airdamien/FXPAN/docs/fxpan_body_fit.png

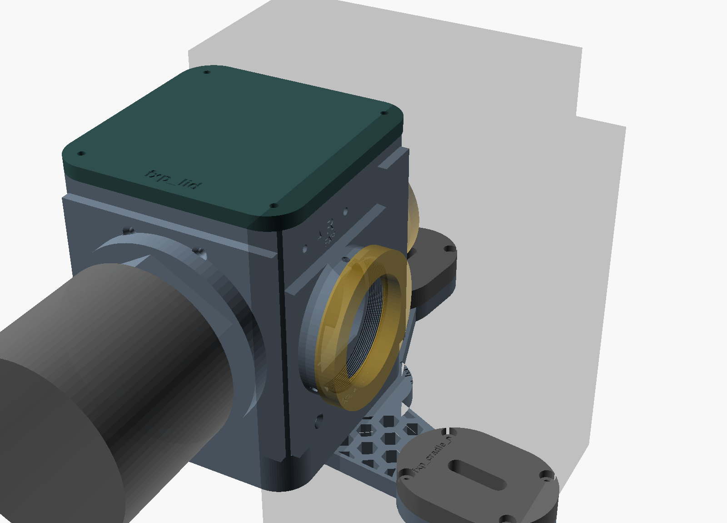
docs/fxpan_body_fit.png
