airdamien/FXPAN/docs/kraken/countryside.jpg

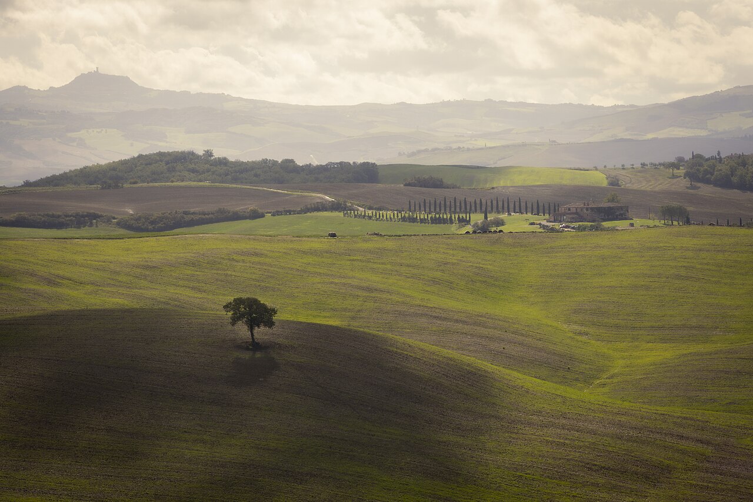
docs/kraken/countryside.jpg
