airdamien/FXPAN/docs/kraken/schlieren_paths.png

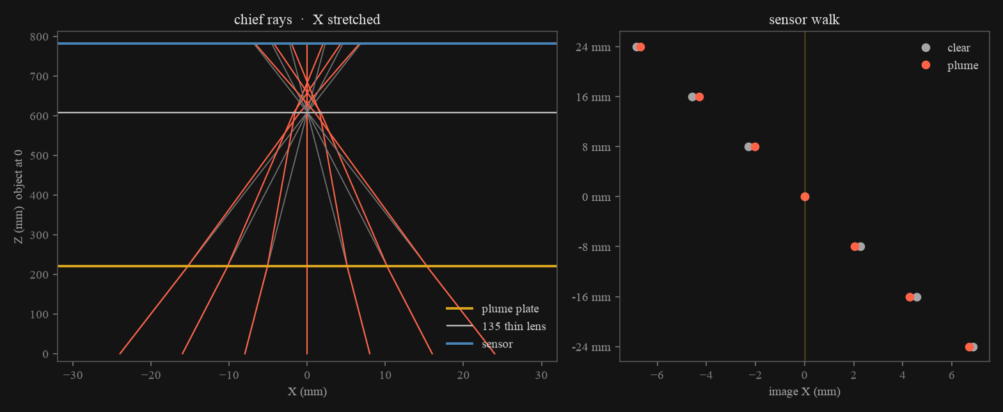
docs/kraken/schlieren_paths.png
