airdamien/FXPAN/docs/kraken/settles_bullet.jpg

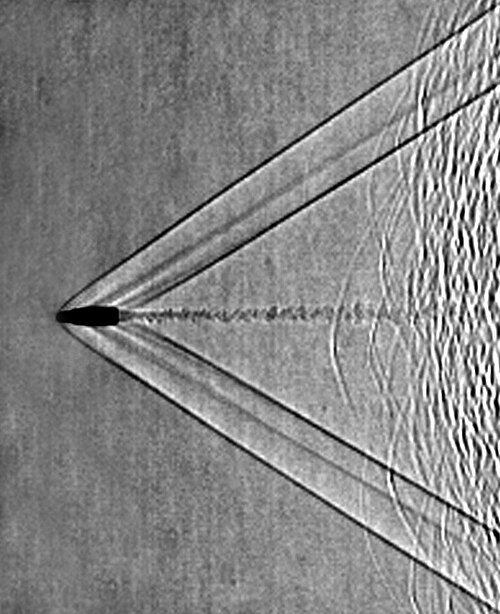
docs/kraken/settles_bullet.jpg
