airdamien/FXPAN/docs/monitor/midas-hdmi-ctp.png

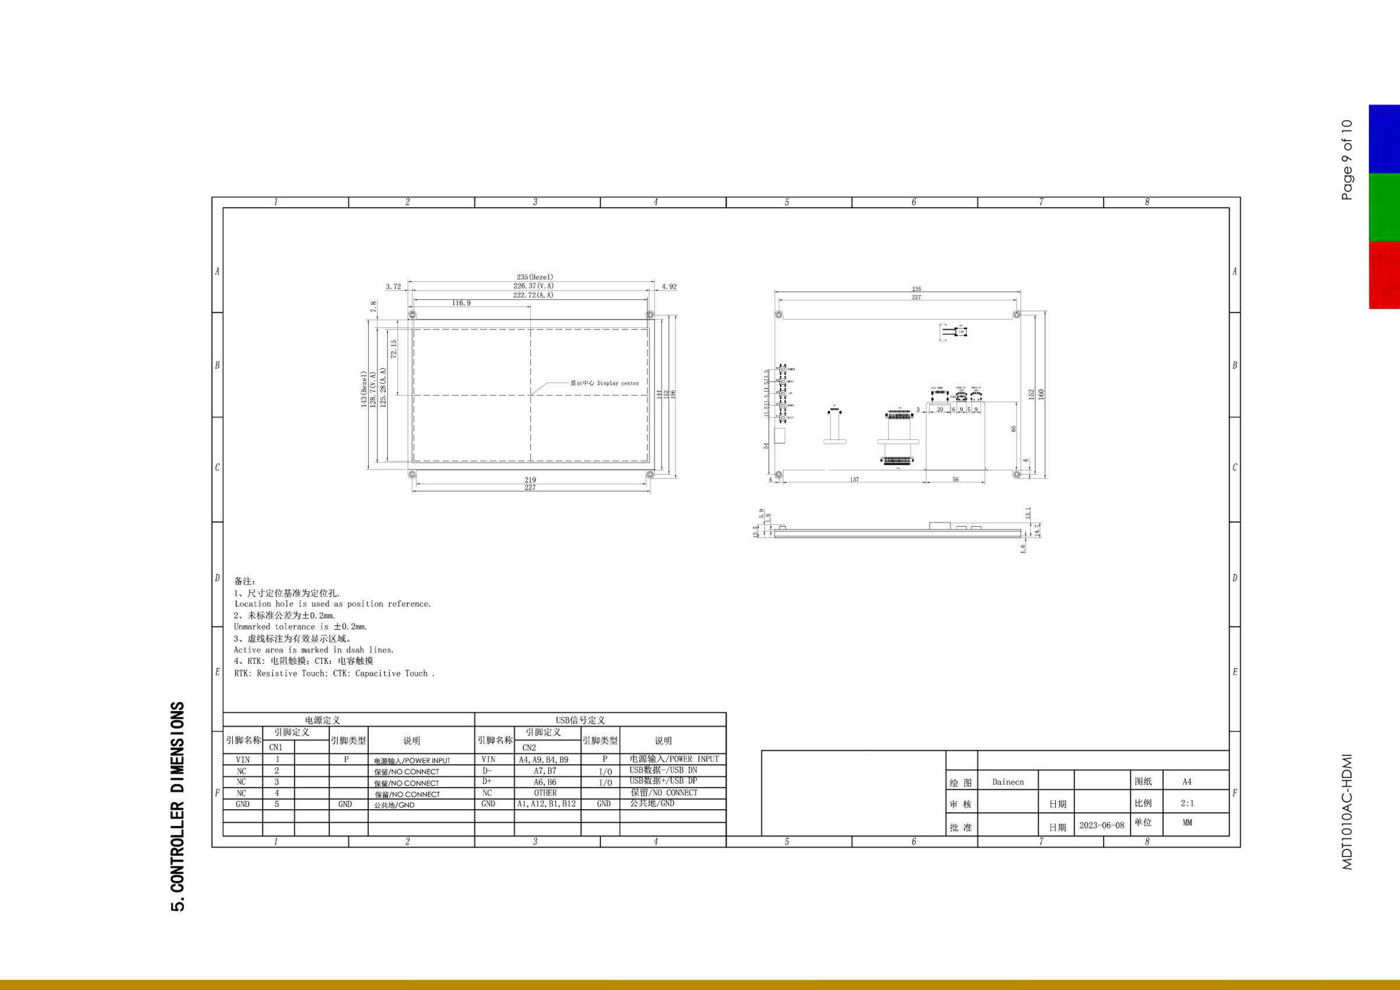
docs/monitor/midas-hdmi-ctp.png
