airdamien/FXPAN/docs/monitor/waveshare-panel.png

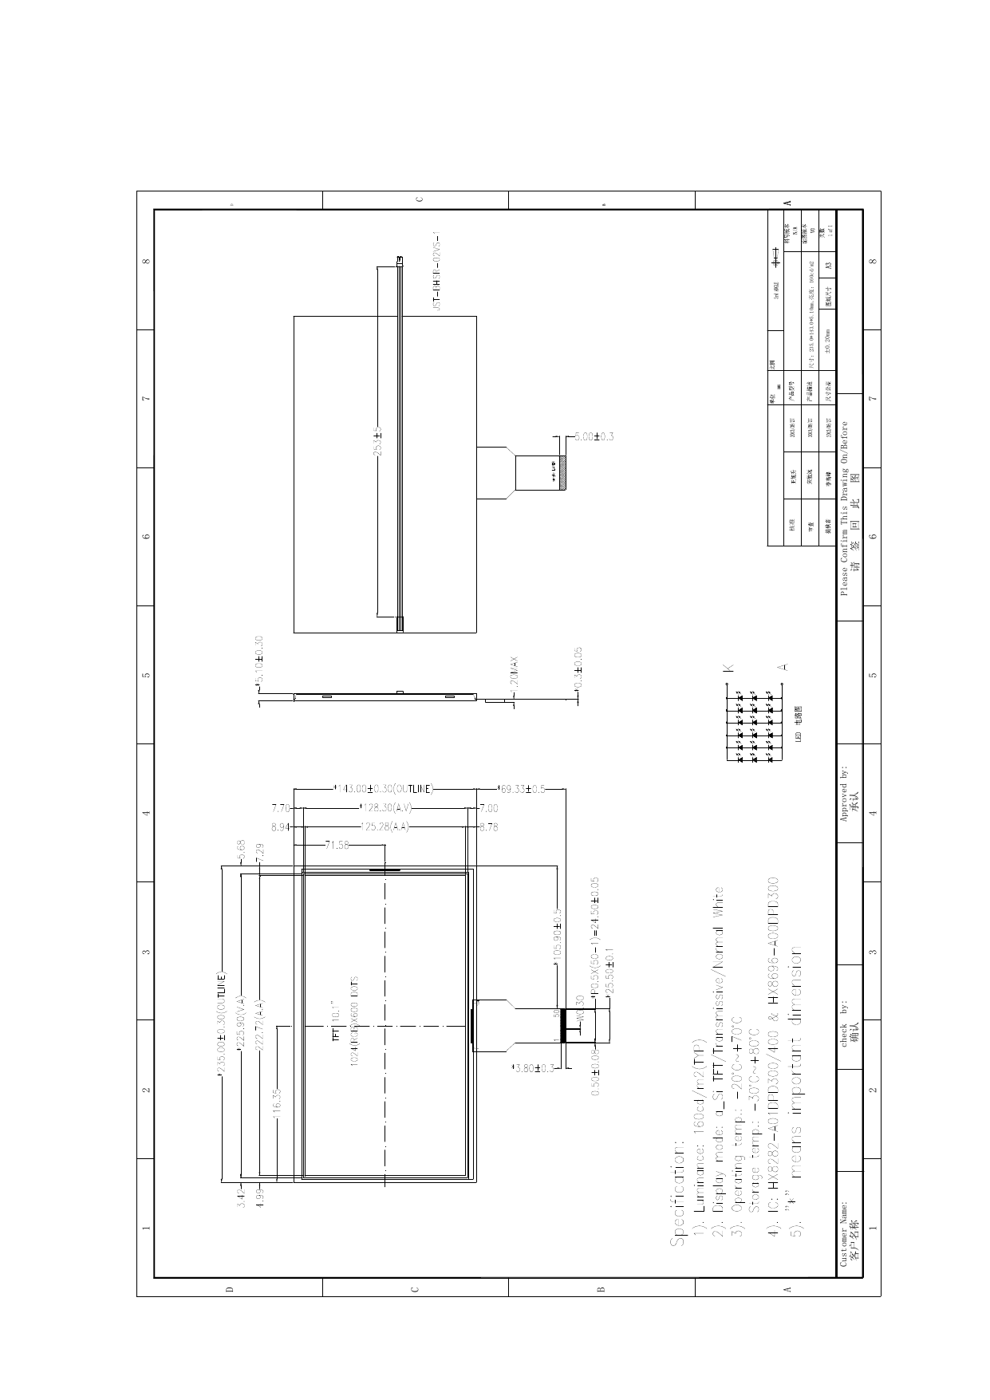
docs/monitor/waveshare-panel.png
