airdamien/FXPAN/ios/FXPAN/Samples/P_20261002195445.jpg

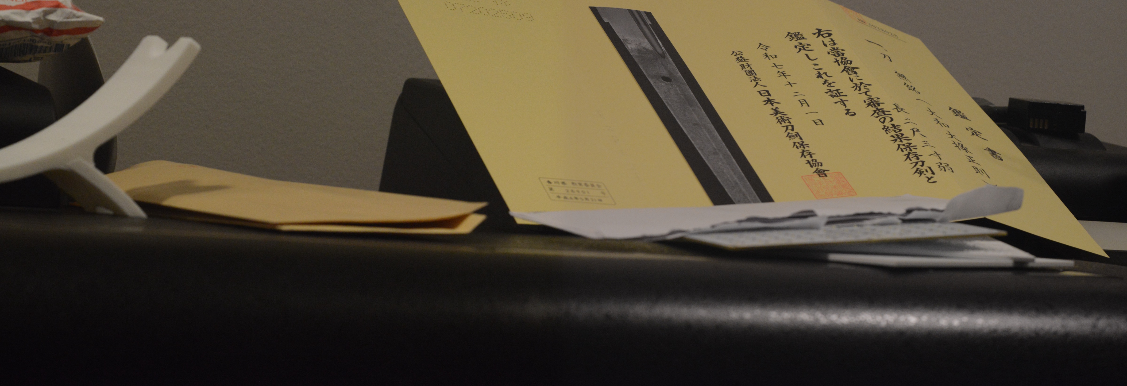
ios/FXPAN/Samples/P_20261002195445.jpg
