airdamien/FXPAN/ios/FXPAN/Samples/P_20261002201628.jpg

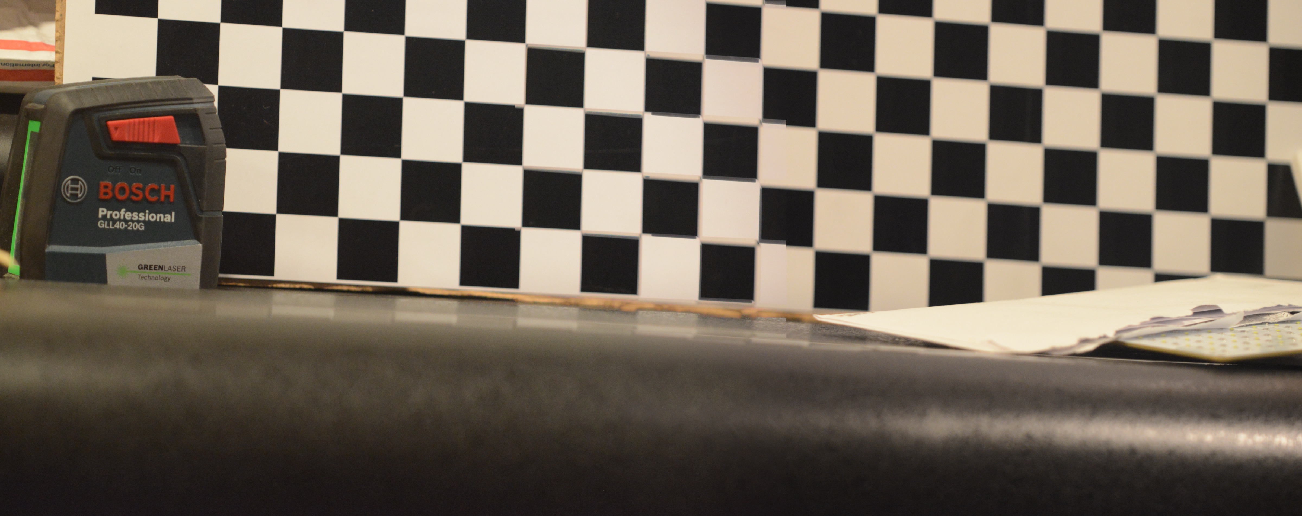
ios/FXPAN/Samples/P_20261002201628.jpg
