airdamien/FXPAN/ios/FXPAN/Samples/P_20261002201952.jpg

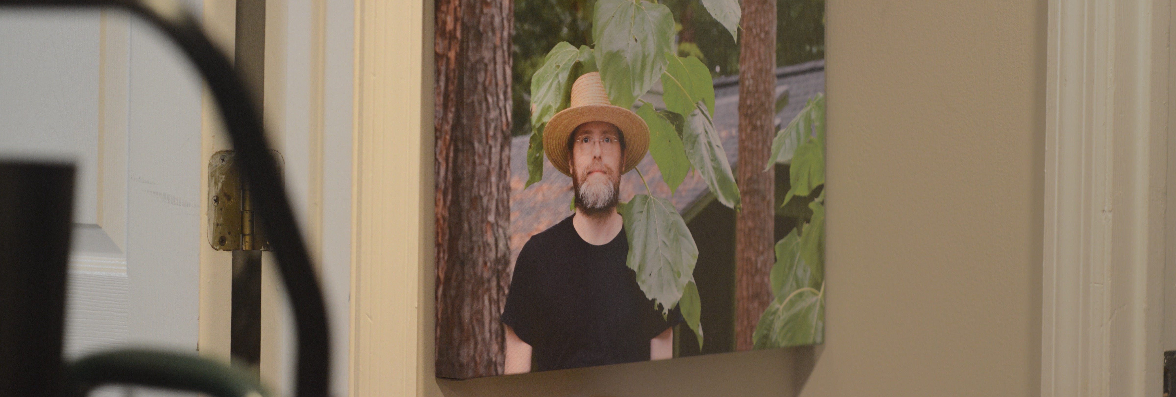
ios/FXPAN/Samples/P_20261002201952.jpg
