airdamien/FXPAN/openscad/hybrid_shift/preview.png

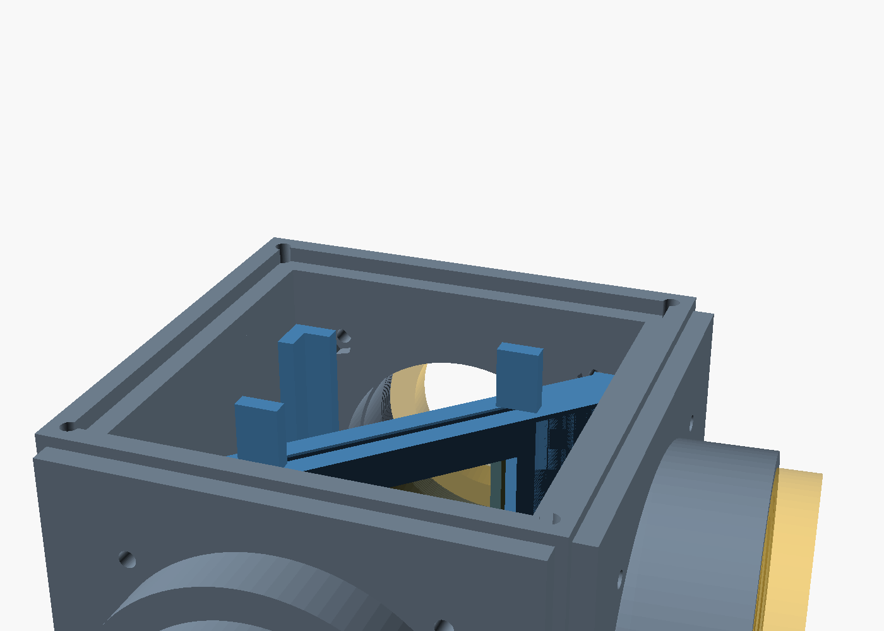
openscad/hybrid_shift/preview.png
