airdamien/FXPAN/logos/fxpan_fx_gold.stl

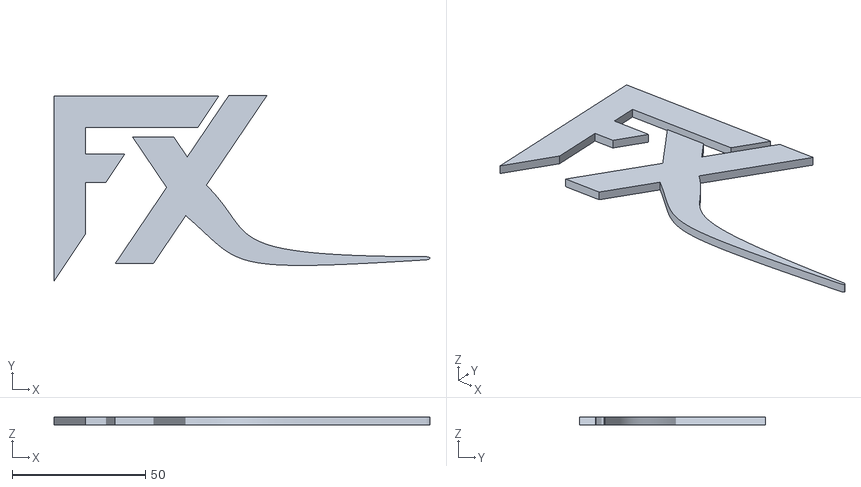
[picture p83: CAD file, 2026-09-20]
logos/fxpan_fx_gold.stl
141.0 x 69.6 x 3.00
