airdamien/FXPAN/openscad/monitor/case-bottom.stl

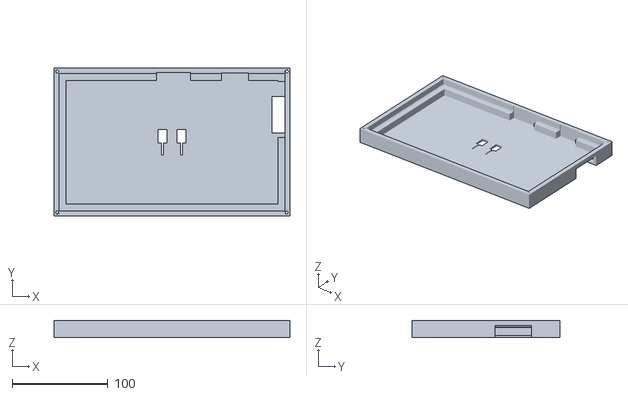
[picture p84: CAD file, 2026-09-13]
openscad/monitor/case-bottom.stl
246.1 x 154.0 x 18.2
