airdamien/FXPAN/openscad/taking_lens.stl

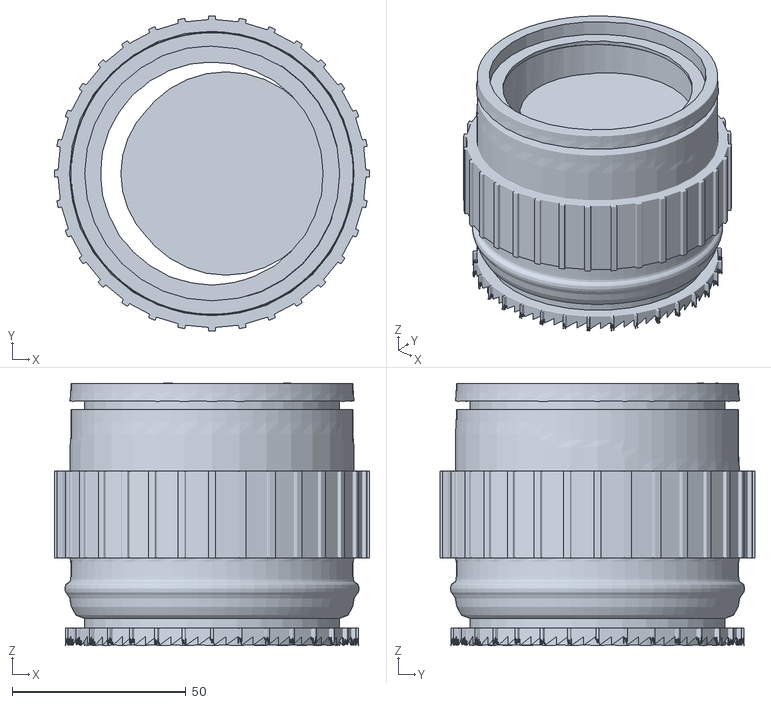
[picture p85: CAD file, 2026-09-12]
openscad/taking_lens.stl
90.8 x 90.8 x 75.7
