airdamien/FXPAN/stls/fxpan/lid.stl

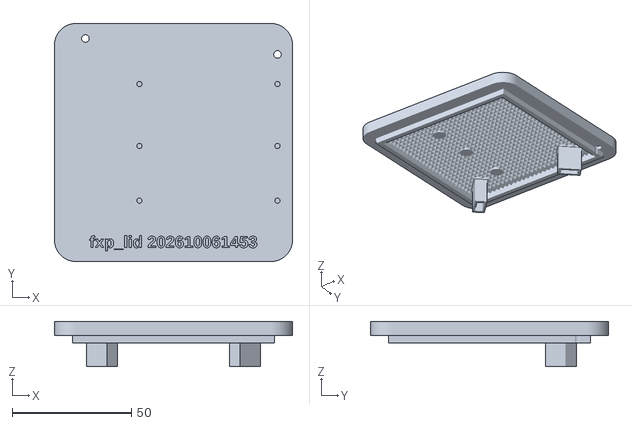
[picture p86: CAD file, 2026-10-06]
stls/fxpan/lid.stl
100.0 x 100.0 x 19.0
