airdamien/FXPAN/stls/hybrid/arm_t_s.stl

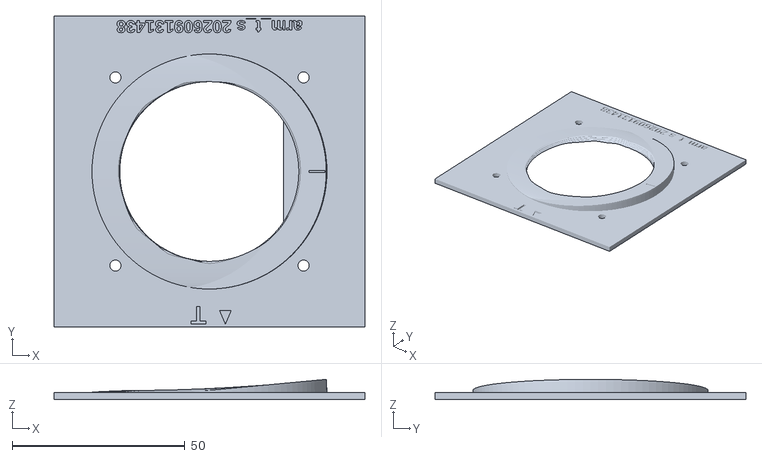
[picture p87: CAD file, 2026-09-13]
stls/hybrid/arm_t_s.stl
90.0 x 90.0 x 5.87
