airdamien/FXPAN/stls/hybrid_shift/chassis_logo.stl

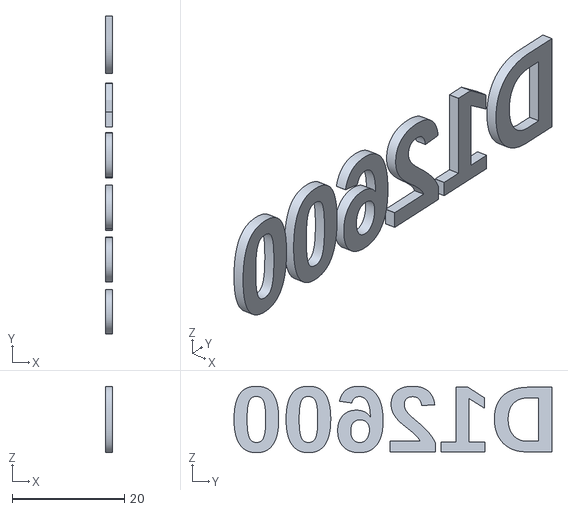
[picture p88: CAD file, 2026-09-17]
stls/hybrid_shift/chassis_logo.stl
1.30 x 56.6 x 11.8
