airdamien/FXPAN/stls/hybrid_shift_fx/stem_el180_inf.stl

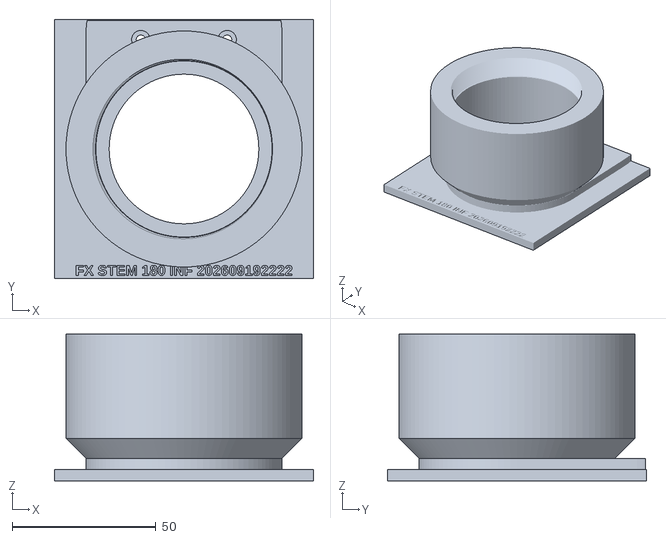
[picture p89: CAD file, 2026-09-20]
stls/hybrid_shift_fx/stem_el180_inf.stl
90.0 x 90.0 x 51.0
