airdamien/FXPAN/stls/isco/isco_clamp_nw.stl

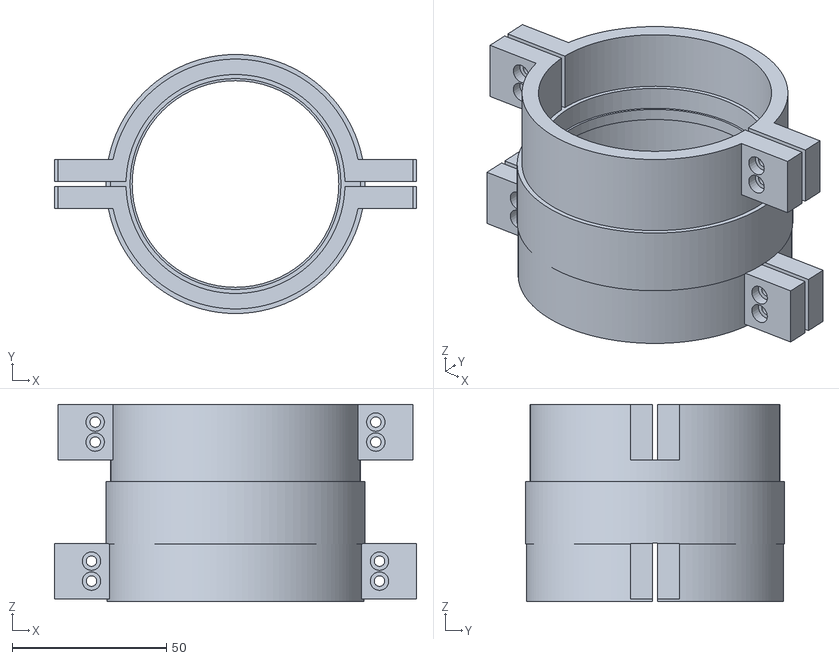
[picture p90: CAD file, 2026-09-26]
stls/isco/isco_clamp_nw.stl
117.4 x 84.0 x 64.0
