airdamien/FXPAN/stls/phone/duo_shoe.stl

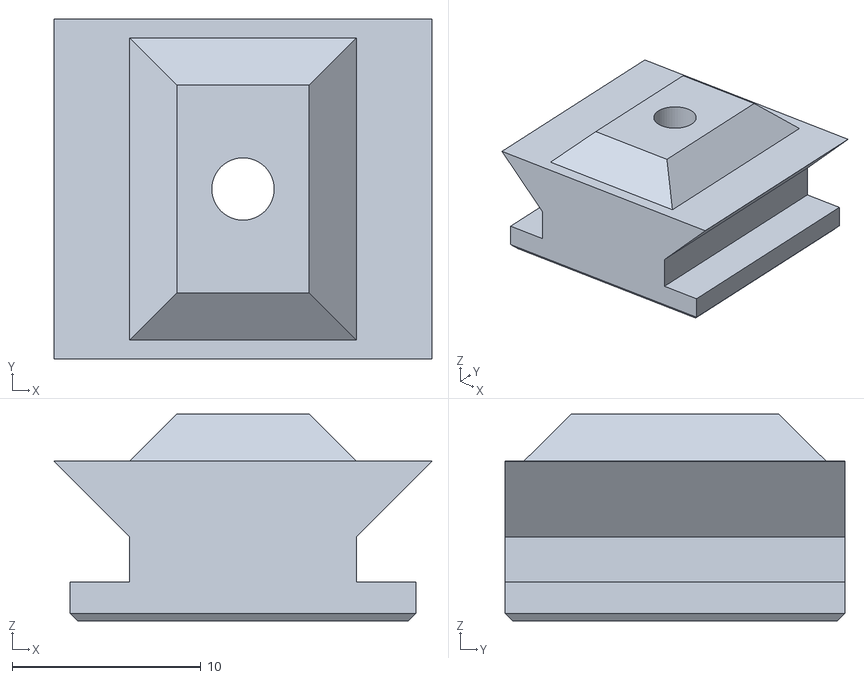
[picture p91: CAD file, 2026-10-06]
stls/phone/duo_shoe.stl
20.0 x 18.0 x 10.9
