airdamien/FXPAN/stls/tools/focus_sled.stl

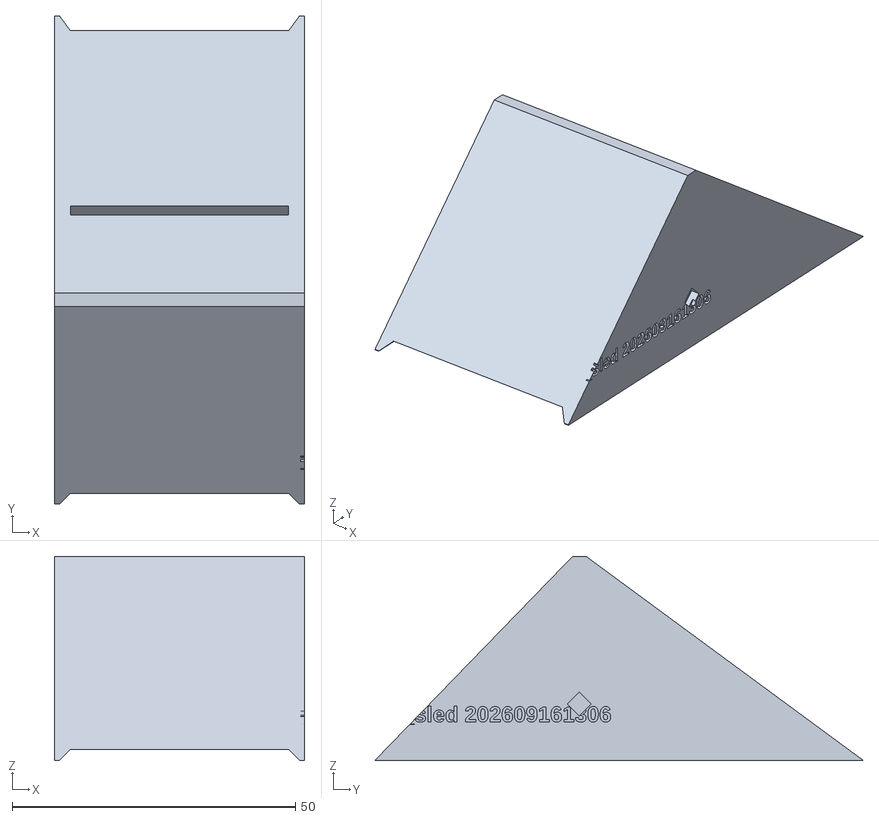
[picture p92: CAD file, 2026-09-16]
stls/tools/focus_sled.stl
44.2 x 86.1 x 36.0
