airdamien/FXPAN/stls/v/arm_r_f.stl

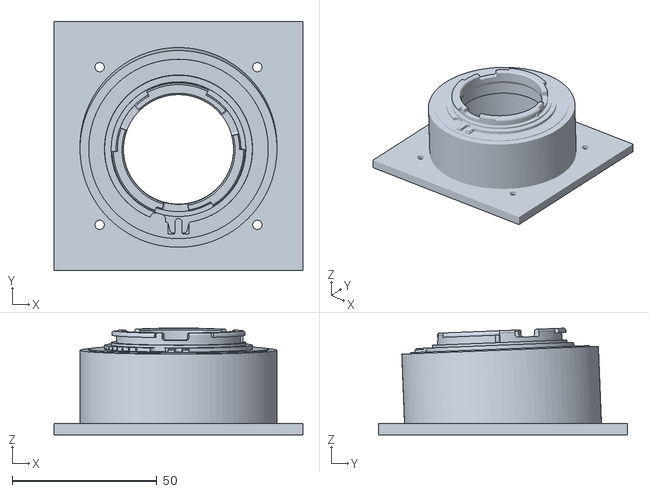
[picture p93: CAD file, 2026-09-12]
stls/v/arm_r_f.stl
86.0 x 86.0 x 36.9
