airdamien/FXPAN/logos/fxpan_outline_red.stl

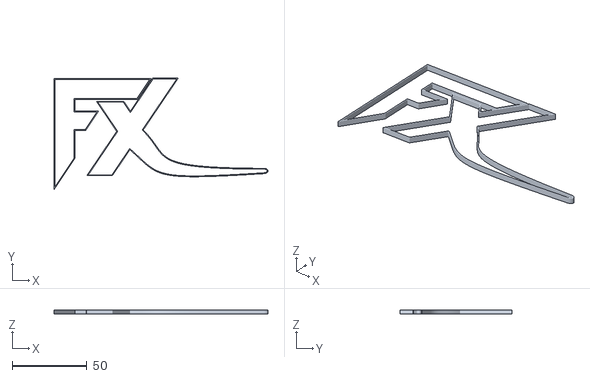
[picture p94: CAD file, 2026-09-20]
logos/fxpan_outline_red.stl
143.4 x 74.8 x 3.00
