airdamien/FXPAN/openscad/d7000_body.stl

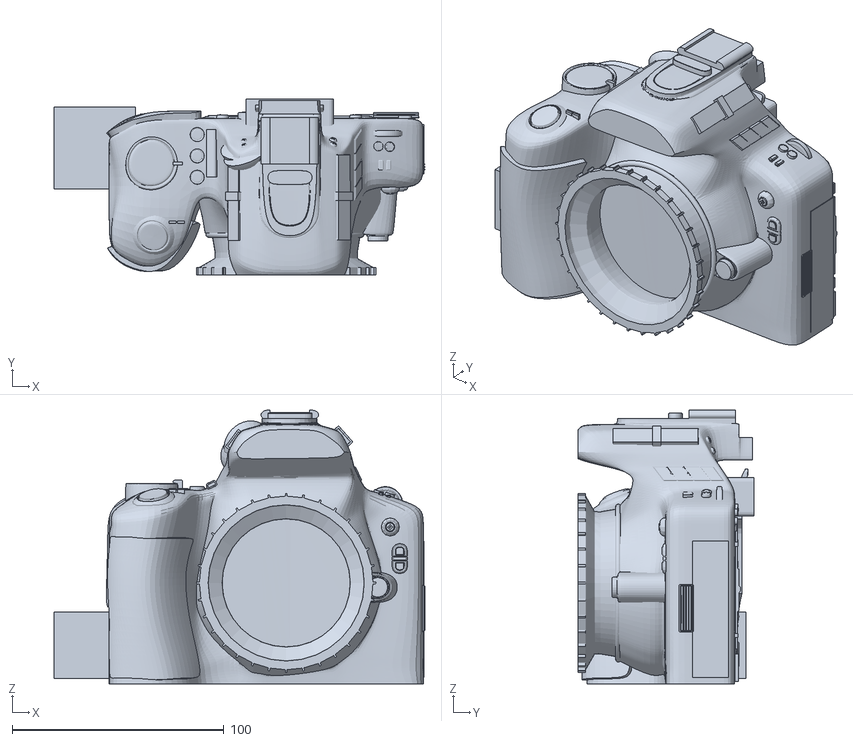
[picture p95: CAD file, 2026-09-12]
openscad/d7000_body.stl
175.0 x 82.9 x 129.1
