airdamien/FXPAN/openscad/monitor/wall_mount.stl

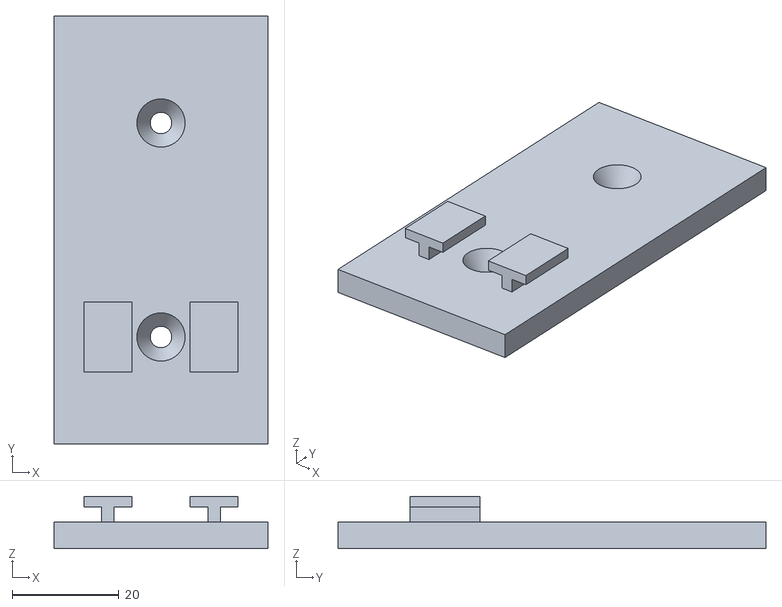
[picture p96: CAD file, 2026-09-13]
openscad/monitor/wall_mount.stl
40.0 x 80.0 x 9.76
