airdamien/FXPAN/stls/fxpan/lid_inner.stl

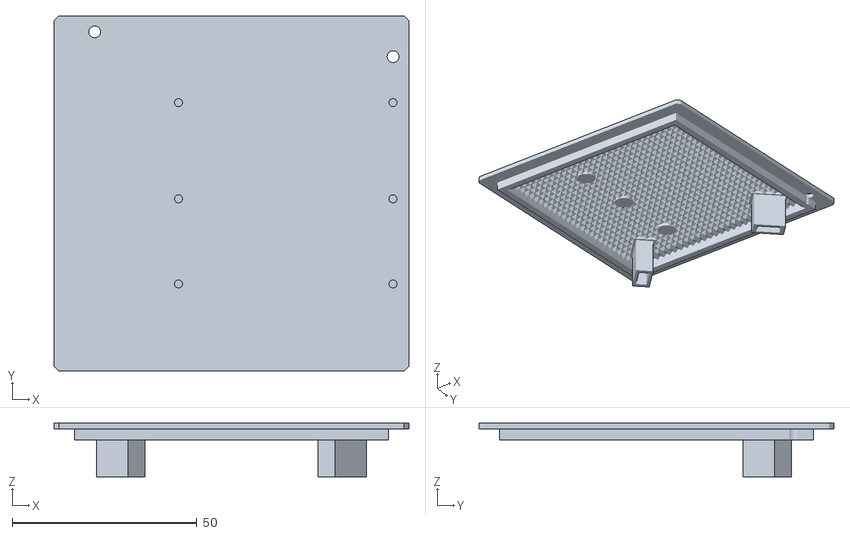
[picture p97: CAD file, 2026-10-06]
stls/fxpan/lid_inner.stl
96.0 x 96.0 x 14.6
