airdamien/FXPAN/stls/hybrid_shift/chassis_outer.stl

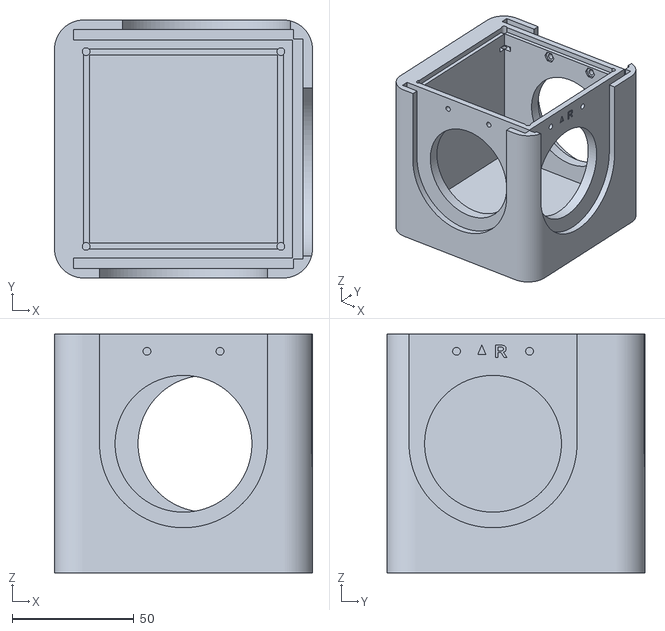
[picture p98: CAD file, 2026-09-17]
stls/hybrid_shift/chassis_outer.stl
106.0 x 106.0 x 98.0
