airdamien/FXPAN/stls/hybrid_shift_fx/stem_el180_inf_inner.stl

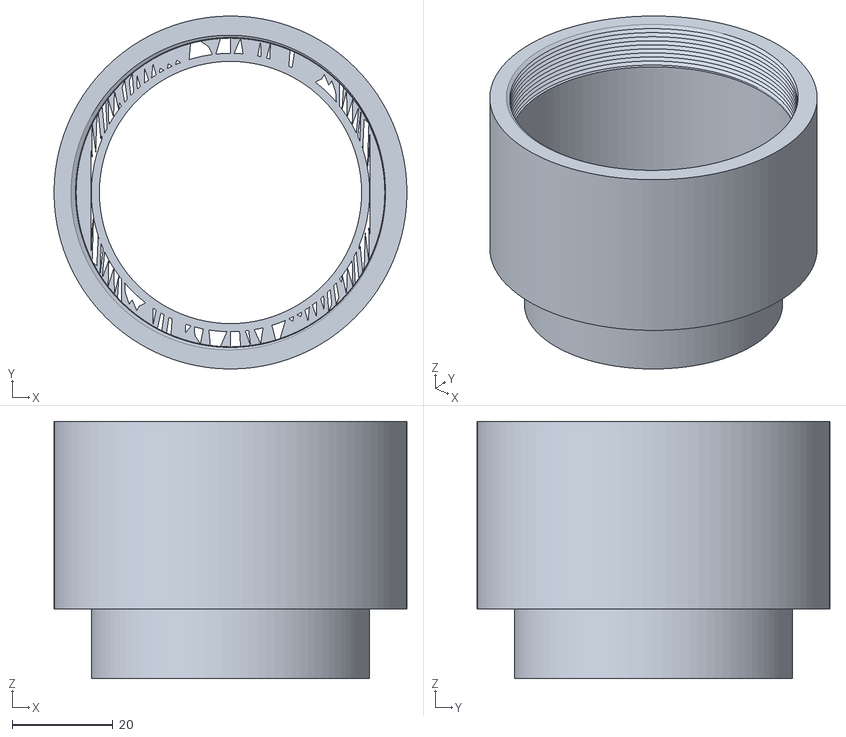
[picture p99: CAD file, 2026-09-20]
stls/hybrid_shift_fx/stem_el180_inf_inner.stl
70.0 x 70.0 x 51.0
