airdamien/FXPAN/stls/isco/isco_stand.stl

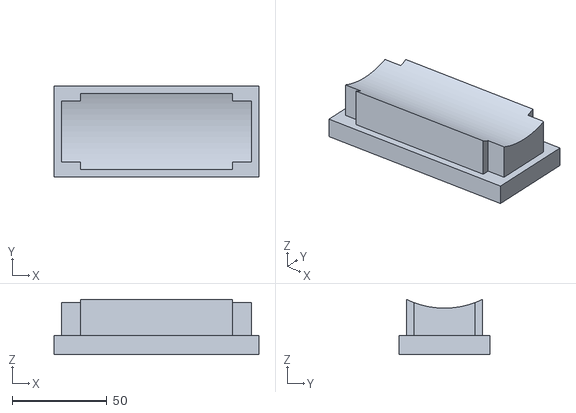
[picture p100: CAD file, 2026-09-24]
stls/isco/isco_stand.stl
108.0 x 48.0 x 29.1
