airdamien/FXPAN/stls/monitor/display_mount.stl

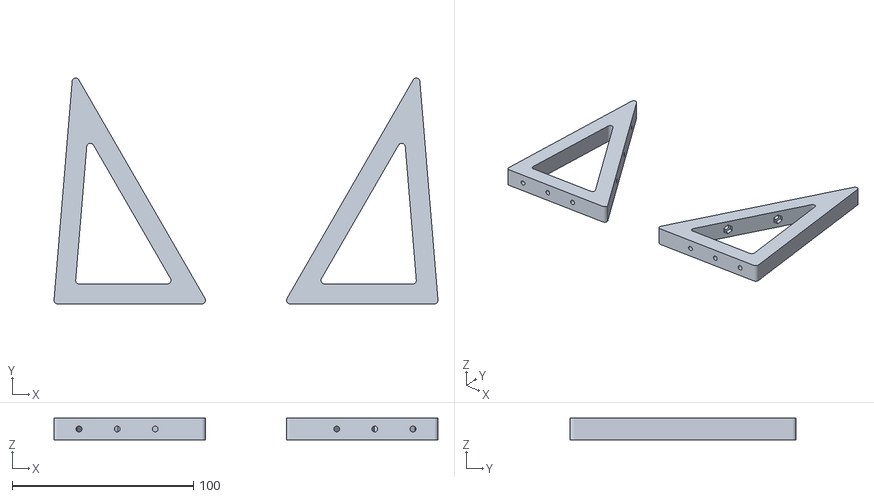
[picture p101: CAD file, 2026-09-13]
stls/monitor/display_mount.stl
211.6 x 124.4 x 12.0
