airdamien/FXPAN/stls/phone/duo_tray_bare.stl

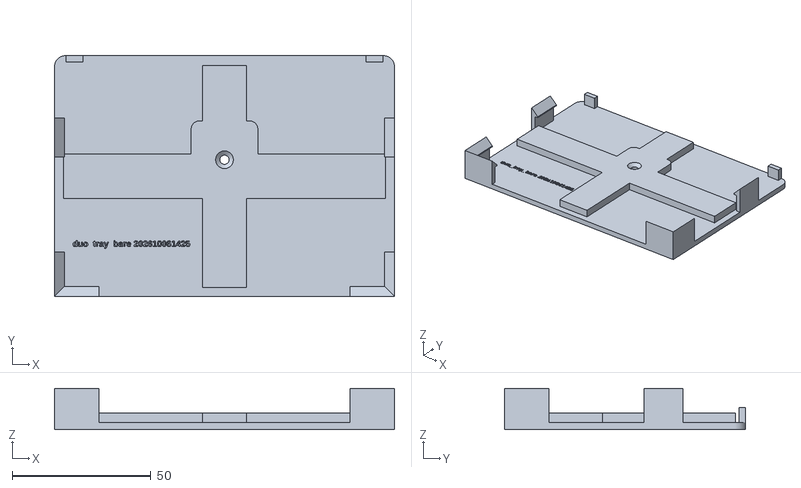
[picture p102: CAD file, 2026-10-06]
stls/phone/duo_tray_bare.stl
122.4 x 86.7 x 14.9
