airdamien/FXPAN/logos/fxpan_pan_white.stl

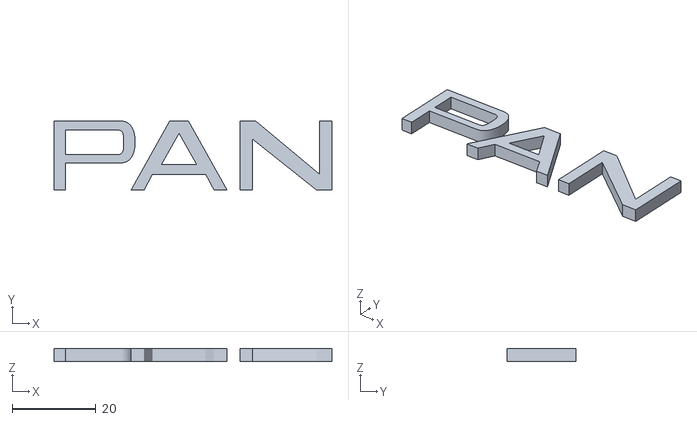
[picture p103: CAD file, 2026-09-20]
logos/fxpan_pan_white.stl
66.5 x 16.5 x 3.00
