airdamien/FXPAN/stls/fxpan/arm_r_wl_inner.stl

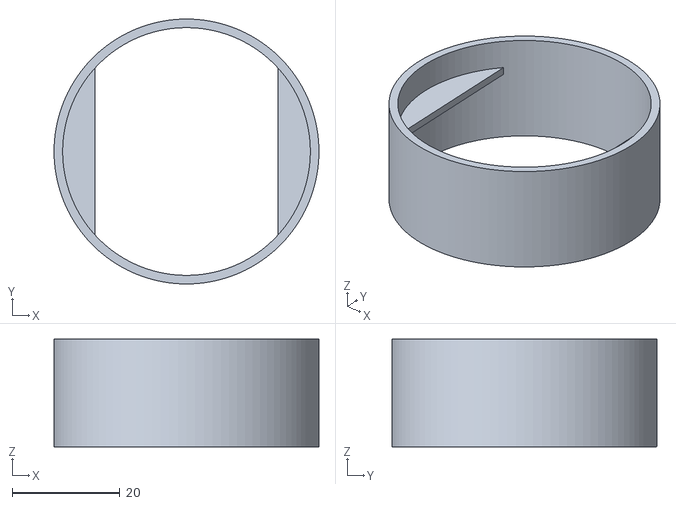
[picture p104: CAD file, 2026-10-06]
stls/fxpan/arm_r_wl_inner.stl
49.2 x 49.2 x 20.0
