airdamien/FXPAN/stls/hybrid/stem_f50.stl

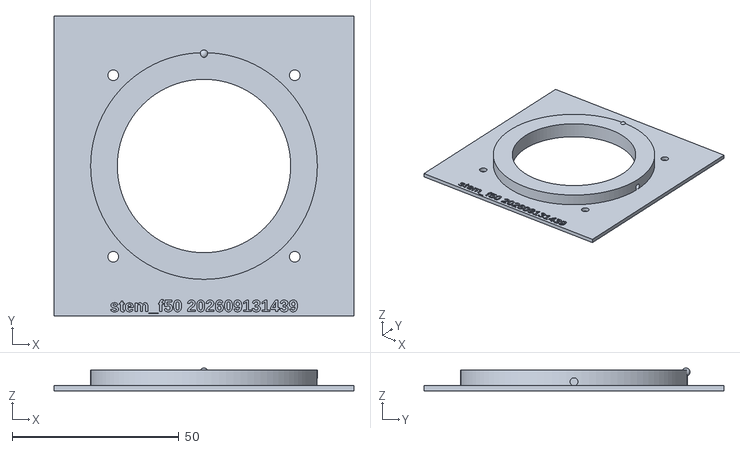
[picture p105: CAD file, 2026-09-13]
stls/hybrid/stem_f50.stl
90.0 x 90.0 x 6.90
