airdamien/FXPAN/stls/hybrid_shift_fx/arm_t_outer.stl

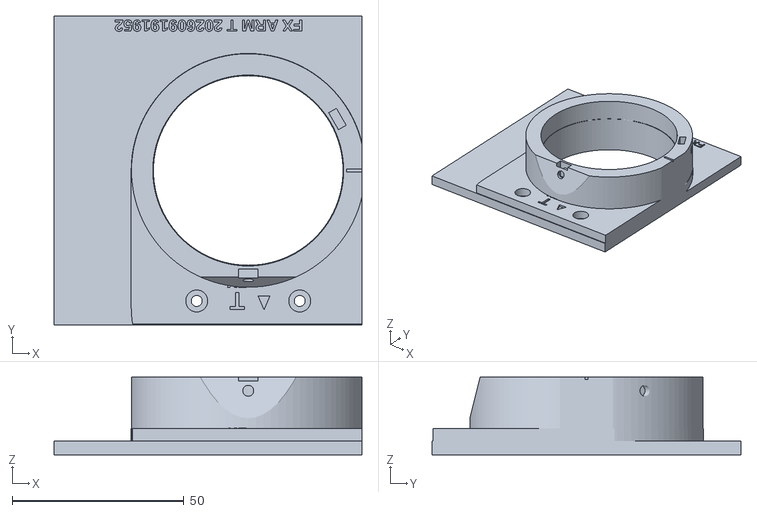
[picture p106: CAD file, 2026-09-20]
stls/hybrid_shift_fx/arm_t_outer.stl
89.6 x 90.0 x 22.7
