airdamien/FXPAN/stls/isco/el_nikkor_180n.stl

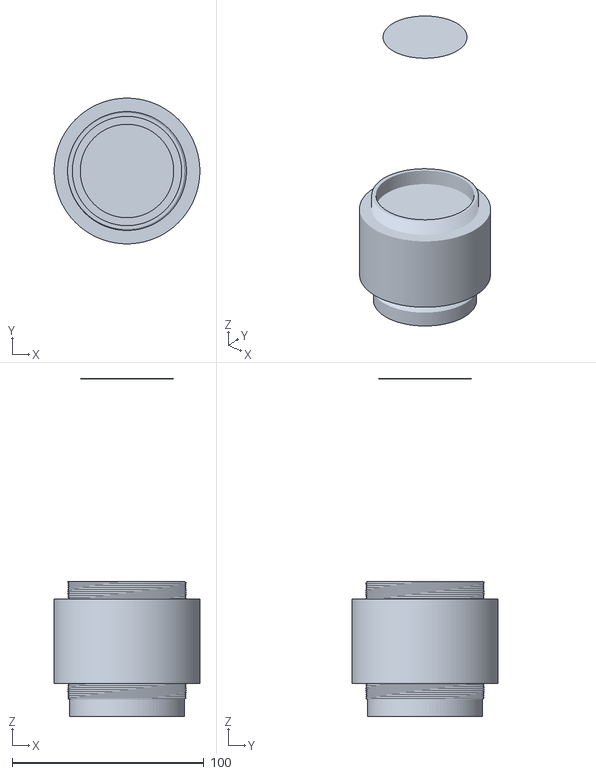
[picture p107: CAD file, 2026-09-24]
stls/isco/el_nikkor_180n.stl
76.0 x 76.0 x 176.3
