airdamien/FXPAN/stls/phone/duo_tray_cased.stl

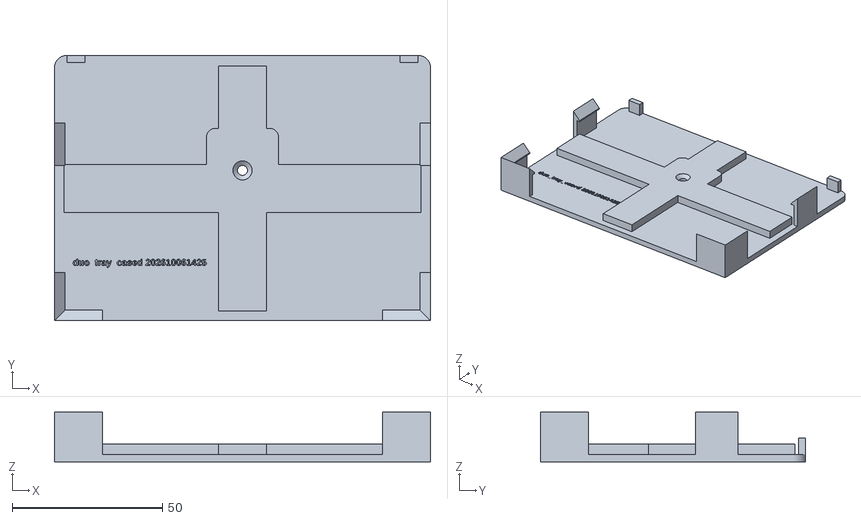
[picture p108: CAD file, 2026-10-06]
stls/phone/duo_tray_cased.stl
125.0 x 88.1 x 16.5
