airdamien/FXPAN/stls/fxpan/arm_r_wl_outer.stl

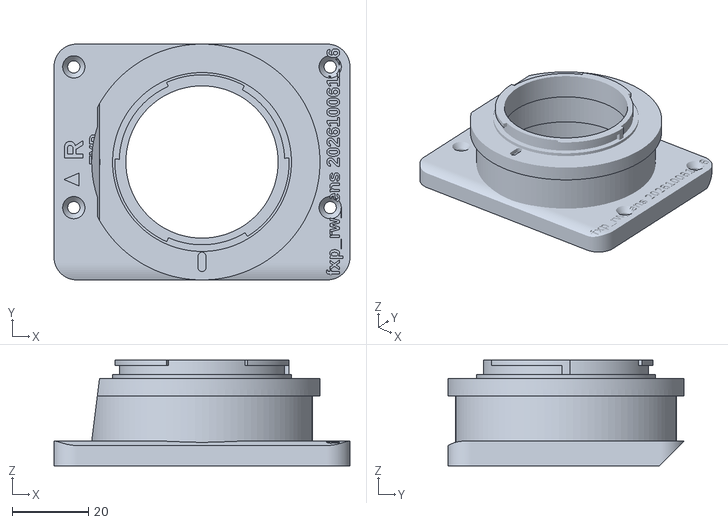
[picture p109: CAD file, 2026-10-06]
stls/fxpan/arm_r_wl_outer.stl
77.8 x 62.0 x 27.8
