airdamien/FXPAN/stls/hybrid_shift/arm_r_f.stl

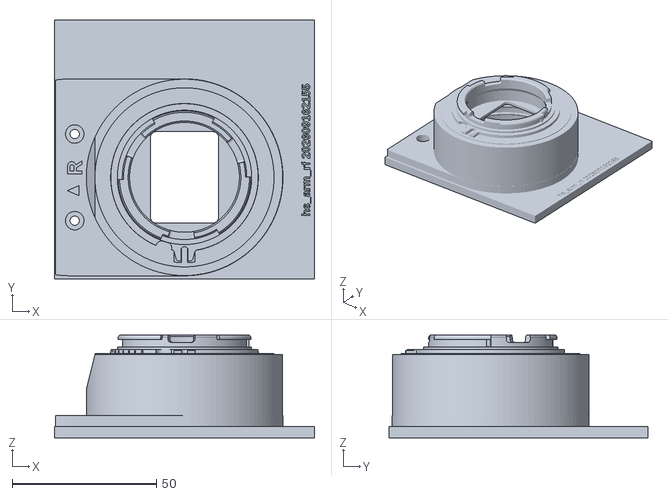
[picture p110: CAD file, 2026-09-17]
stls/hybrid_shift/arm_r_f.stl
90.0 x 89.6 x 35.6
