airdamien/FXPAN/stls/hybrid_shift_fx/arm_t.stl

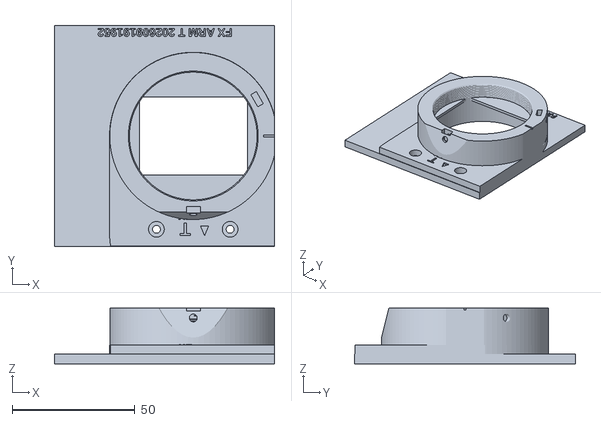
[picture p111: CAD file, 2026-09-20]
stls/hybrid_shift_fx/arm_t.stl
89.6 x 90.0 x 22.7
