airdamien/FXPAN/stls/isco/isco_ultrastar.stl

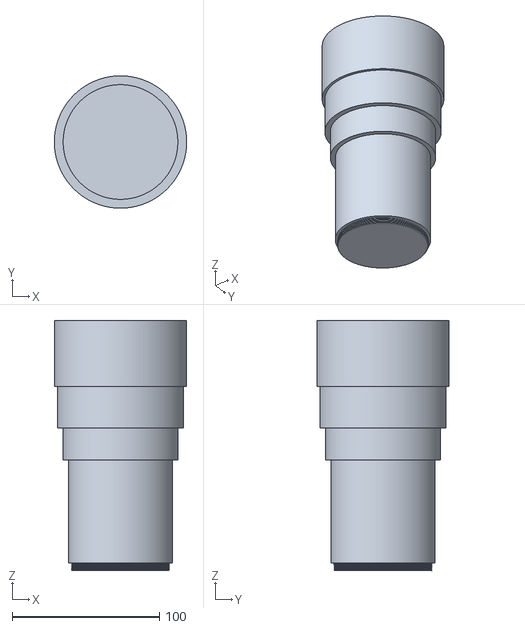
[picture p112: CAD file, 2026-09-24]
stls/isco/isco_ultrastar.stl
90.0 x 90.0 x 170.0
