airdamien/FXPAN/stls/phone/pm17_cradle.stl

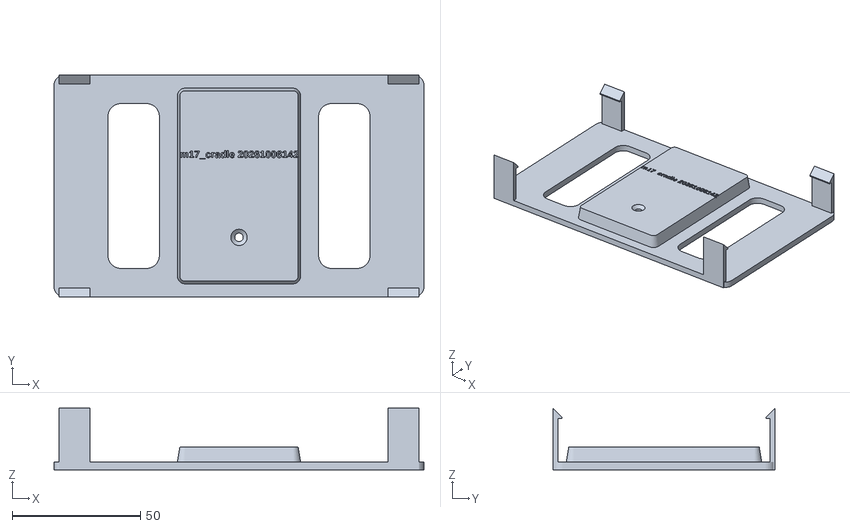
[picture p113: CAD file, 2026-10-06]
stls/phone/pm17_cradle.stl
144.0 x 86.4 x 24.0
