airdamien/FXPAN/stls/v/chassis.stl

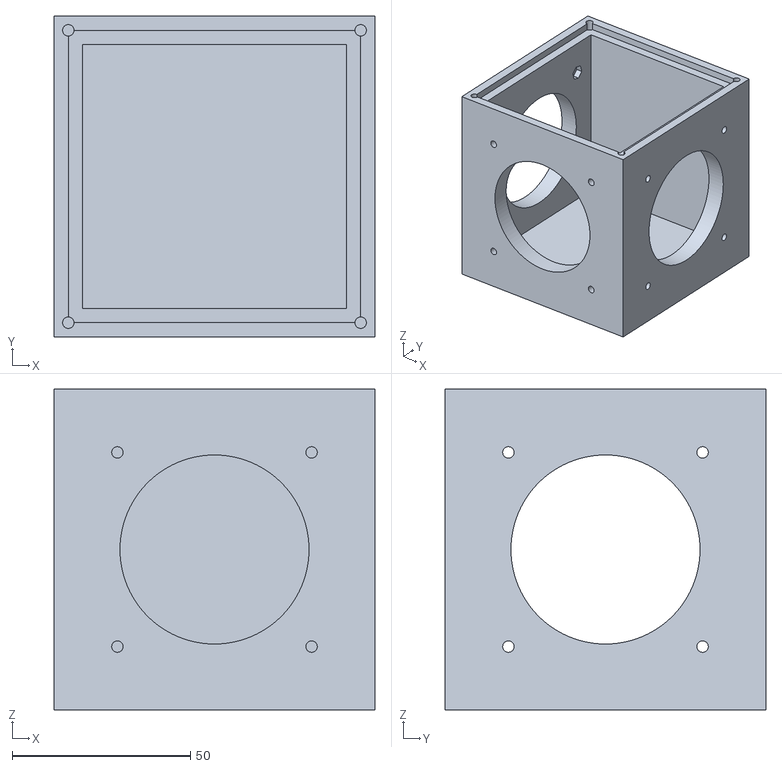
[picture p114: CAD file, 2026-09-12]
stls/v/chassis.stl
90.0 x 90.0 x 90.0
