airdamien/FXPAN/stls/fxpan/arm_r_wl.stl

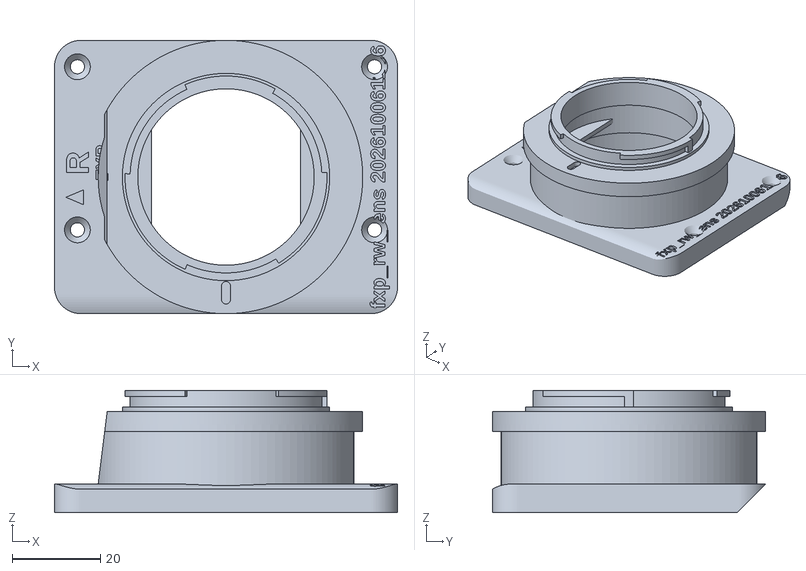
[picture p115: CAD file, 2026-10-06]
stls/fxpan/arm_r_wl.stl
77.8 x 62.0 x 27.8
