airdamien/FXPAN/stls/hybrid/arm_r_s.stl

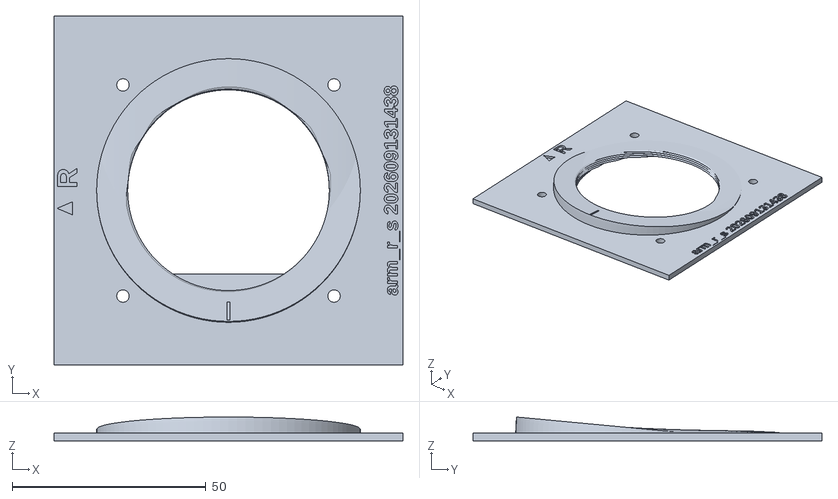
[picture p116: CAD file, 2026-09-13]
stls/hybrid/arm_r_s.stl
90.0 x 90.0 x 6.18
