airdamien/FXPAN/stls/hybrid_shift_fx/arm_t_inner.stl

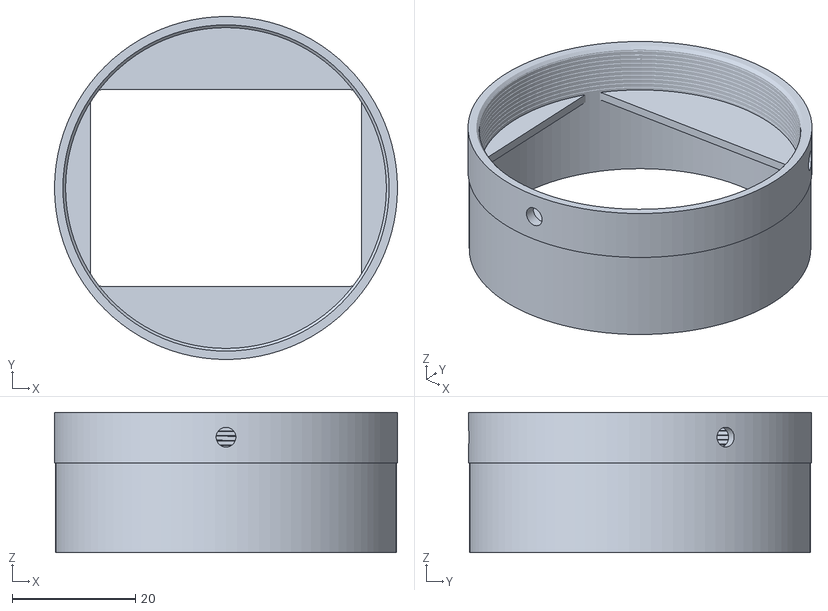
[picture p117: CAD file, 2026-09-20]
stls/hybrid_shift_fx/arm_t_inner.stl
55.6 x 55.6 x 22.7
