airdamien/FXPAN/stls/v/lid.stl

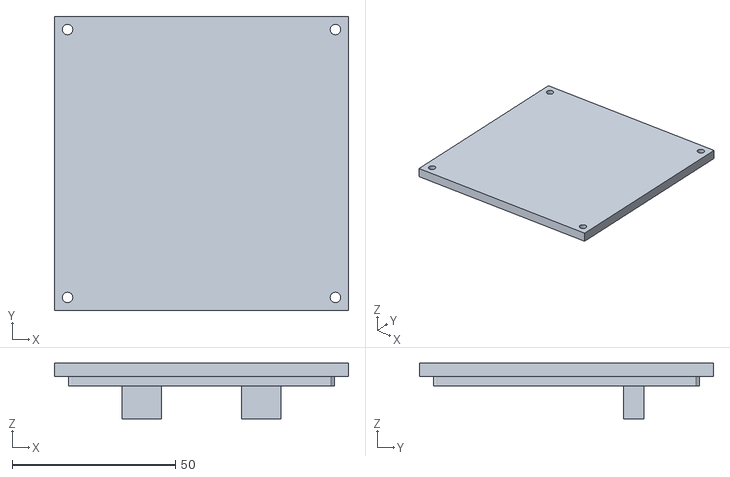
[picture p118: CAD file, 2026-09-12]
stls/v/lid.stl
90.0 x 90.0 x 17.0
