airdamien/FXPAN/stls/bsplit/bs_tray.stl

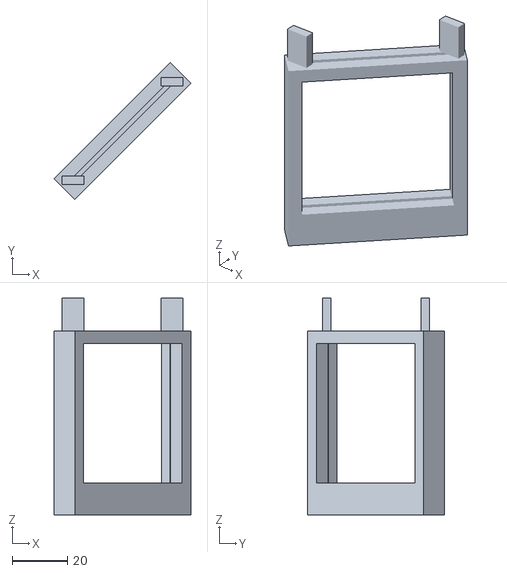
[picture p119: CAD file, 2026-09-12]
stls/bsplit/bs_tray.stl
49.8 x 49.8 x 78.8
