airdamien/FXPAN/stls/fxpan/arm_t_wl_outer.stl

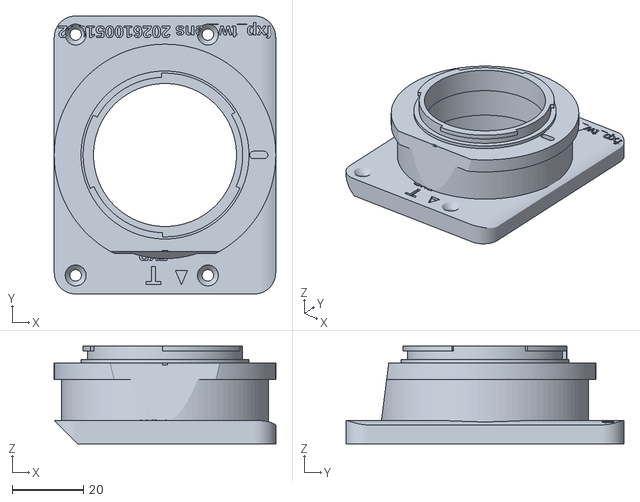
[picture p120: CAD file, 2026-10-06]
stls/fxpan/arm_t_wl_outer.stl
62.0 x 77.8 x 27.4
