airdamien/FXPAN/stls/hybrid_shift/brace.stl

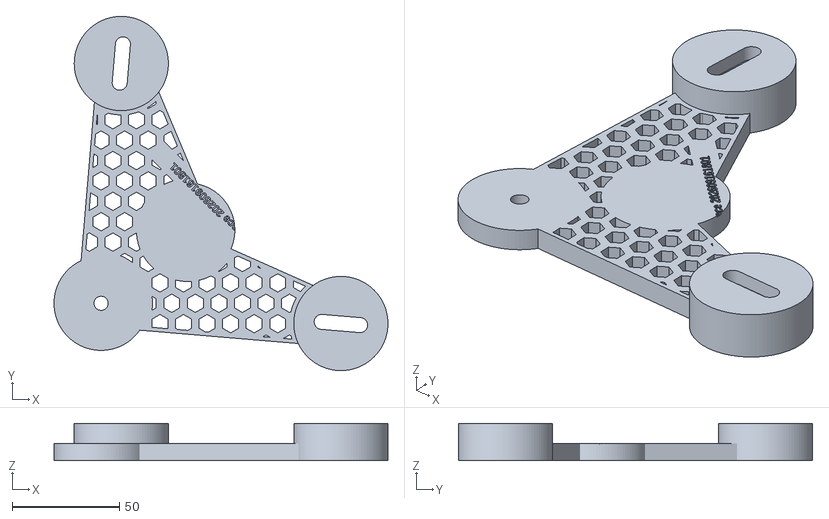
[picture p121: CAD file, 2026-09-16]
stls/hybrid_shift/brace.stl
156.0 x 165.4 x 17.4
