airdamien/FXPAN/stls/v/mirror_tray.stl

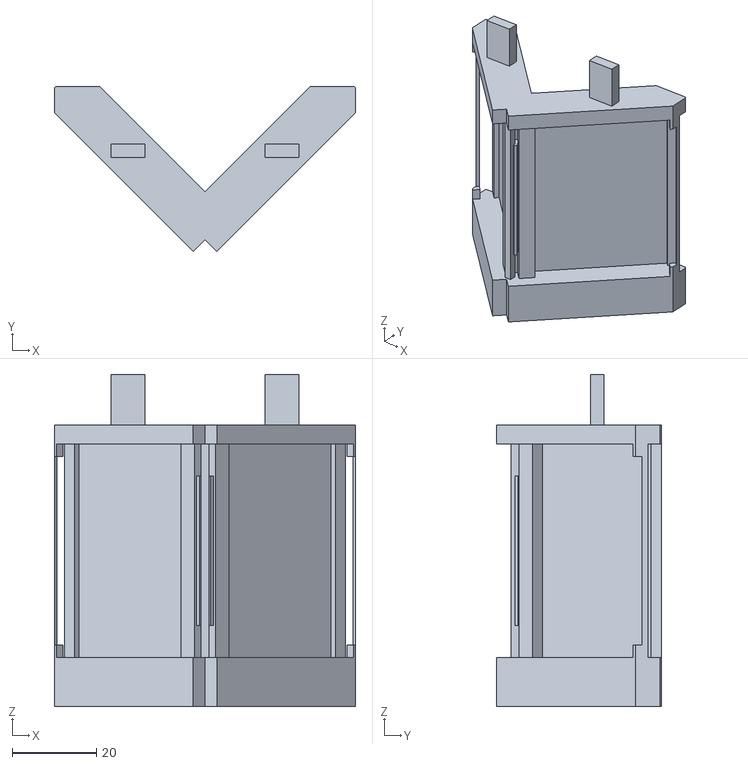
[picture p122: CAD file, 2026-09-12]
stls/v/mirror_tray.stl
71.6 x 39.2 x 78.9
