airdamien/FXPAN/stls/fxpan/chassis.stl

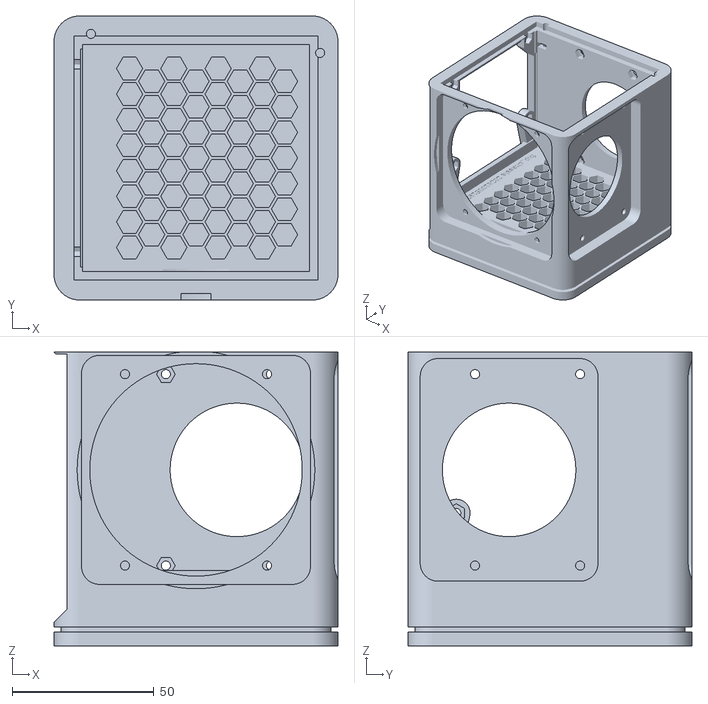
[picture p123: CAD file, 2026-10-06]
stls/fxpan/chassis.stl
100.0 x 100.0 x 103.5
