airdamien/FXPAN/stls/hybrid_shift/arm_t_f_inner.stl

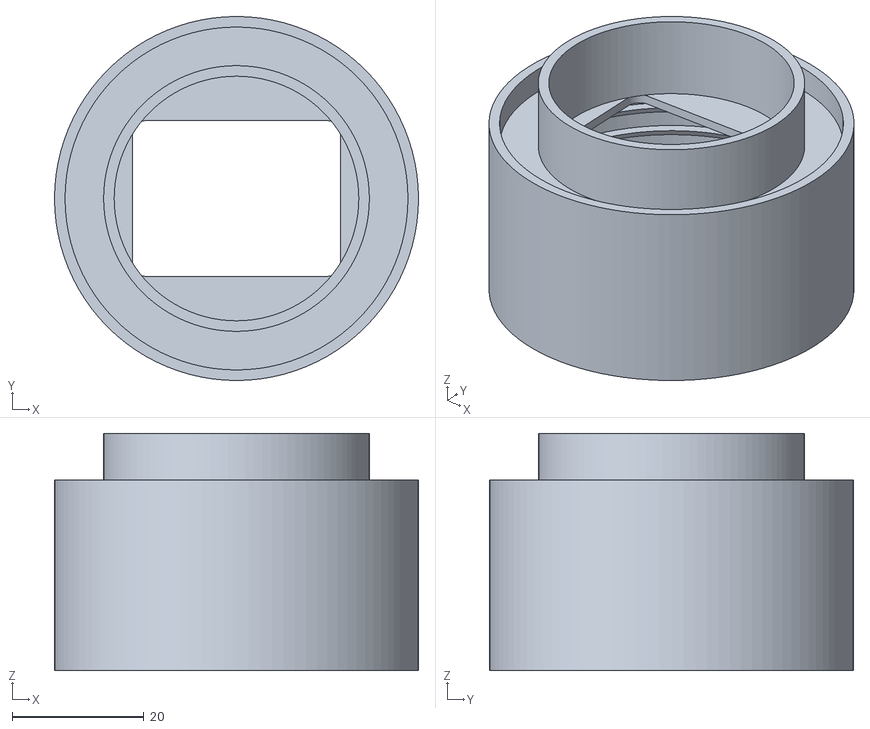
[picture p124: CAD file, 2026-09-16]
stls/hybrid_shift/arm_t_f_inner.stl
55.2 x 55.2 x 36.0
