airdamien/FXPAN/stls/hybrid_shift_fx/arm_r_inner.stl

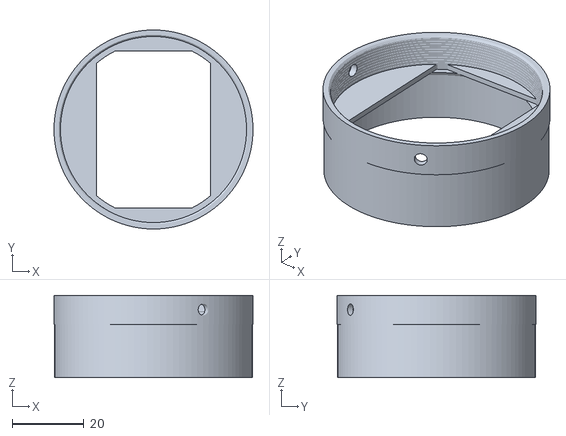
[picture p125: CAD file, 2026-09-20]
stls/hybrid_shift_fx/arm_r_inner.stl
55.6 x 55.6 x 23.0
