airdamien/FXPAN/stls/fxpan/base.stl

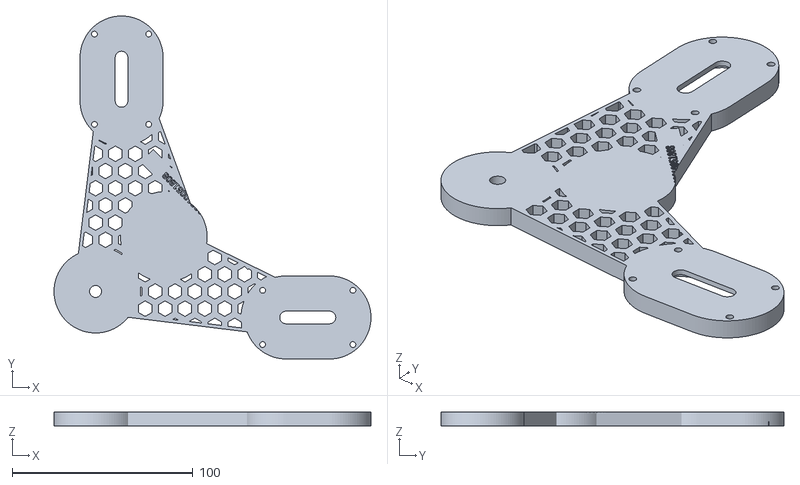
[picture p126: CAD file, 2026-10-06]
stls/fxpan/base.stl
175.5 x 189.9 x 8.00
