airdamien/FXPAN/stls/hybrid_shift/arm_t_inner.stl

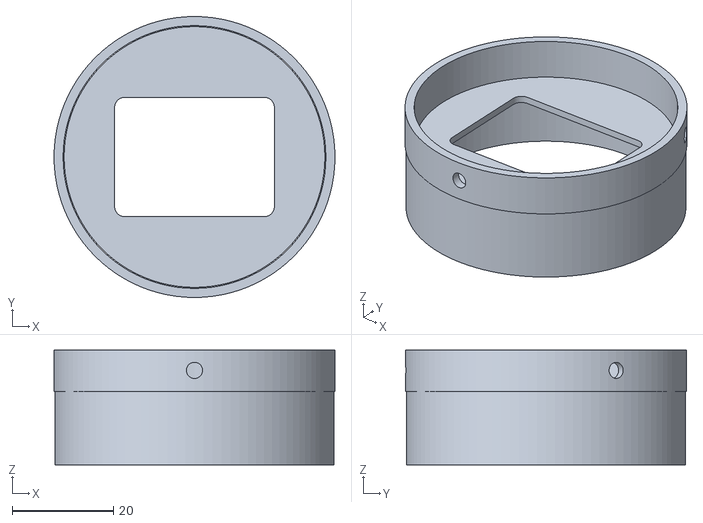
[picture p127: CAD file, 2026-09-16]
stls/hybrid_shift/arm_t_inner.stl
55.6 x 55.6 x 22.7
