airdamien/FXPAN/stls/hybrid_shift_fx/arm_r.stl

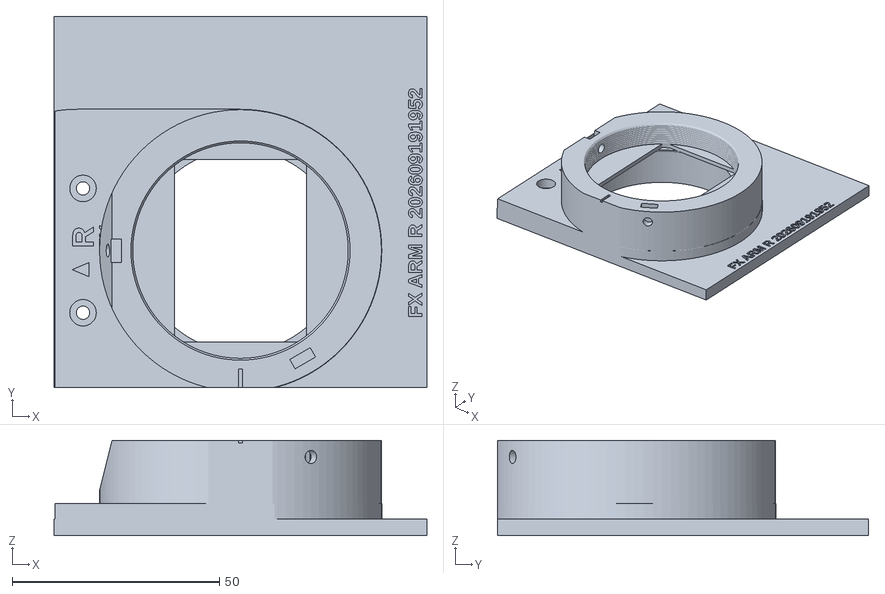
[picture p128: CAD file, 2026-09-20]
stls/hybrid_shift_fx/arm_r.stl
90.0 x 89.6 x 23.0
