airdamien/FXPAN/stls/fxpan/cradle_t.stl

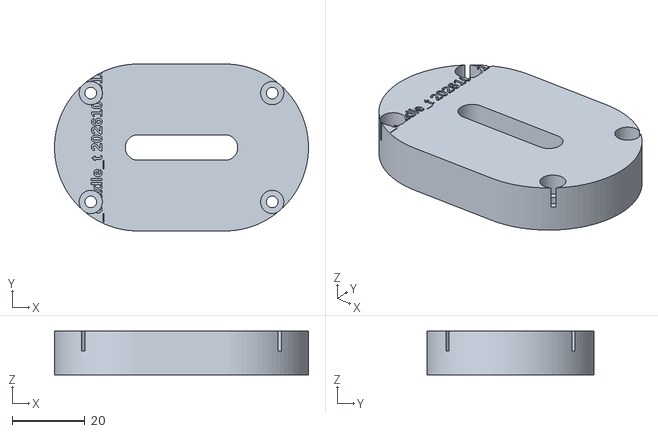
[picture p129: CAD file, 2026-10-06]
stls/fxpan/cradle_t.stl
70.0 x 46.0 x 12.0
