airdamien/FXPAN/stls/hybrid_shift_fx/chassis_logo_mp.stl

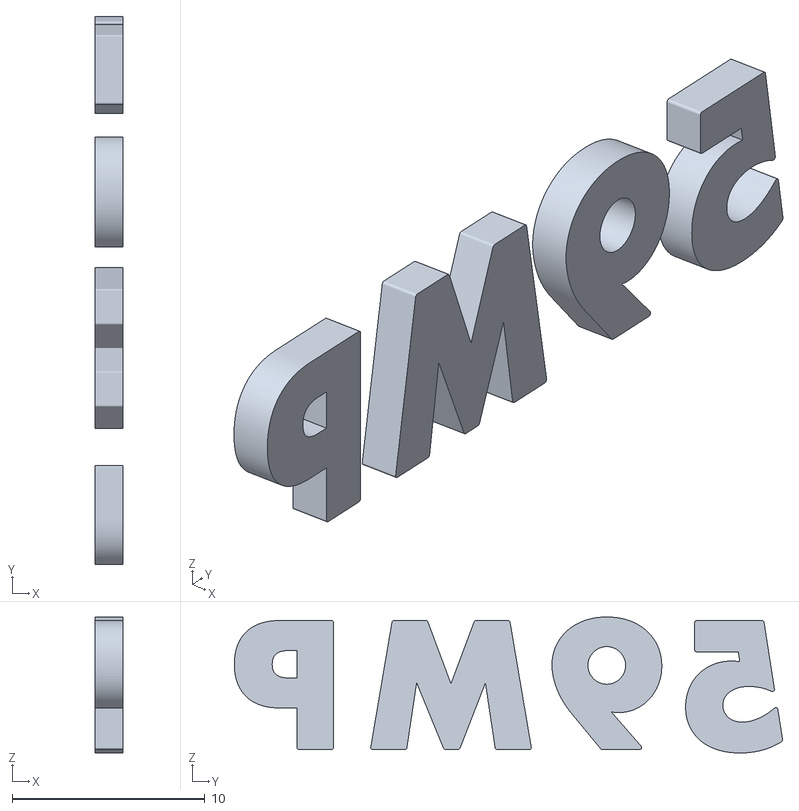
[picture p130: CAD file, 2026-09-18]
stls/hybrid_shift_fx/chassis_logo_mp.stl
1.44 x 28.5 x 7.06
