airdamien/FXPAN/stls/fxpan/stem_nw_direct.stl

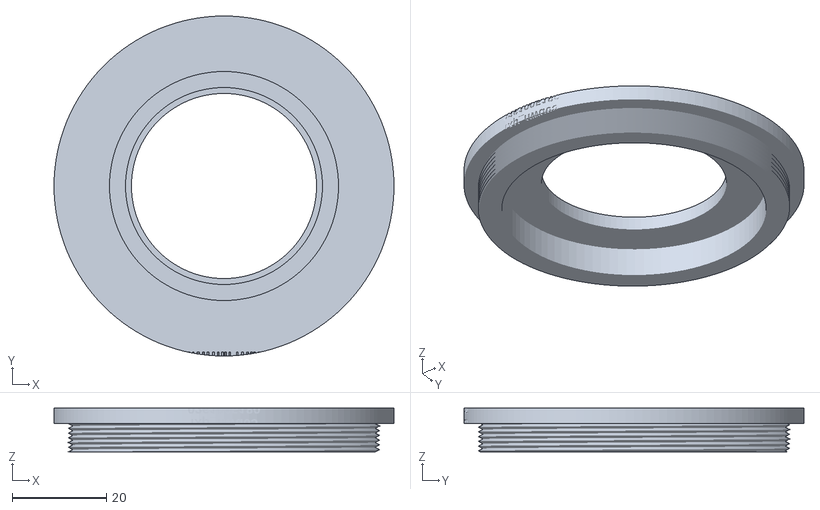
[picture p131: CAD file, 2026-10-06]
stls/fxpan/stem_nw_direct.stl
72.0 x 72.0 x 9.30
