airdamien/FXPAN/stls/hybrid_shift/lid_outer.stl

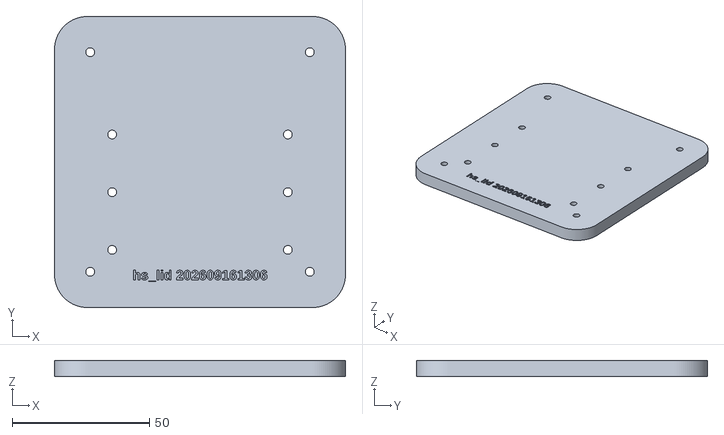
[picture p132: CAD file, 2026-09-16]
stls/hybrid_shift/lid_outer.stl
106.0 x 106.0 x 6.00
