airdamien/FXPAN/stls/hybrid_shift_fx/chassis_logo_rule.stl

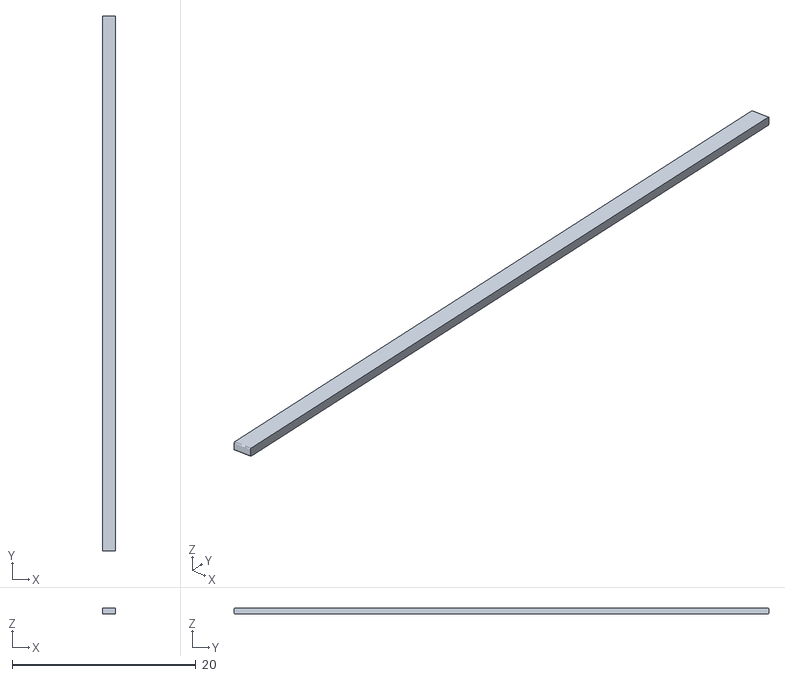
[picture p133: CAD file, 2026-09-18]
stls/hybrid_shift_fx/chassis_logo_rule.stl
1.44 x 58.2 x 0.65
