airdamien/FXPAN/stls/hybrid_shift/arm_t.stl

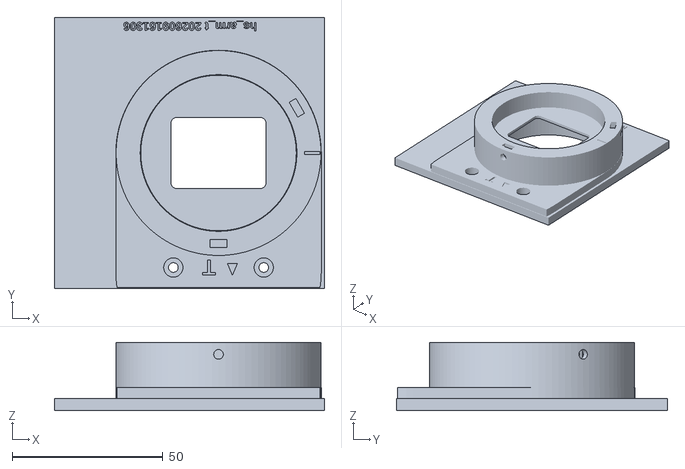
[picture p134: CAD file, 2026-09-16]
stls/hybrid_shift/arm_t.stl
89.6 x 90.0 x 22.7
