airdamien/FXPAN/stls/hybrid_shift_fx/chassis_logo_word.stl

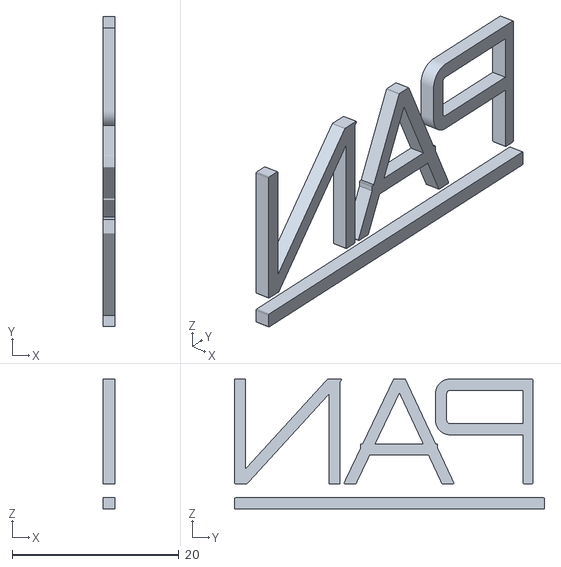
[picture p135: CAD file, 2026-09-18]
stls/hybrid_shift_fx/chassis_logo_word.stl
1.44 x 37.2 x 15.6
