airdamien/FXPAN/stls/hybrid_shift_fx/chassis_logo.stl

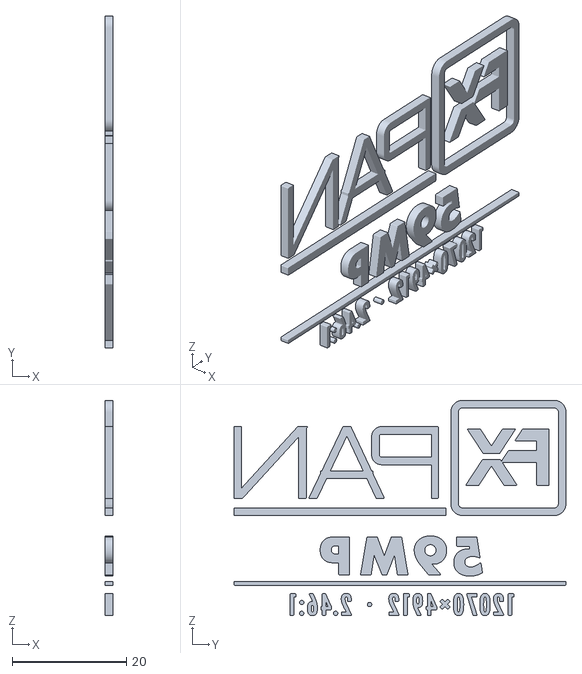
[picture p136: CAD file, 2026-09-18]
stls/hybrid_shift_fx/chassis_logo.stl
1.44 x 58.2 x 37.8
