airdamien/FXPAN/stls/fxpan/arm_t_wl_inner.stl

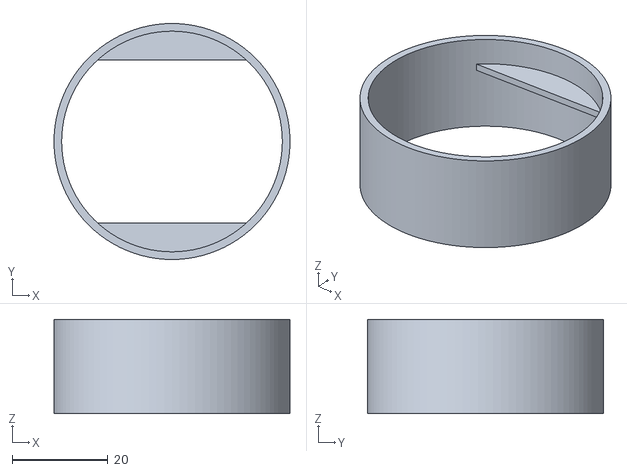
[picture p137: CAD file, 2026-10-06]
stls/fxpan/arm_t_wl_inner.stl
49.2 x 49.2 x 19.6
