airdamien/FXPAN/stls/hybrid_shift_fx/chassis_logo_fx.stl

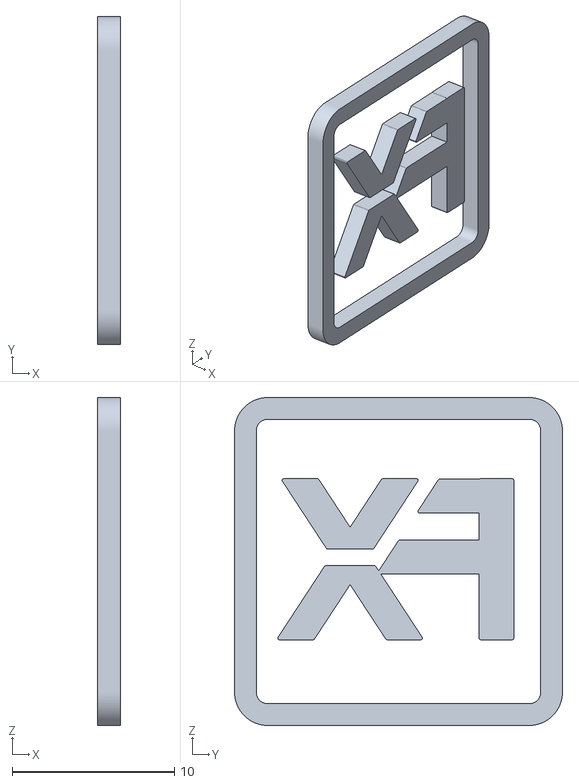
[picture p138: CAD file, 2026-09-18]
stls/hybrid_shift_fx/chassis_logo_fx.stl
1.44 x 20.2 x 20.2
