airdamien/FXPAN/stls/fxpan/stem_w_inner.stl

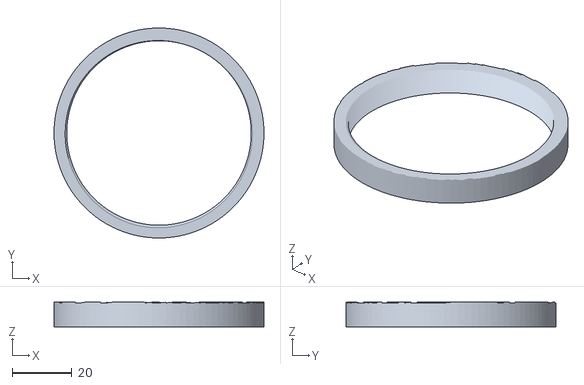
[picture p139: CAD file, 2026-10-02]
stls/fxpan/stem_w_inner.stl
70.0 x 70.0 x 8.20
