airdamien/FXPAN/stls/hybrid_shift/stem.stl

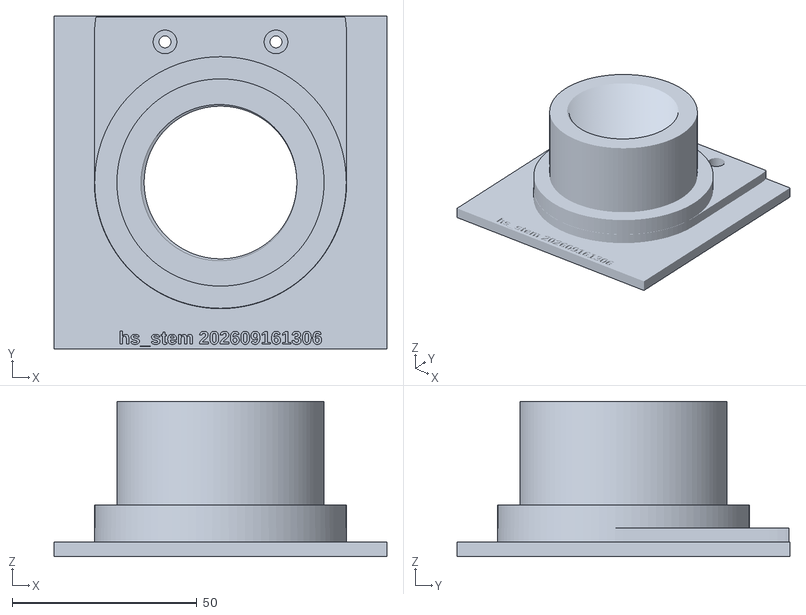
[picture p140: CAD file, 2026-09-16]
stls/hybrid_shift/stem.stl
90.0 x 90.0 x 42.0
