airdamien/FXPAN/stls/fxpan/temp_f_ring.stl

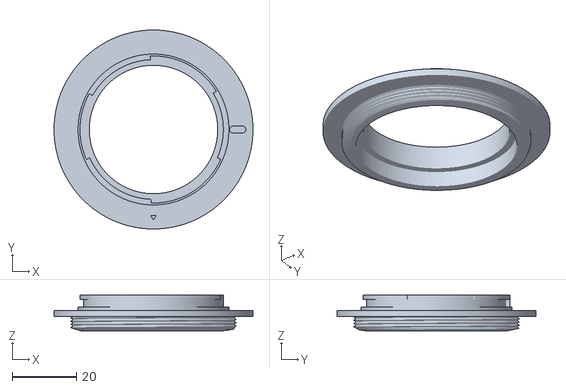
[picture p141: CAD file, 2026-10-02]
stls/fxpan/temp_f_ring.stl
62.0 x 62.0 x 11.2
