airdamien/FXPAN/stls/hybrid_shift/chassis_inner.stl

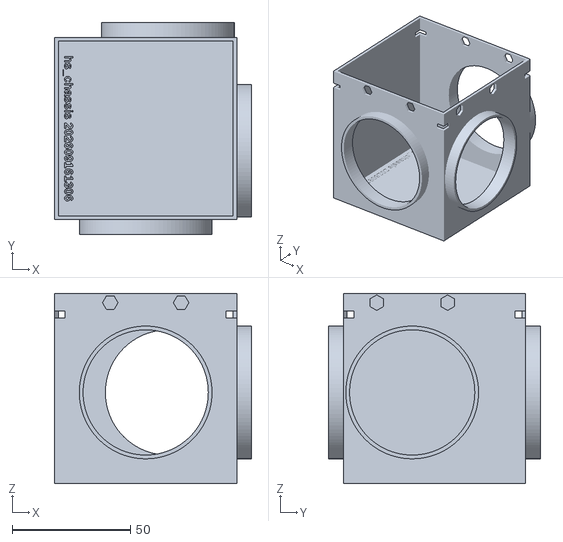
[picture p142: CAD file, 2026-09-16]
stls/hybrid_shift/chassis_inner.stl
83.4 x 89.6 x 80.5
