airdamien/FXPAN/stls/hybrid_shift_fx/chassis_logo_spec.stl

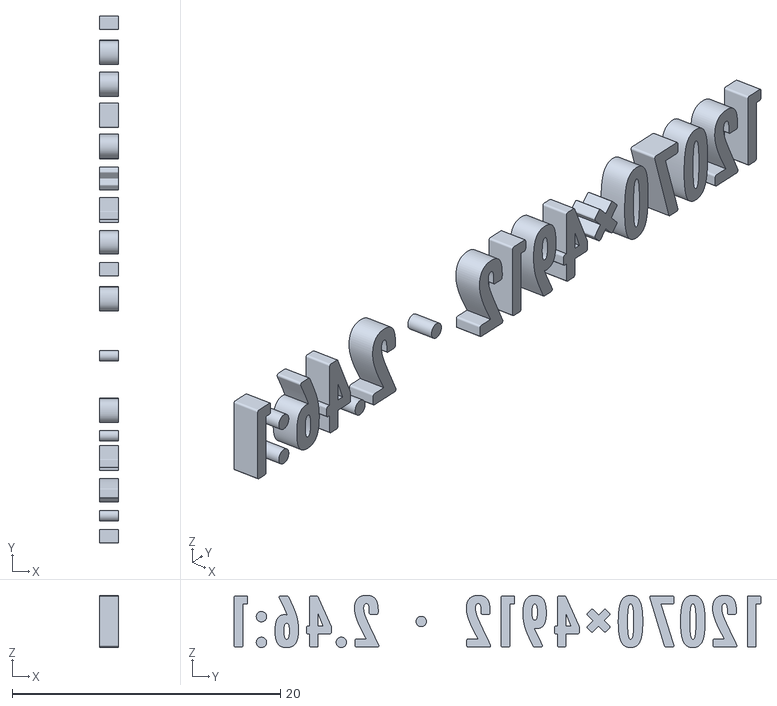
[picture p143: CAD file, 2026-09-18]
stls/hybrid_shift_fx/chassis_logo_spec.stl
1.44 x 39.3 x 3.90
