airdamien/FXPAN/stls/fxpan/stem_w_outer.stl

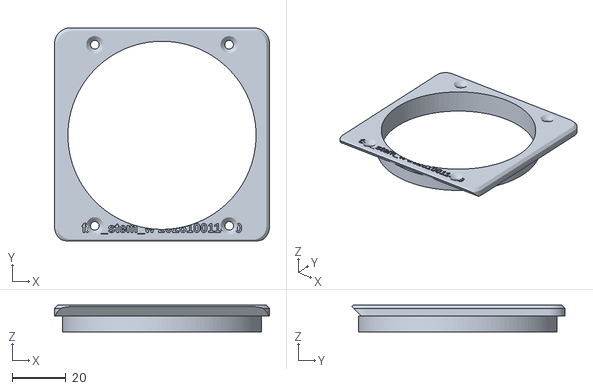
[picture p144: CAD file, 2026-10-02]
stls/fxpan/stem_w_outer.stl
80.0 x 79.4 x 10.0
