airdamien/FXPAN/stls/hybrid_shift/stem_el180_outer.stl

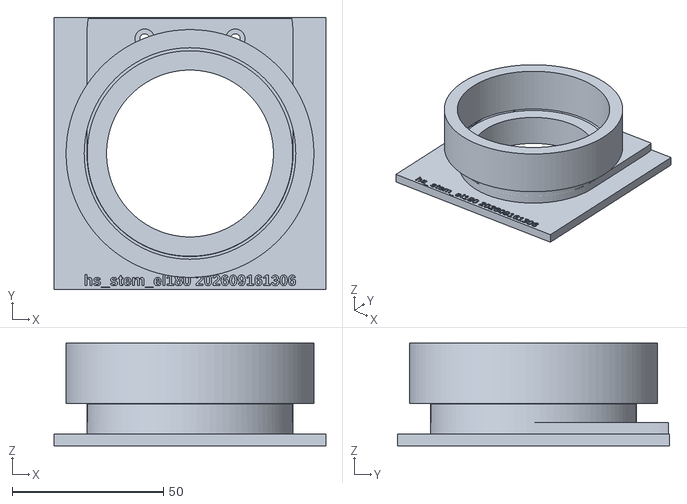
[picture p145: CAD file, 2026-09-16]
stls/hybrid_shift/stem_el180_outer.stl
90.0 x 90.0 x 34.0
