airdamien/FXPAN/stls/hybrid_shift_fx/arm_t_f_outer.stl

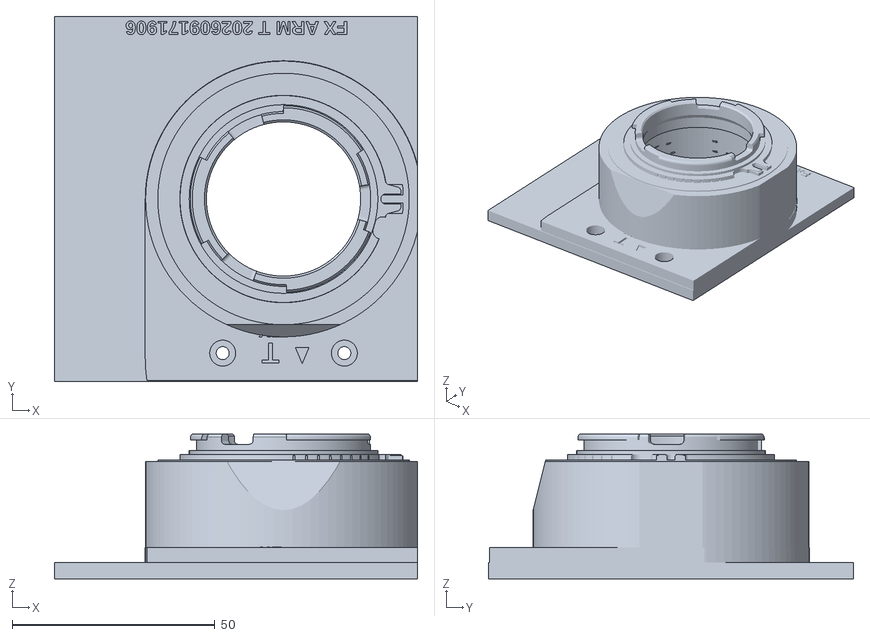
[picture p146: CAD file, 2026-09-18]
stls/hybrid_shift_fx/arm_t_f_outer.stl
89.6 x 90.0 x 35.7
