airdamien/FXPAN/stls/fxpan/stem_m65.stl

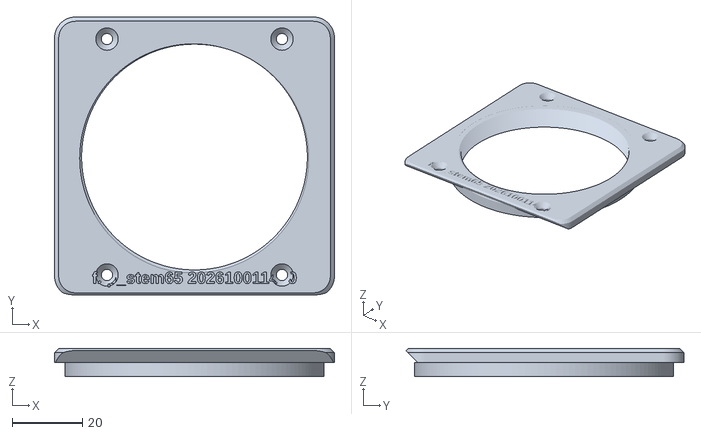
[picture p147: CAD file, 2026-10-02]
stls/fxpan/stem_m65.stl
80.0 x 79.4 x 8.00
