airdamien/FXPAN/stls/hybrid_shift/hybrid_tray.stl

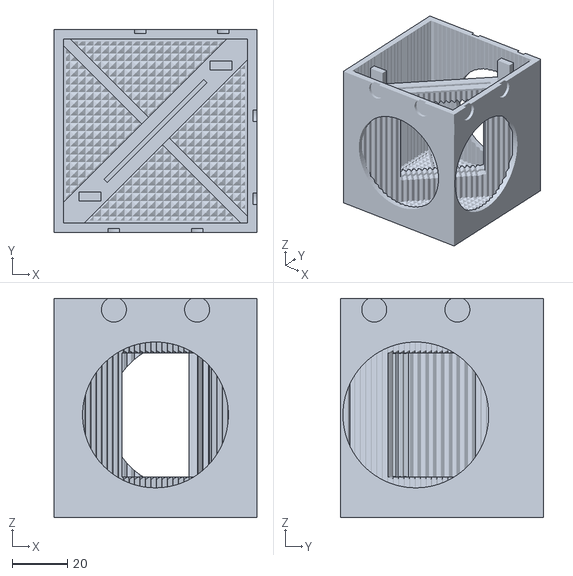
[picture p148: CAD file, 2026-09-16]
stls/hybrid_shift/hybrid_tray.stl
73.2 x 73.2 x 79.0
