airdamien/FXPAN/stls/hybrid_shift_fx/lid_inner.stl

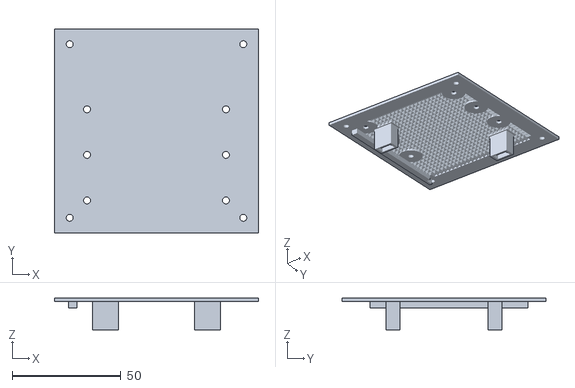
[picture p149: CAD file, 2026-09-18]
stls/hybrid_shift_fx/lid_inner.stl
94.0 x 94.0 x 14.6
