airdamien/FXPAN/stls/hybrid_shift/stem_el180_inner.stl

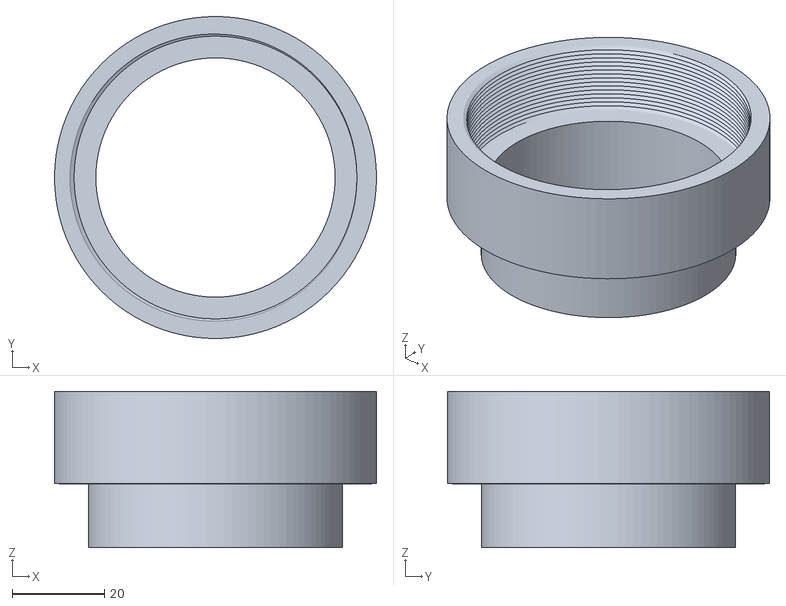
[picture p151: CAD file, 2026-09-16]
stls/hybrid_shift/stem_el180_inner.stl
70.0 x 70.0 x 34.0
