airdamien/FXPAN/stls/fxpan/arm_t_hw_outer.stl

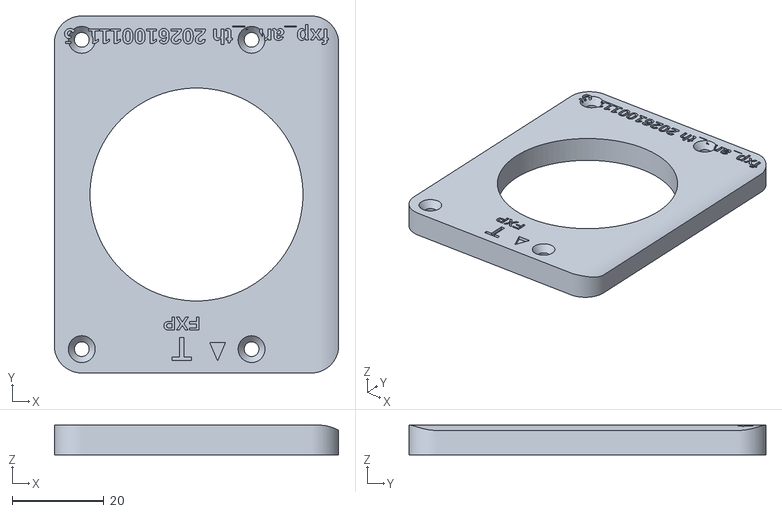
[picture p152: CAD file, 2026-10-01]
stls/fxpan/arm_t_hw_outer.stl
62.0 x 77.8 x 6.50
