airdamien/FXPAN/stls/fxpan/arm_t_hw.stl

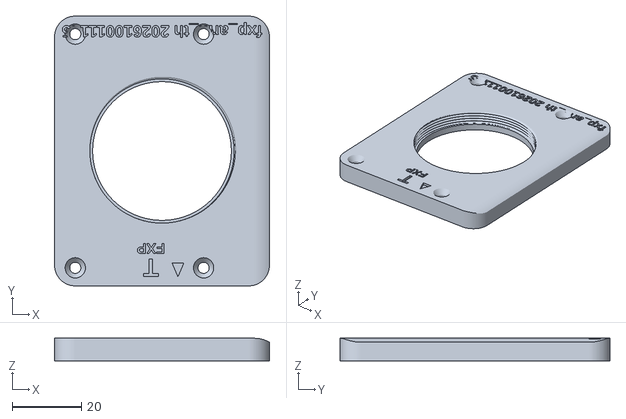
[picture p153: CAD file, 2026-10-01]
stls/fxpan/arm_t_hw.stl
62.0 x 77.8 x 6.50
