airdamien/FXPAN/stls/hybrid_shift_fx/brace.stl

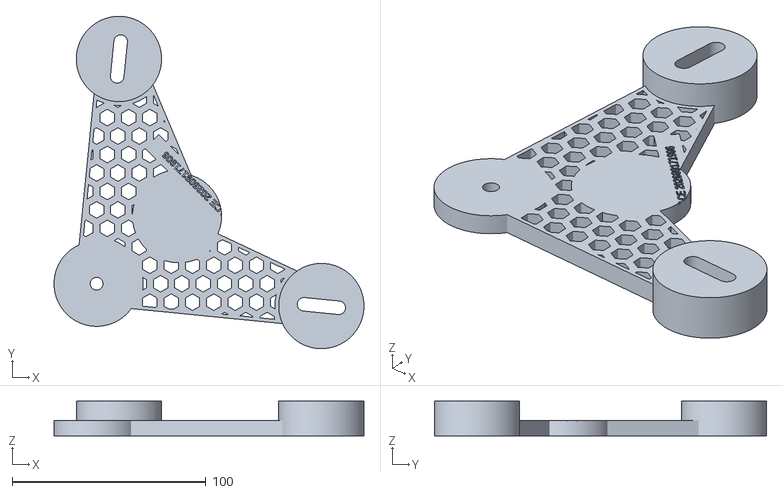
[picture p154: CAD file, 2026-09-18]
stls/hybrid_shift_fx/brace.stl
160.0 x 171.5 x 18.0
