airdamien/FXPAN/stls/hybrid_shift/stem_el180.stl

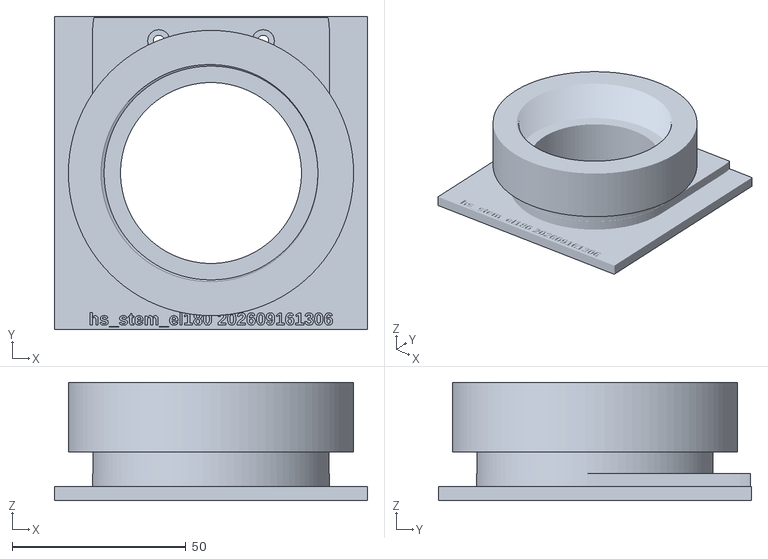
[picture p155: CAD file, 2026-09-16]
stls/hybrid_shift/stem_el180.stl
90.0 x 90.0 x 34.0
