airdamien/FXPAN/stls/hybrid_shift_fx/lid.stl

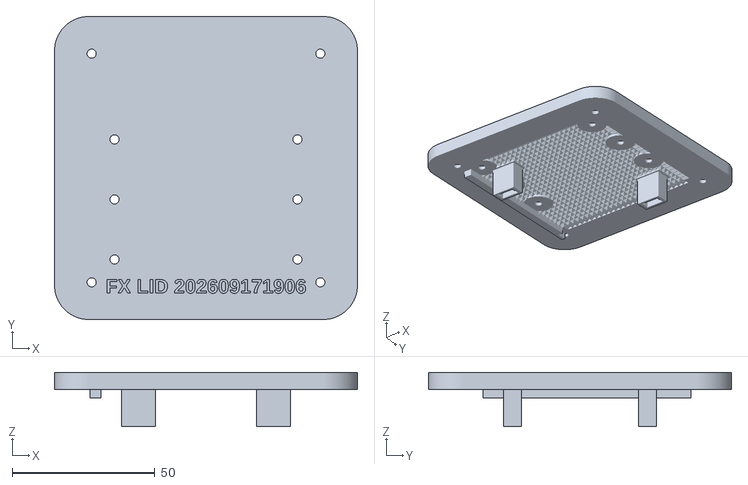
[picture p156: CAD file, 2026-09-18]
stls/hybrid_shift_fx/lid.stl
106.0 x 106.0 x 19.0
