airdamien/FXPAN/stls/fxpan/arm_t_hw_inner.stl

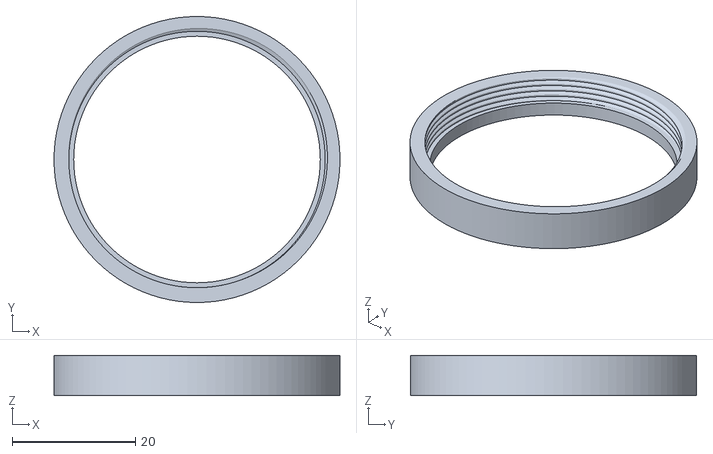
[picture p157: CAD file, 2026-10-01]
stls/fxpan/arm_t_hw_inner.stl
46.4 x 46.4 x 6.50
