airdamien/FXPAN/stls/hybrid_shift/elnikkor_adapter.stl

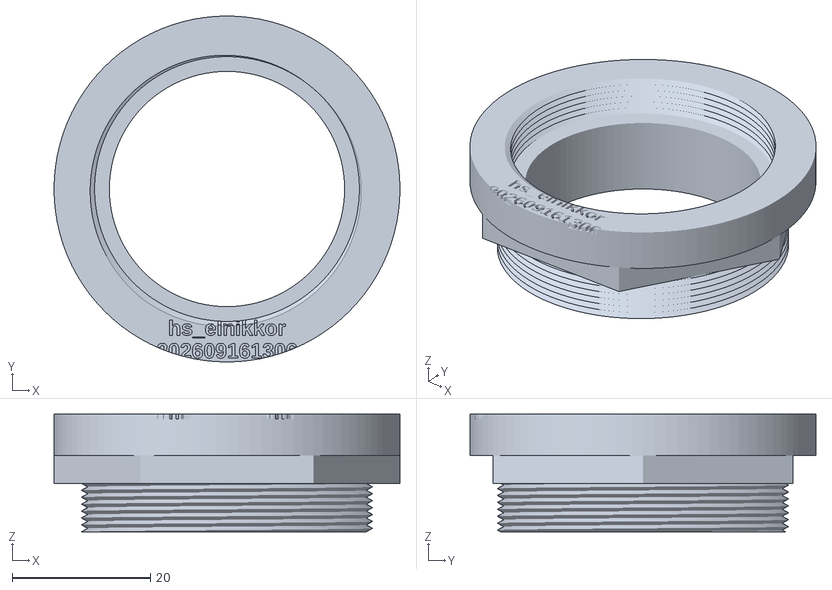
[picture p158: CAD file, 2026-09-16]
stls/hybrid_shift/elnikkor_adapter.stl
50.0 x 50.0 x 17.0
