airdamien/FXPAN/stls/fxpan/fxp_tray.stl

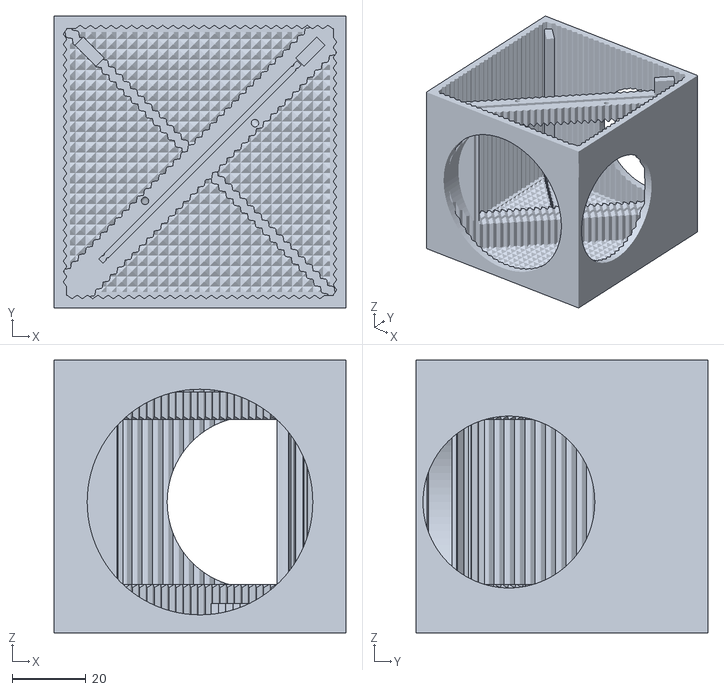
[picture p159: CAD file, 2026-10-01]
stls/fxpan/fxp_tray.stl
79.2 x 79.2 x 74.0
