airdamien/FXPAN/stls/hybrid_shift/arm_r_inner.stl

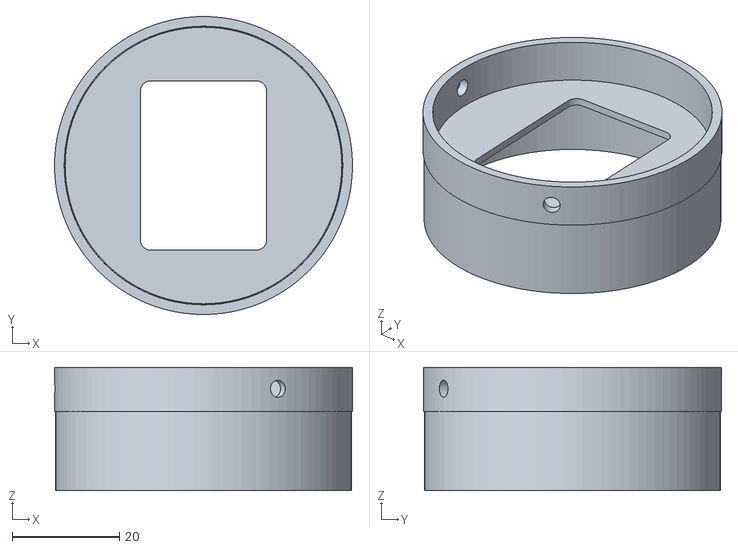
[picture p160: CAD file, 2026-09-16]
stls/hybrid_shift/arm_r_inner.stl
55.6 x 55.6 x 23.0
