airdamien/FXPAN/stls/fxpan/arm_r_focus.stl

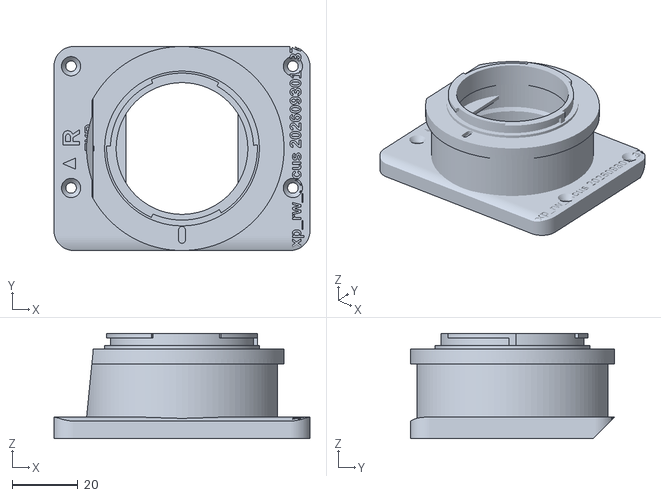
[picture p161: CAD file, 2026-09-30]
stls/fxpan/arm_r_focus.stl
77.8 x 62.0 x 32.0
