airdamien/FXPAN/stls/hybrid_shift/stem_outer.stl

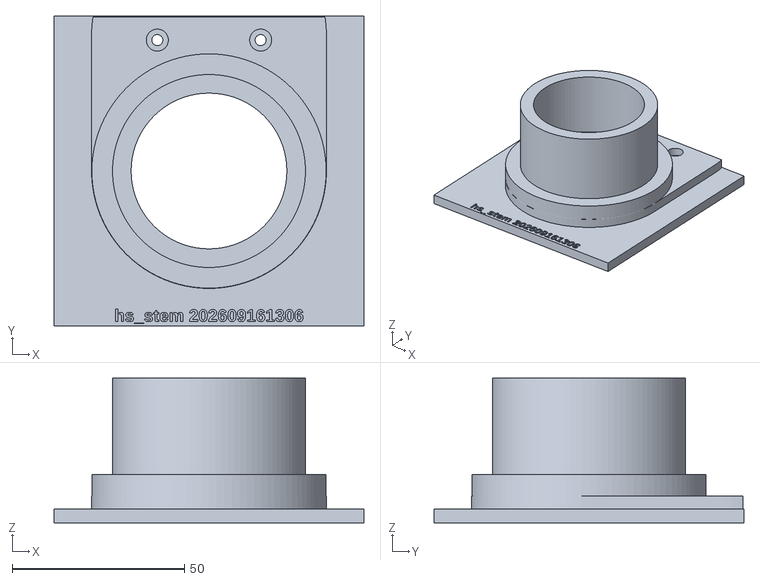
[picture p162: CAD file, 2026-09-16]
stls/hybrid_shift/stem_outer.stl
90.0 x 90.0 x 42.0
