airdamien/FXPAN/stls/hybrid_shift_fx/arm_r_f_inner.stl

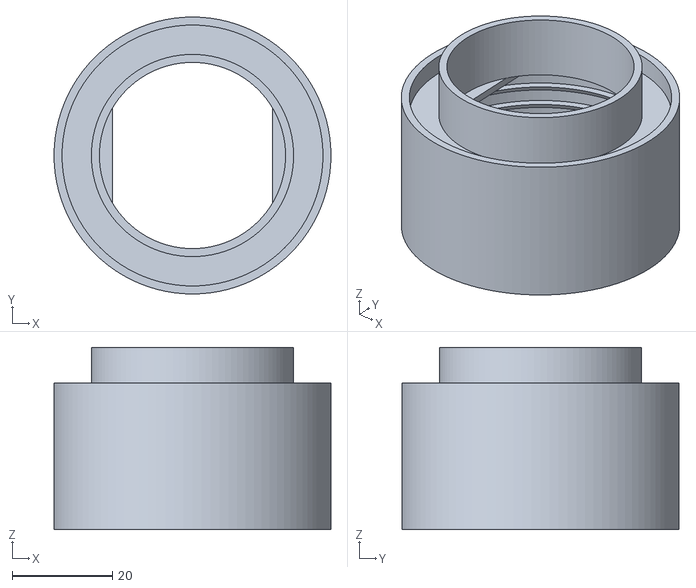
[picture p163: CAD file, 2026-09-18]
stls/hybrid_shift_fx/arm_r_f_inner.stl
55.2 x 55.2 x 36.3
