airdamien/FXPAN/stls/fxpan/stem_nw180.stl

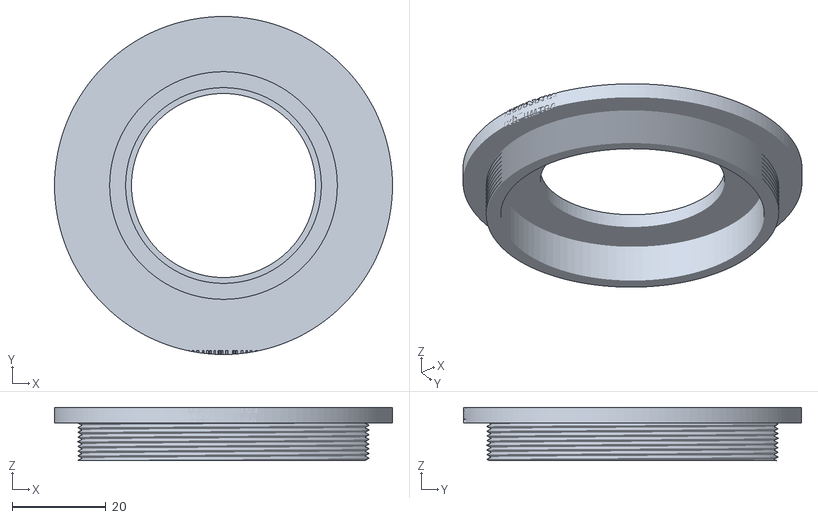
[picture p164: CAD file, 2026-09-29]
stls/fxpan/stem_nw180.stl
72.0 x 72.0 x 11.3
