airdamien/FXPAN/stls/hybrid_shift/display_mount.stl

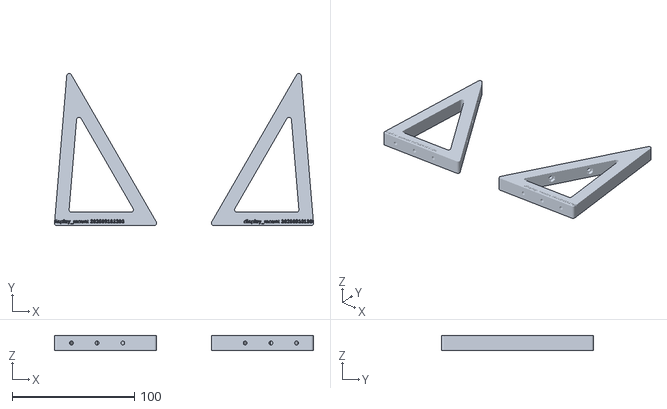
[picture p165: CAD file, 2026-09-16]
stls/hybrid_shift/display_mount.stl
211.6 x 124.4 x 12.0
