airdamien/FXPAN/stls/fxpan/m65_ring.stl

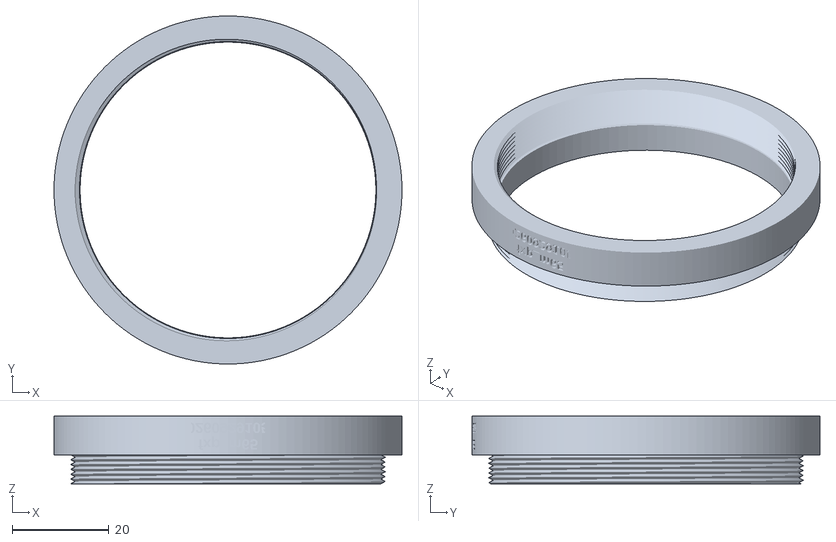
[picture p166: CAD file, 2026-09-29]
stls/fxpan/m65_ring.stl
72.0 x 72.0 x 14.0
