airdamien/FXPAN/stls/fxpan/chassis_logo_fx.stl

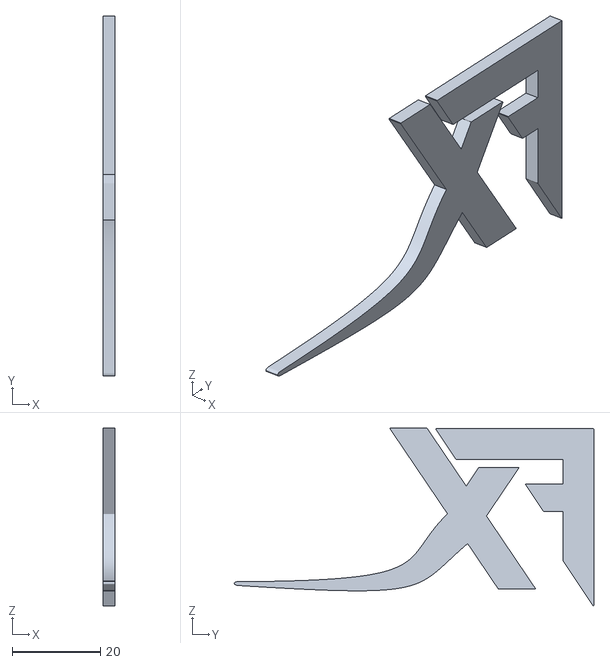
[picture p167: CAD file, 2026-09-26]
stls/fxpan/chassis_logo_fx.stl
2.64 x 81.5 x 40.4
