airdamien/FXPAN/stls/hybrid_shift/stem_inner.stl

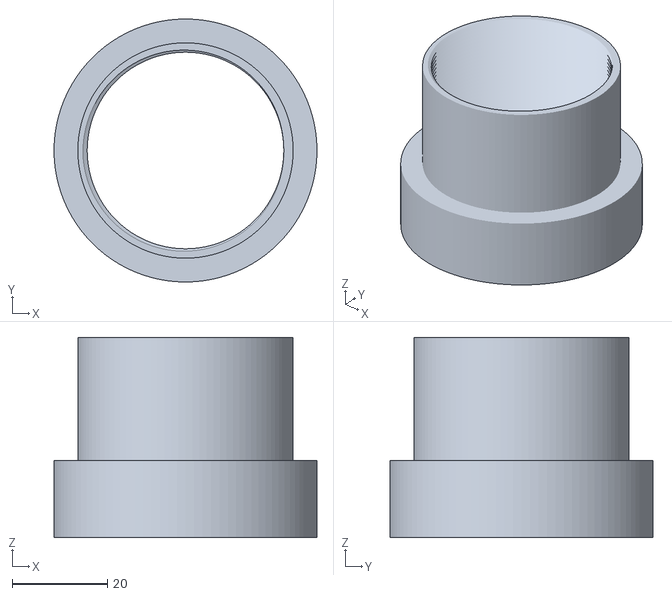
[picture p168: CAD file, 2026-09-15]
stls/hybrid_shift/stem_inner.stl
55.2 x 55.2 x 42.0
