airdamien/FXPAN/stls/fxpan/chassis_logo_ana_mp.stl

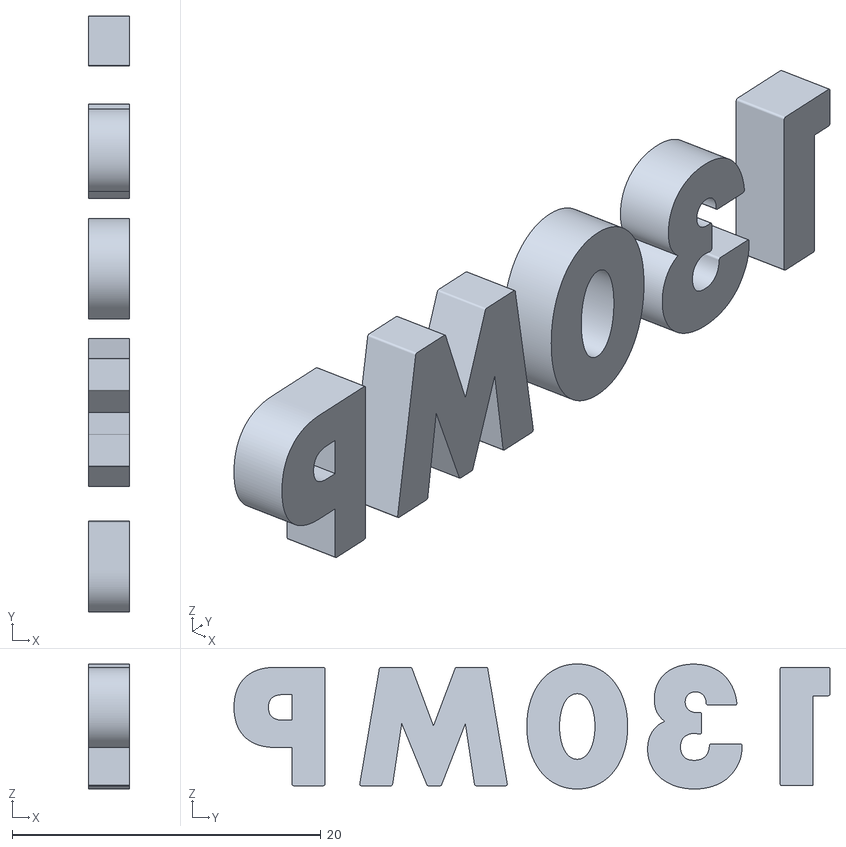
[picture p169: CAD file, 2026-09-26]
stls/fxpan/chassis_logo_ana_mp.stl
2.64 x 38.6 x 8.09
