airdamien/FXPAN/stls/hybrid_shift/arm_t_sf_outer.stl

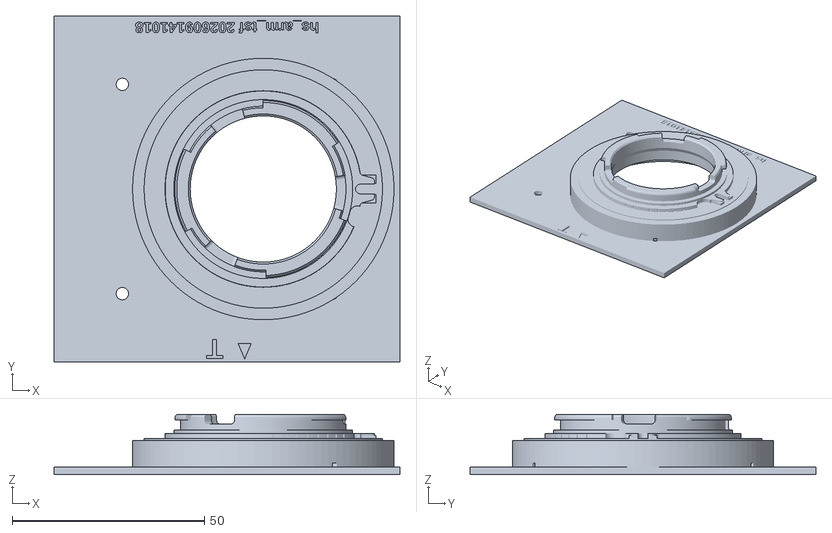
[picture p170: CAD file, 2026-09-14]
stls/hybrid_shift/arm_t_sf_outer.stl
90.0 x 90.0 x 15.7
