airdamien/FXPAN/stls/fxpan/chassis_logo_outline.stl

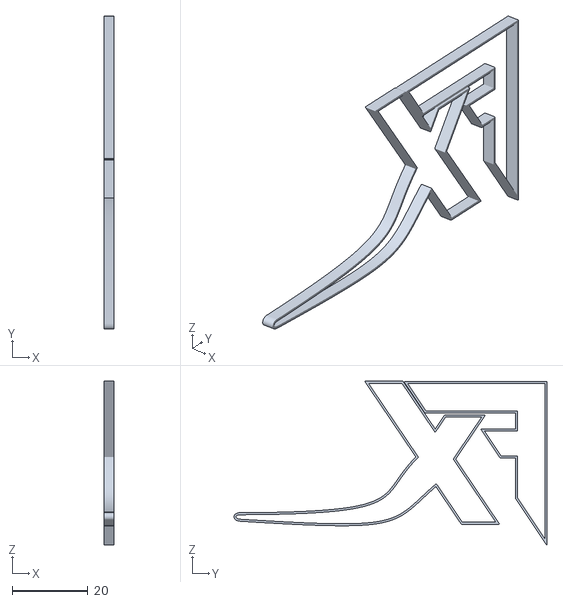
[picture p171: CAD file, 2026-09-26]
stls/fxpan/chassis_logo_outline.stl
2.64 x 82.9 x 43.3
