airdamien/FXPAN/stls/fxpan/chassis_logo_stripe.stl

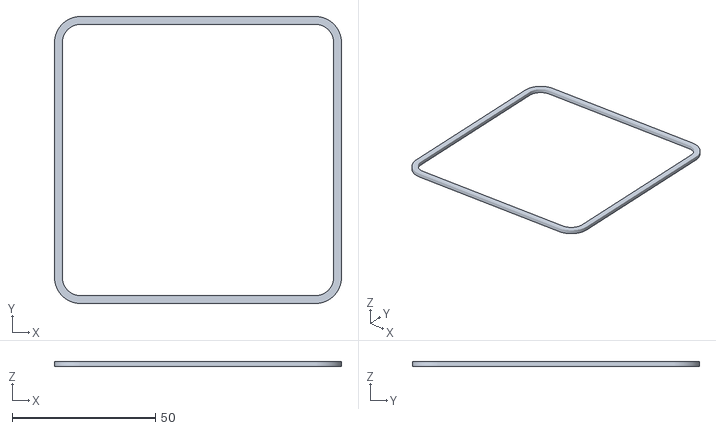
[picture p172: CAD file, 2026-09-26]
stls/fxpan/chassis_logo_stripe.stl
100.3 x 100.3 x 1.76
