airdamien/FXPAN/stls/fxpan/chassis_logo_ana_rule.stl

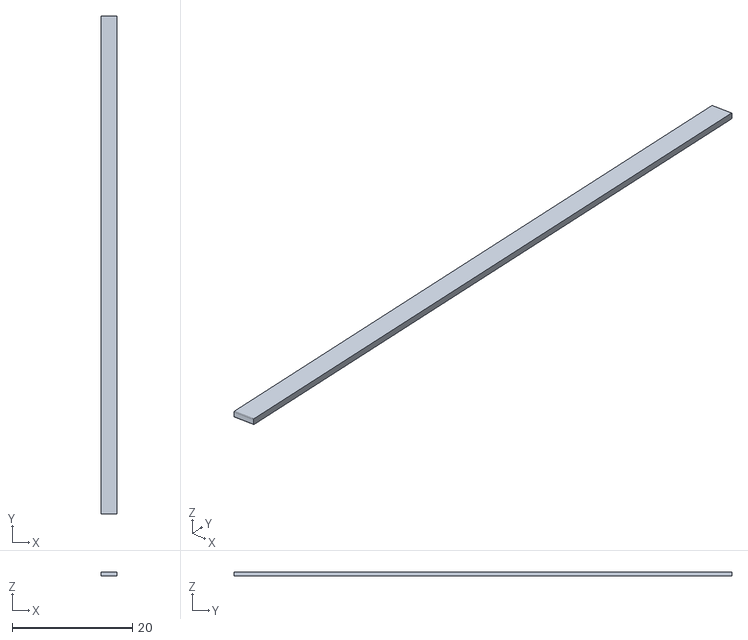
[picture p174: CAD file, 2026-09-26]
stls/fxpan/chassis_logo_ana_rule.stl
2.64 x 82.9 x 0.717
