airdamien/FXPAN/stls/hybrid_shift/arm_t_sf_inner.stl

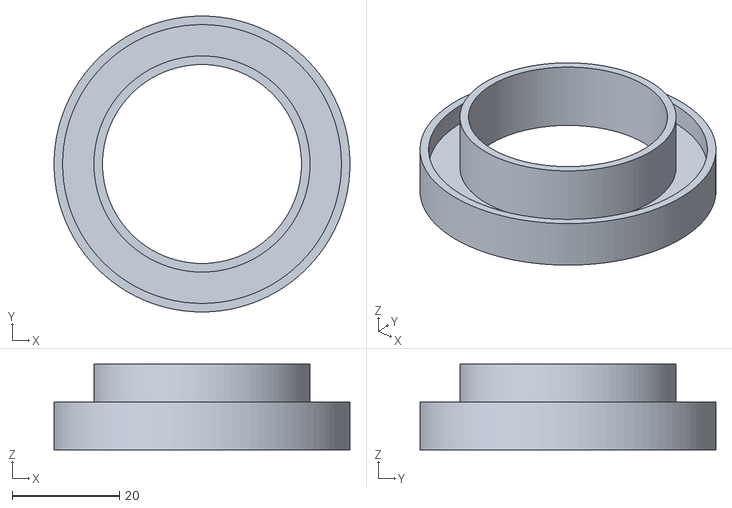
[picture p175: CAD file, 2026-09-14]
stls/hybrid_shift/arm_t_sf_inner.stl
55.2 x 55.2 x 16.0
