airdamien/FXPAN/stls/fxpan/chassis_logo_spec.stl

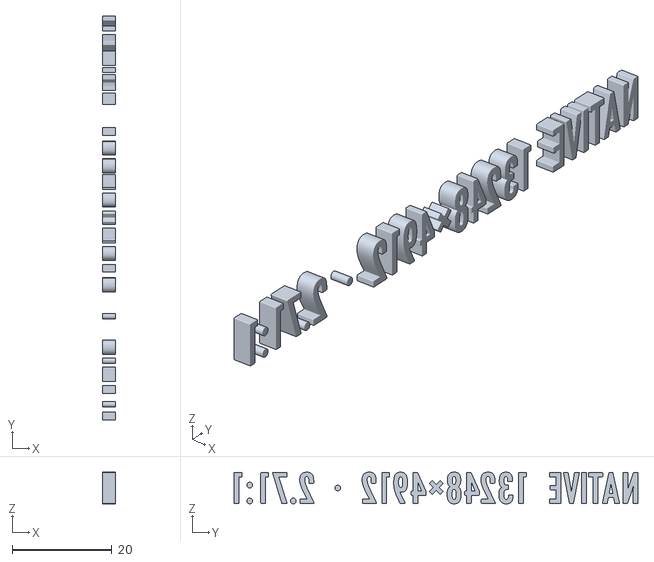
[picture p176: CAD file, 2026-09-26]
stls/fxpan/chassis_logo_spec.stl
2.64 x 81.0 x 6.37
