airdamien/FXPAN/stls/hybrid_shift/arm_r_sf_inner.stl

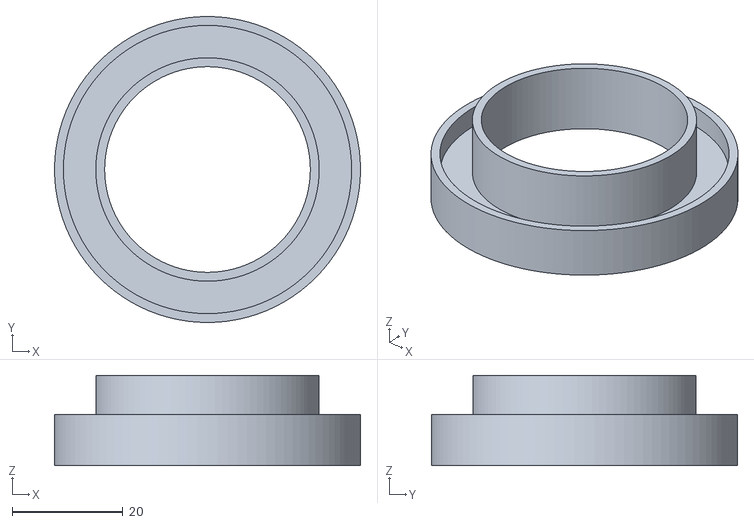
[picture p177: CAD file, 2026-09-14]
stls/hybrid_shift/arm_r_sf_inner.stl
55.2 x 55.2 x 16.3
