airdamien/FXPAN/stls/fxpan/chassis_logo_ana.stl

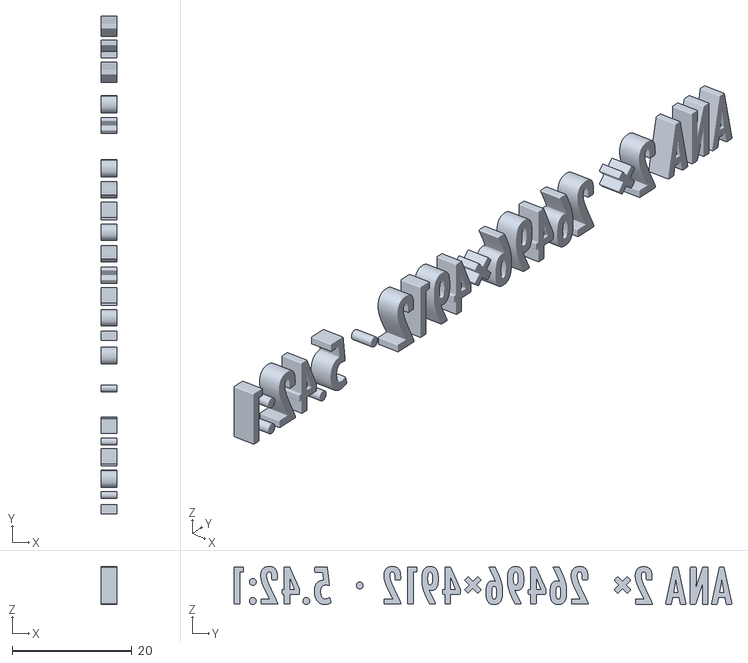
[picture p178: CAD file, 2026-09-26]
stls/fxpan/chassis_logo_ana.stl
2.64 x 83.2 x 6.37
