airdamien/FXPAN/stls/hybrid_shift/shims.stl

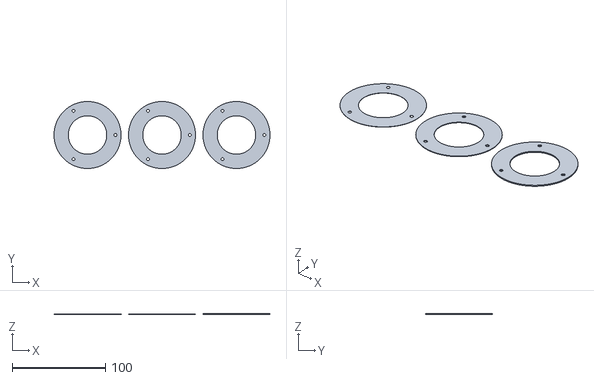
[picture p179: CAD file, 2026-09-12]
stls/hybrid_shift/shims.stl
232.0 x 72.0 x 1.00
