airdamien/FXPAN/stls/fxpan/chassis_logo_mp.stl

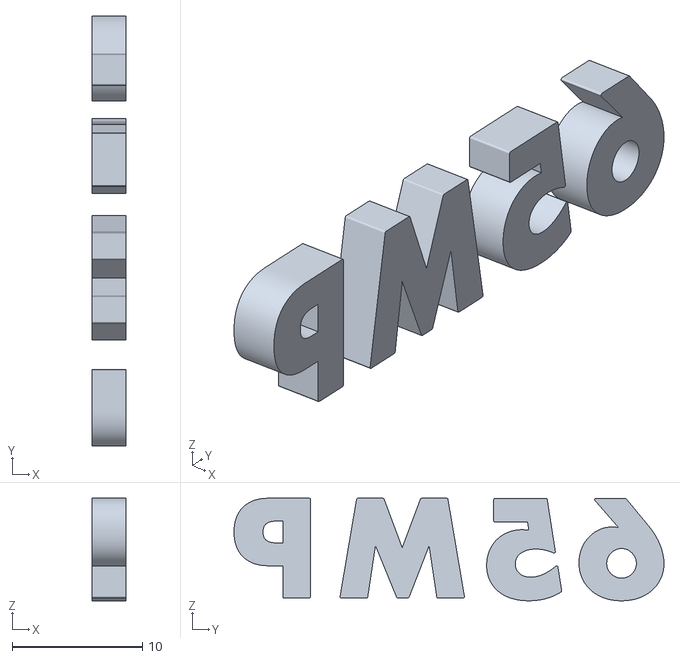
[picture p180: CAD file, 2026-09-26]
stls/fxpan/chassis_logo_mp.stl
2.64 x 33.0 x 7.88
