airdamien/FXPAN/stls/fxpan/logo_cookie.stl

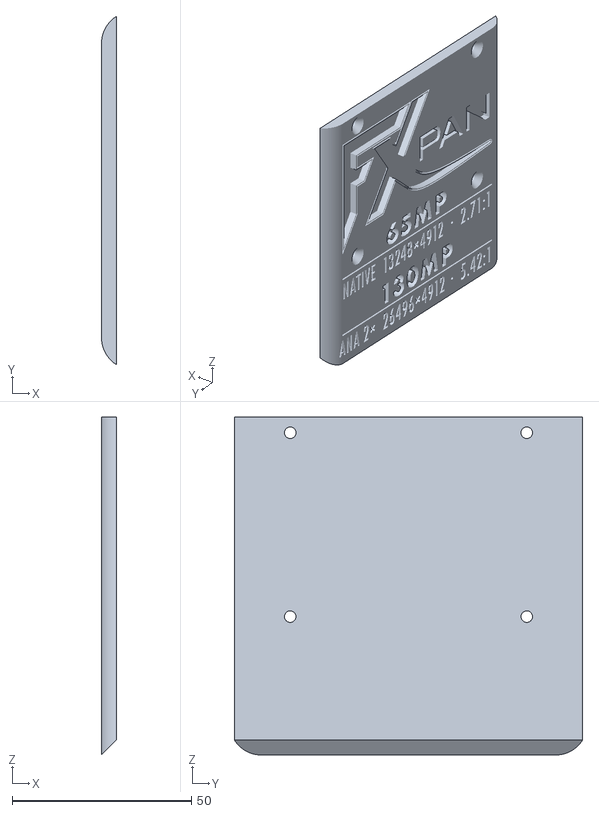
[picture p181: CAD file, 2026-09-26]
stls/fxpan/logo_cookie.stl
4.20 x 97.2 x 94.3
