airdamien/FXPAN/stls/fxpan/chassis_logo_word.stl

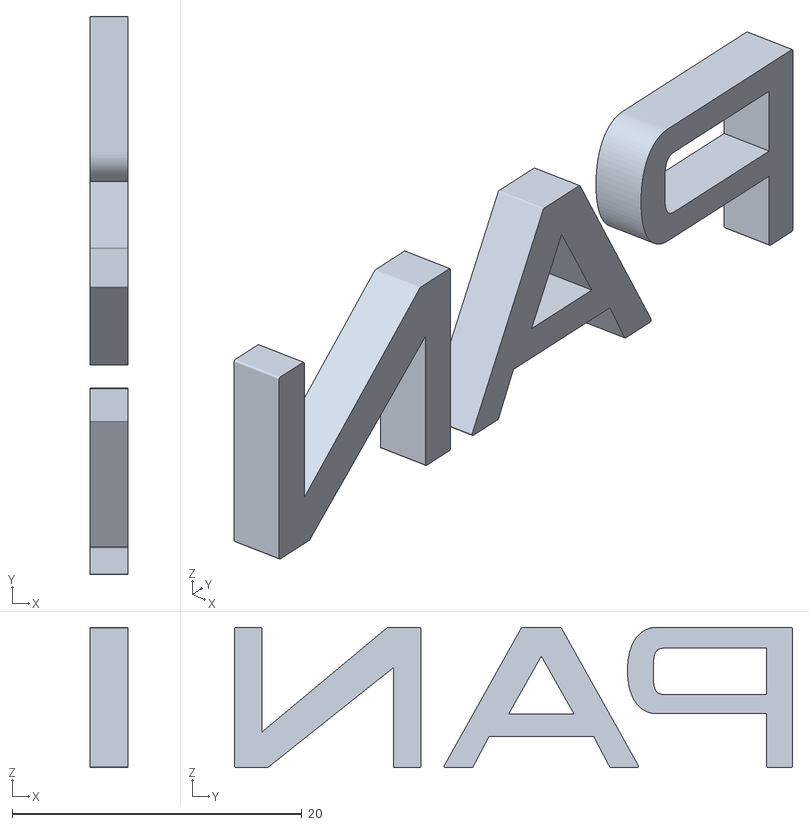
[picture p182: CAD file, 2026-09-26]
stls/fxpan/chassis_logo_word.stl
2.64 x 38.5 x 9.70
