airdamien/FXPAN/stls/fxpan/arm_t_w.stl

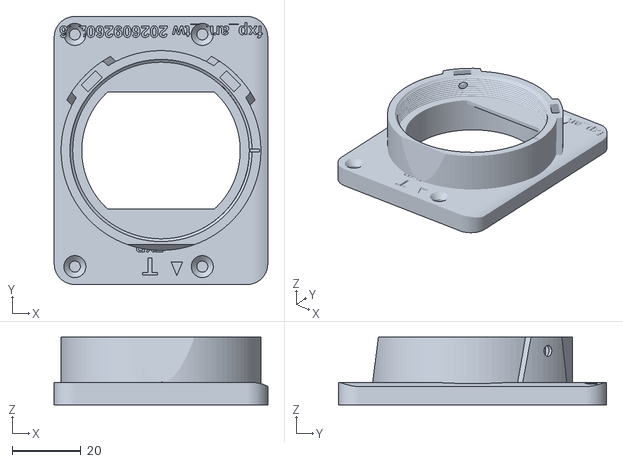
[picture p183: CAD file, 2026-09-26]
stls/fxpan/arm_t_w.stl
62.0 x 77.8 x 19.7
