airdamien/FXPAN/stls/fxpan/arm_t_fw_outer.stl

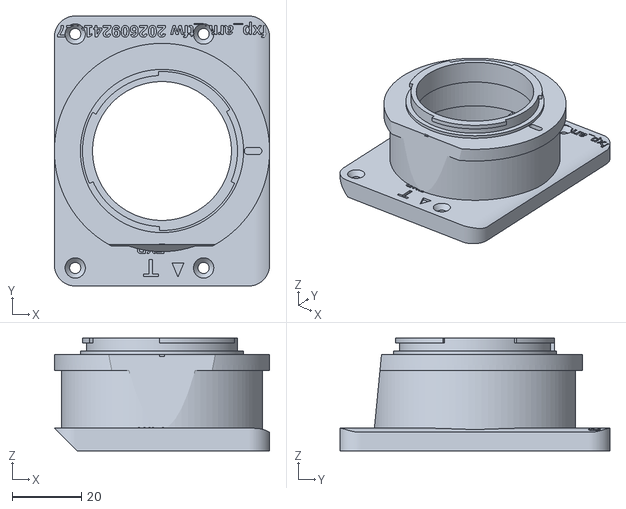
[picture p184: CAD file, 2026-09-24]
stls/fxpan/arm_t_fw_outer.stl
62.0 x 77.8 x 32.4
