airdamien/FXPAN/openscad/t_chassis.scad

// Alias — prefer opening WATCH_ME.scad for live reload while editing.
include <WATCH_ME.scad>
