airdamien/FXPAN/openscad/fxpan/WATCH_ME.scad

// =============================================================================
// fxpan/WATCH_ME.scad — FXPAN 65: clean-sheet FX panoramic body
// =============================================================================
// Two D800 behind one EL-Nikkor 180/5.6N and a 75×75×1 50/50 plate.
// 64.80 × 23.9 mm stitch, 2.711:1 (XPan is 2.708:1), 13248 × 4912 = 65.1 MP.
// The chamber is deliberately NOT a cube. BOX_Z carries BS_H. The flange
// register is 158.5 mm, not the 180 mm focal length: the lens nut is recessed
// into the wall and the camera cookies sit CAM_RECESS deeper. Read params.scad.
//
// Lens −Y. Plate at the origin, 45°, S1 (the 50/50 coating) toward the lens.
// Reflect leg → +X (camera R), transmit leg → +Y (camera T). Both bores are
// translated by sensor_shift() in opposite senses; no tube toe, no Scheimpflug.
// The lens, camera, and logo faces are blind rebates closed all round, so
// the chassis keeps an unbroken top rim and the lid sits flush on it. The
// red line around the plinth stays in the chassis.
//
// This body does not share parts with hybrid_shift. Every STL is stamped
// fxp_* and the bore is wider (TUBE_ID 46 / F_BORE 44.0 vs 52 / 40.3) so the
// 14.4 mm shift does not clip. Open this file and read the echo() lines.
// =============================================================================

/* [Part] */
PART = "assembly"; // [assembly:Assembly, section:Assembly section, isco:ISCO on the 180, isco_cut:ISCO section, chassis:Chassis, logo_cookie:Logo cookie, stem:Stem EL 180 helicoid, stem_el180_inf:Stem EL 180 infinity, stem_w:Stem Nikkor-W, stem_nw180:Nikkor-W nose, stem_nw_m65:Nikkor-W nose on M65, stem_nw_direct:Nikkor-W nose direct in stem_m65, arm_r:Arm R, arm_t:Arm T, arm_r_f:Arm R printed F, arm_r_focus:Arm R focused F Nikkor-W, arm_r_wl:Arm R Nikkor-W lens helicoid, arm_t_wl:Arm T Nikkor-W lens helicoid, arm_t_f:Arm T printed F, arm_r_w:Arm R Nikkor-W, arm_t_w:Arm T Nikkor-W, arm_r_fw:Arm R printed F Nikkor-W, arm_t_fw:Arm T printed F Nikkor-W, arm_r_h:Arm R helicoid, arm_t_h:Arm T helicoid, arm_r_hw:Arm R helicoid Nikkor-W, arm_t_hw:Arm T helicoid Nikkor-W, fmount_h_r:F mount on helicoid R, fmount_h_t:F mount on helicoid T, cam_helicoid:Camera helicoid, lid:Lid, display_mount:Display mount, fxp_tray:Plate cartridge, base:Base, cradle_r:Cradle R, cradle_t:Cradle T, baffle:Baffles, ringgauge:M52 ring gauge, shims:Shims, el180_adapter:EL 180 adapter, m65_ring:M65 to M62 ring, stem_m65:Stem M65 helicoid]

include <params.scad>
include <../lib/threads.scad>
include <../lib/part_stamp.scad>
include <fxp_f_mount.scad>
use <fxp_tray.scad>
use <shims.scad>
use <../camera_body.scad>
use <../monitor/display_mount.scad>
use <../monitor/monitor.scad>
include <../isco/el_nikkor_180n.scad>
include <../isco/isco_ultrastar_attachment.scad>
include <../isco/isco_mount.scad>
include <../isco/nikkor_w_180.scad>

/* [View] */
SHOW_LID = 1; // [0:hide, 1:show]
SHOW_PANELS = 1; // [0:hide, 1:show]
SHOW_MONITOR = 0; // [0:hide, 1:show]
SHOW_PI = 0; // [0:hide, 1:show]
SHOW_TRIGGER = 1; // [0:hide, 1:show]
SHOW_BODIES = 0; // [0:hide, 1:D800]
SHOW_LENS = 0; // [0:hide, 1:show]
SHOW_LENS_MARKS = 0; // [0:hide, 1:pupils and focal plane]
SHOW_BASE = 1; // [0:hide, 1:show]
SHOW_AXES = 1; // [0:hide, 1:show]

/* [Camera] */
D800_AXIS_BASE    = 52.0; // mm, lens axis above the body's own baseplate
D800_TRIPOD_IN    = 44;   // mm, lens axis → tripod along the base
// How far the front of the body reaches past its own F flange. This sets
// the arm tube length and therefore the chassis size — see params.scad.
D800_PROUD        = 13.0; // [8:0.5:24]

/* [Body Alignment] */
// Ghost offsets in each arm's local frame, for eyeballing clearances.
BODY_R_X = 10; // [-20:0.5:20]
BODY_R_Y = 13; // [-20:0.5:20]
BODY_R_Z = -5; // [-20:0.5:20]
BODY_T_X = -13; // [-20:0.5:20]
BODY_T_Y = 10; // [-20:0.5:20]
BODY_T_Z = -5; // [-20:0.5:20]

/* [Shell] */
SHELL = "full"; // [full:Full (one material), inner:Inner PETG, outer:Outer PCTG, logo:Logo inlay]
// Fills the wall pockets in the preview. The chassis STL stays pocketed;
// each colour is still its own STL (chassis_logo_*).
LOGO_LAYER = "all"; // [all:All, fx:Gold FX, word:PAN, outline:Red outline, mp:65MP, rule:Hairline, spec:Native, ana_mp:130MP, ana_rule:Ana hairline, ana:Anamorphic, stripe:Red line]

/* [Mount] */
ARM_MOUNT = 0; // [0:reverse ring, 1:printed F, 2:helicoid F]
F_MOUNT_CLOCK = 0;
STEM = 1; // [0:EL 180 helicoid, 1:EL 180 infinity, 2:Nikkor-W 180 helicoid]
EL180_M62_PITCH = 1.0; // [0.75, 1.0]

/* [Optics check] */
// Drives the baffle apertures and the preview envelope. f/11 is the default
// because the 44 mm F throat only passes the frame corners from f/8.4, so
// baffles cut for f/5.6 would be no baffles at all. Set it to 5.6 to see how
// much the corners lose wide open.
FSTOP = 11; // [5.6, 8, 11, 16, 22]

screw_resolution = $preview ? 0.6 : 0.25;
ex = EXPLODED ? 55 : 0;
lid_lift = EXPLODED ? lid_explode_z() : 0;

// -----------------------------------------------------------------------------
// tags — every part in this body is fxp_*
// -----------------------------------------------------------------------------
function fxp_tag(name) = str("fxp_", name);
function w_arm_part() =
    PART == "arm_r_w" || PART == "arm_t_w"
    || PART == "arm_r_fw" || PART == "arm_t_fw"
    || PART == "arm_r_hw" || PART == "arm_t_hw"
    || PART == "arm_r_focus";
function arm_extra() = (nw_stem() || w_arm_part()) ? W_ARM_EXTRA : 0;
function fxp_arm_tag(mark) =
    str("fxp_arm_", mark == "T" ? "t" : "r",
        printed_f() ? "f" : "",
        arm_extra() > 0 ? "w" : "");

function printed_f() =
    (ARM_MOUNT == 1) || PART == "arm_r_f" || PART == "arm_t_f"
    || PART == "arm_r_focus"
    || PART == "arm_r_fw" || PART == "arm_t_fw"
    || PART == "arm_r_wl" || PART == "arm_t_wl";
function heli_cam() =
    ARM_MOUNT == 2 || PART == "arm_r_h" || PART == "arm_t_h"
    || PART == "arm_r_hw" || PART == "arm_t_hw"
    || PART == "fmount_h_r" || PART == "fmount_h_t";
// Infinity register in the arm's own frame (cookie back at z = 0). Same
// station as the fixed arms. T is shorter by the glass path.
function cam_heli_register_z(mark) =
    patch_t() + mount_standoff() + arm_extra() + CAM_RECESS
    - (mark == "T" ? bs_t_comp() : 0);
// Shoulder the male bottoms on. The mesh register is F_FMOUNT_STACK
// further out.
function cam_heli_face_z() = patch_t() + cam_face_cap();
// Floor of the recess. The bought male bottoms here.
function cam_heli_seat_z() = cam_heli_face_z() - CAM_HELI_RECESS;
// Front face of the helicoid, collapsed. The printed mount's shoulder
// lands on it. T's mount is shorter; the helicoid itself is the same.
function cam_heli_front_z() = cam_heli_body_z() + cam_heli_proud();
// Body's rear face, floated off the seat by the lip under the male's tip.
function cam_heli_body_z() = cam_heli_seat_z() + CAM_HELI_FLOAT;
function cam_heli_lip_z() = cam_heli_body_z() - CAM_HELI_MALE;
function cam_heli_shoulder(mark) =
    cam_heli_register_z(mark) - F_FMOUNT_STACK - cam_heli_front_z();
// Best focus the fixed W arms found: T by the glass path (arm_t_fw), R by
// r_focus_pull() (arm_r_focus, plate centred).
function cam_heli_focus_z(mark) =
    cam_heli_register_z(mark) - (mark == "T" ? 0 : r_focus_pull());
// Register on the metal F ring, helicoid collapsed.
function cam_heli_ring_z() = cam_heli_front_z() + CAM_F_RING;
// Extension that brings that body to focus. It only extends.
function cam_heli_dial(mark) = cam_heli_focus_z(mark) - cam_heli_ring_z();
// Fixed printed-F register for the W on the lens helicoid, arm frame.
function wl_register_z(mark) =
    cam_heli_ring_z() + W_INF_BODY_T
    - cam_heli_proud() - W_LENS_HELI_BODY - W_LENS_INF_MARGIN
    + (mark == "T" ? 0 : W_WL_PRINTED_R - W_WL_PRINTED_T
                         + W_LENS_FOCUS_R - W_LENS_FOCUS_T);
function wl_tube_len(mark) = wl_register_z(mark) - patch_t() - F_FMOUNT_STACK;
function inf_stem() =
    STEM == 1 || PART == "stem_el180_inf";
function nw_stem() =
    STEM == 2 || PART == "stem_nw180";
function show_isco() = PART == "isco" || PART == "isco_cut";
function mount_stack() = printed_f() ? F_FMOUNT_STACK : F_REV_STACK;
// Narrowest thing in the light path at the flange. The metal reverse ring
// keeps the real 44 mm F throat; the printed bayonet lip is F_STL_THROAT.
function mouth_clear() = printed_f() ? F_STL_THROAT : F_THROAT;
// Widest aperture that puts the whole frame, corners included, through that
// mouth. need_bore() falls as you stop down, so bisect for where it crosses.
// It does not fall to zero: at f/inf the field term alone remains, so a mouth
// narrower than that never passes the corners. The old 38 mm scan was one.
function bore_floor() = need_bore(1e6, FLANGE_F);
function mouth_ever_clean() = mouth_clear() > bore_floor();
function _mouth_fstop(lo, hi, i) =
    i <= 0 ? hi
    : let (m = (lo + hi) / 2)
        need_bore(m, FLANGE_F) > mouth_clear()
            ? _mouth_fstop(m, hi, i - 1)
            : _mouth_fstop(lo, m, i - 1);
function mouth_fstop() = _mouth_fstop(1, 64, 40);

// Arm tube past the cookie. Both mouths put their F register at the same
// station, so the printed F (a 3 mm stack) needs a longer tube than the
// reverse ring (8 mm). CAM_RECESS moves the whole arm in; it does not
// shorten the tube, because the tube is the M52 thread.
function reflect_tube_len()  =
    ARM_TUBE + arm_extra() + F_REV_STACK - mount_stack();
// The transmit leg crosses 1 mm of glass at 45°, which pushes its focus
// back by bs_t_comp(). Shorten the tube by the same amount.
function transmit_tube_len() = reflect_tube_len() - bs_t_comp();
// Printed-F R tube for the Nikkor-W. Same cookie and bayonet as arm_r_fw,
// the W 8 mm included, then pulled in by r_focus_pull() so it focuses
// with arm_t_fw.
function reflect_focus_tube_len() =
    ARM_TUBE + W_ARM_EXTRA + F_REV_STACK - F_FMOUNT_STACK - r_focus_pull();
function patch_t()           = PORT_PATCH_T;

module mm_split() {
    if (SHELL == "inner")
        intersection() { children(0); children(1); }
    else if (SHELL == "outer")
        difference() { children(0); children(1); }
    else
        children(0);
}

// -----------------------------------------------------------------------------
// port frame — cookie drops into a blind rebate, held by four countersunk M3s
// -----------------------------------------------------------------------------
module round_rect(w, h, r) {
    offset(r)
        offset(-r)
            square([w, h], center = true);
}

// Skin is the 4 mm shell. Camera cookies are faced out to it. The infinity
// cookie's rim is too; the lens sits in a step down to the 158.5 seat.
function skin_z() = patch_t();
function cam_face_cap() = skin_z() - patch_t() + CAM_RECESS;
function chassis_shell_t() = skin_z();
function chassis_out()     = BOX_XY + 2 * chassis_shell_t();
// The chamber is only as tall as the plate; the skirt under it is what puts
// the optical axis where the cameras have to stand.
function chassis_out_z()   = BOX_Z + chassis_plinth();

// Cookie outline: a rectangle on camera-up, centred on the bore rather than
// on the face, sized by port_patch_u() and port_patch_v() off the features it
// actually has to carry.
// Square, and wide enough that the infinity step has a land outside the Ø76.
function stem_plate_w() =
    max(port_patch_u(), port_patch_v(""), EL180_LENS_OD + 4);

module port_plate_2d(mark = "", grow = 0) {
    ax = cam_axis(mark);
    w = mark == "" ? stem_plate_w() : port_patch_u();
    h = mark == "" ? stem_plate_w() : port_patch_v(mark);
    translate([ax.x, ax.y])
        rotate([0, 0, port_up_az(mark)])
            round_rect(w + 2 * grow, h + 2 * grow,
                       max(0.4, PORT_PLATE_R + grow));
}

// A cookie is a panel of the body, so it stops where the body's skin does.
// Past the flat part of a face the chassis curves away under it, and without
// this the plate carries straight on into the air over the corner. Clipping
// to the same profile the chassis is extruded from contours the outer face
// down onto it; the bed face is untouched, which is what the part is printed
// on. PORT_BOSS_R is chosen so the whole of this lands inside PORT_EDGE_CHAM.
module port_chassis_clip(mark = "") {
    u   = port_up(mark);
    out = chassis_out();
    // Camera-up is vertical on every face, so the chassis's rounding — which
    // is all in plan — is always across the plate, never along it.
    // The clip ends on the skin for a part that sits on the box face. Camera
    // cookies are placed CAM_RECESS inboard, and the face cap has to reach
    // back out to the skin from that frame — without the lift the cap is
    // trimmed off and the plate sits in the rebate.
    rot = abs(u.x) > 0.5 ? [0, 90, 0] : [-90, 0, 0];
    lift = mark == "" ? 0 : cam_face_cap();
    translate([0, 0, -BOX_XY / 2 + lift])
        rotate(rot)
            linear_extrude(height = 4 * out, center = true)
                round_rect(out, out, PORT_BOSS_R);
}

// Chamfered on the outer face only. The stem prints this face up, so the
// chamfer only narrows the last layers and the bed face stays the full plate.
module port_flange(mark = "") {
    c = min(PORT_EDGE_CHAM, patch_t() - 1.5);
    difference() {
        intersection() {
            hull() {
                linear_extrude(patch_t() - c)
                    port_plate_2d(mark, 0);
                linear_extrude(patch_t())
                    port_plate_2d(mark, -c);
            }
            port_chassis_clip(mark);
        }
        // Same slope the chassis rebate keeps, so the plate clears the cap.
        port_top_seal(mark, patch_t());
    }
}

// Camera cookie. Straight through, same outline on both faces, so the edge
// is a vertical wall and sits flat on the bed. Following the chassis corner
// back through the thickness left a slope there, and that slope is a ledge
// once the flange is the bed face.
module cam_cookie(mark) {
    // Straight wall, but the shifted edge runs past the chassis corner and
    // sits proud of it. Clip that edge to the skin; the other three stay.
    // The world-up edge is cut back to the rebate slope.
    difference() {
        intersection() {
            linear_extrude(patch_t() + cam_face_cap())
                port_plate_2d(mark);
            port_chassis_clip(mark);
        }
        port_top_seal(mark, patch_t() + cam_face_cap());
    }
}

// Camera-up chord at the F mouth so the pentaprism nose clears the OD. It
// rakes back to the full OD at the cookie's outer face and stops dead there:
// below that line the cookie IS the outside of the body. The taper used to be
// specified as a length from the mouth, TUBE_FLASH_L = 11 mm, which on an
// 8 mm tube ran straight past the cookie face and bit a 16 mm notch out of
// the plate — the L.
TUBE_FLASH_KEEP = 27.0;

module tube_flash_waste(mark, out_len) {
    n  = port_up(mark);
    ax = cam_axis(mark);
    z_face = patch_t() + (mark == "" ? 0 : cam_face_cap());
    z1 = z_face + out_len;
    w  = 80;
    if (mark == "R" || mark == "T")
        hull() {
            translate([ax.x + n.x * (TUBE_FLASH_KEEP + w / 2),
                       ax.y + n.y * (TUBE_FLASH_KEEP + w / 2), z1 + 8])
                cube([w, w, 16], center = true);
            translate([ax.x + n.x * (TUBE_OD / 2 + w / 2),
                       ax.y + n.y * (TUBE_OD / 2 + w / 2),
                       z_face + 0.5])
                cube([w, w, 1], center = true);
        }
}

// Four M3s, two each side of the bore, tracking cam_axis, so the cookie can
// be screwed down after it has dropped into its rebate.
module port_clamp_screws(mark = "") {
    for (up = [-1, 1], side = [-1, 1]) {
        p = clamp_xy(mark, side, up);
        translate([p.x, p.y, 0])
            children();
    }
}

// Flat-head M3, flush with the cookie face. Cut in the cookie, not the box.
module port_csk_cut() {
    translate([0, 0, -1])
        cylinder(h = patch_t() + 2, d = PORT_SCREW_D);
    translate([0, 0, patch_t() - PORT_CSK_H])
        cylinder(h = PORT_CSK_H, d1 = PORT_SCREW_D, d2 = PORT_CSK_D);
    translate([0, 0, patch_t() - 0.01])
        cylinder(h = 0.8, d = PORT_CSK_D);
}

// Tapped into the chamber wall behind the cookie, nut trapped on the inside.
module port_clamp_anchor_cut() {
    translate([0, 0, -WALL - 0.2])
        cylinder(h = WALL + 0.6, d = PORT_SCREW_D);
    translate([0, 0, -WALL - 0.05])
        hex_nut_cut();
}

// Cookie pocket. Closed on all four sides — this is the lid overhang.
//
// The pocket used to sweep open toward the lid, because a cookie used to slide
// in behind a retaining wall. That wall is gone, the plate's outer face is the
// outside of the body, and it goes in from outside; but the channel stayed,
// running the full 4.35 mm deep straight out through the top of the chassis.
// So the chassis's top rim was cut away over 90 of its 100 mm on both camera
// faces and the lid sat over the hole, proud of nothing, on two sides.
//
// Closing it also captures the cookie on four sides instead of three. The
// ceiling is a 4.35 mm ledge off the wall behind it, tied at both ends and
// facing into a pocket a plate then fills — droop there costs nothing.
// World +Z in this face's plane. The pocket ceiling is that edge, and it
// is the one the slicer leaves open: a 4 mm ledge with nothing under it.
function face_up_local(mark) =
    mark == "R" ? [-1, 0] :
    mark == "T" ? [0, -1] : [0, 1];

// How far `dir` reaches on the cookie outline, corner radius ignored.
function port_support(mark, dir) =
    let (u = port_up(mark),
         v = [-u.y, u.x],
         hu = (mark == "" ? stem_plate_w() : port_patch_u()) / 2,
         hv = (mark == "" ? stem_plate_w() : port_patch_v(mark)) / 2,
         ax = cam_axis(mark))
        ax.x * dir.x + ax.y * dir.y
        + hu * abs(u.x * dir.x + u.y * dir.y)
        + hv * abs(v.x * dir.x + v.y * dir.y);

// 45° along the world-up edge. Inner layers stay full depth; the outer
// skin closes on the slope, so the rim is not a line in free air.
// 1.2 mm stays clear of the countersinks, which sit ~2 mm in from the edge.
PORT_TOP_SEAL = 1.2;

module port_top_seal(mark, depth) {
    fu = face_up_local(mark);
    edge = port_support(mark, fu);
    ang = atan2(fu.y, fu.x);
    seal = PORT_TOP_SEAL;
    rotate([0, 0, ang])
        translate([0, -120, 0])
            rotate([90, 0, 0])
                linear_extrude(240)
                    polygon([
                        [edge - seal, depth + 0.3],
                        [edge + 0.8, depth + 0.3],
                        [edge + 0.8, depth - seal],
                        [edge, depth - seal],
                        [edge - seal, depth]
                    ]);
}

module port_slide_slot(mark = "", extra = 0) {
    d = patch_t() + 0.35 + extra;
    // Outer end of the rebate. extra shifts the whole pocket inward.
    z_out = d - 0.2 - extra;
    // extra deepens the floor. The mouth stays at the skin.
    difference() {
        translate([0, 0, d / 2 - 0.2 - extra])
            linear_extrude(d, center = true)
                port_plate_2d(mark, PORT_SLOT_CLEAR / 2);
        port_top_seal(mark, z_out);
    }
}

// 3 mm ring into the chassis top shelf. It used to be notched out over each
// port face to let a cookie slide past; nothing passes here now.
module lid_align_lip() {
    s = BOX_XY;
    difference() {
        cube([s - WALL - 2 * LID_GAP,
              s - WALL - 2 * LID_GAP,
              LID_LIP], center = true);
        cube([s - 2 * WALL - 0.6,
              s - 2 * WALL - 0.6,
              LID_LIP + 0.4], center = true);
    }
}

// -----------------------------------------------------------------------------
// port placement
// -----------------------------------------------------------------------------
module at_stem_face() {
    translate([0, -BOX_XY / 2, 0])
        rotate([90, 0, 0])
            children();
}
module at_reflect_face() {
    translate([BOX_XY / 2, 0, 0])
        rotate([0, 90, 0])
            children();
}
module at_transmit_face() {
    translate([0, BOX_XY / 2, 0])
        rotate([-90, 0, 0])
            children();
}
module at_stem()     { at_stem_face()     children(); }
module at_reflect()  { at_reflect_face()  children(); }
module at_transmit() { at_transmit_face() children(); }

module at_each_bore() {
    at_stem_face() children();
    at_reflect_face()
        translate([cam_axis("R").x, cam_axis("R").y, 0])
            children();
    at_transmit_face()
        translate([cam_axis("T").x, cam_axis("T").y, 0])
            children();
}

// -----------------------------------------------------------------------------
// chassis
// -----------------------------------------------------------------------------
module box_bore() {
    s = BOX_XY;
    h = BOX_Z;

    translate([0, 0, WALL / 2])
        cube([s - 2 * WALL, s - 2 * WALL, h - WALL], center = true);

    translate([0, 0, h / 2 - WALL / 2])
        cube([s - 2 * WALL, s - 2 * WALL, WALL + 0.2], center = true);

    translate([0, 0, h / 2 - LID_LIP / 2])
        cube([s - WALL, s - WALL, LID_LIP + 0.1], center = true);

    translate([0, 0, -h / 2 - chassis_plinth() - 0.05]) {
        cylinder(h = tripod_hole_h() + 0.1, d = TRIPOD_INSERT_D);
        cylinder(h = 0.7, d1 = TRIPOD_INSERT_D + 0.6, d2 = TRIPOD_INSERT_D);
    }

    // Optical hole. The helicoid's M42 male (42 mm) passes this; the
    // cookie covers it. Fixed-arm tubes are smaller and still land.
    at_reflect_face()
        translate([cam_axis("R").x, cam_axis("R").y, -WALL / 2])
            cylinder(h = WALL + 2, d = TUBE_ID + 1, center = true);
    at_transmit_face()
        translate([cam_axis("T").x, cam_axis("T").y, -WALL / 2])
            cylinder(h = WALL + 2, d = TUBE_ID + 1, center = true);
    // Big enough for the helicoid nut. The infinity stem stops at this
    // hole; only the lens barrel passes into the chamber.
    at_stem_face()
        translate([0, 0, -WALL / 2])
            cylinder(h = WALL + 2, d = HELI_NUT_OD + 0.8, center = true);

    floor_hex_cut();
}

// The plinth under the chamber is a solid slab. A thin lip stays at the
// walls. The only wide solid patch is under the floor stamp.
FLOOR_HEX_SKIN = 2.0;
FLOOR_HEX_RIM  = 1.2;
FLOOR_HEX_FLAT = 8.0;    // hole, flat to flat
FLOOR_HEX_WALL = 1.0;    // web between flats
// box_floor_stamp sits on the −X side of the chamber floor, text along Y.
// Just the ink: "fxp_chassis" plus the export timestamp.
FLOOR_LABEL_X = 3.2;
FLOOR_LABEL_Y = 26;

module floor_hex_cut() {
    z0 = -BOX_Z / 2 - chassis_plinth() + FLOOR_HEX_SKIN;
    z1 = -BOX_Z / 2 + WALL + 0.4;
    span = BOX_XY - 2 * WALL - 2 * FLOOR_HEX_RIM;
    // Flat-top hexes. Neighbours sit FLAT+WALL apart, measured across the flats.
    s = FLOOR_HEX_FLAT + FLOOR_HEX_WALL;
    x_pitch = s * sqrt(3);
    hole = 2 * FLOOR_HEX_FLAT / sqrt(3);
    n = ceil(span / s) + 2;
    hx = hole / 2;
    hy = FLOOR_HEX_FLAT / 2;
    lim = span / 2;
    // Cells the insert reaches keep a solid floor tall enough for it,
    // with TRIPOD_KEEP of plastic between the hole and the hex.
    z_fill = -BOX_Z / 2 - chassis_plinth() + tripod_hole_h() + TRIPOD_KEEP;
    for (j = [-n : n], i = [-n : n]) {
        x = i * x_pitch + (abs(j) % 2) * x_pitch / 2;
        y = j * s / 2;
        label_x = -(BOX_XY / 2 - WALL - 4.2);
        on_label = abs(x - label_x) < FLOOR_LABEL_X + hx
                && abs(y) < FLOOR_LABEL_Y + hy;
        if (abs(x) + hx <= lim && abs(y) + hy <= lim && !on_label) {
            za = norm([x, y]) < TRIPOD_INSERT_D / 2 + hx ? z_fill : z0;
            translate([x, y, za - 0.2])
                cylinder(h = z1 - za + 0.6, d = hole, $fn = 6);
        }
    }
}

// Tray stop on the −X side, the wall the logo window removed. The other
// three walls already stop the tray. The window opens down into the
// plinth, so the stop rises from the window sill, solid all the way down,
// and its face stands where the wall's would.
TRAY_STOP_H = 6;   // over the chamber floor
TRAY_STOP_T = 3;
module floor_tray_lip() {
    z0 = logo_cookie_z0() - 0.2;
    z1 = -BOX_Z / 2 + WALL + TRAY_STOP_H;
    tray_x = -(BOX_XY - 2 * WALL - 0.8) / 2;
    x1 = tray_x - 0.35;
    span = BOX_XY - 2 * WALL - 1;
    translate([x1 - TRAY_STOP_T, -span / 2, z0])
        cube([TRAY_STOP_T, span, z1 - z0]);
}

// [x, y, azimuth of the slot from the nut back into the chamber].
function lid_screws() = [
    [ LID_SCREW_A, LID_SCREW_B, 180],
    [-LID_SCREW_B, LID_SCREW_A, 270]
];
function lid_nut_r() = PORT_NUT_AF / cos(30) / 2;
function lid_nut_slot() = LID_SCREW_A - (BOX_XY / 2 - WALL) + lid_nut_r() + 0.3;

// M3 hex fed from the chamber, flats on the slot walls so it cannot turn.
// Its far end is the screw axis; the tray wall closes the mouth. Roof
// stays solid so the lid screw can clamp.
module lid_body_fastener_cuts() {
    nut_z = BOX_Z / 2 - LID_NUT_DROP;
    for (p = lid_screws()) {
        translate([p[0], p[1], nut_z - 4])
            cylinder(h = BOX_Z / 2 - nut_z + 5, d = PORT_SCREW_D);
        translate([p[0], p[1], nut_z])
            rotate([0, 0, p[2]])
                hull()
                    for (x = [0, lid_nut_slot()])
                        translate([x, 0, 0])
                            cylinder(h = PORT_NUT_T + 0.25, r = lid_nut_r(),
                                     $fn = 6, center = true);
    }
}

module hex_nut_cut() {
    cylinder(h = PORT_NUT_T + 0.2, d = PORT_NUT_AF / cos(30), $fn = 6);
}

module port_letter_2d(kind) {
    module stamp(letter) {
        translate([-4.6, 0])
            polygon([[0, 2.6], [-1.7, -1.4], [1.7, -1.4]]);
        translate([3.2, 0])
            text(letter, size = 5.2, font = "Liberation Sans:style=Bold",
                 halign = "center", valign = "center");
        translate([3.2, -5.6])
            text("FXP", size = 3.0, font = "Liberation Sans:style=Bold",
                 halign = "center", valign = "center");
    }
    if (kind == "R")
        rotate(90)  stamp("R");
    else
        rotate(180) stamp("T");
}

// Part tag, along the plate edge opposite the lid. That is the one edge with
// nothing on it: the tube fills the middle out to TUBE_OD/2, the clamp screws
// sit on the two edges across camera-up, flange_marks owns camera-up itself,
// and the lock lugs come down either side of this edge without reaching it.
module fxp_port_stamp(name, mark = "") {
    e = port_patch_u() / 2 - PORT_EDGE_CHAM - 2.8;
    a = port_up_az(mark) + 180;
    ax = cam_axis(mark);
    translate([ax.x + e * cos(a), ax.y + e * sin(a), patch_t() - STAMP_DEPTH])
        rotate([0, 0, a + 90])
            linear_extrude(STAMP_DEPTH + 0.15)
                part_stamp_2d(name, 3.4);
}

module flange_marks(kind) {
    t = 0.8;
    ax = cam_axis(kind);
    u  = port_up(kind);
    translate([ax.x + u.x * port_clamp_r(),
               ax.y + u.y * port_clamp_r(),
               patch_t() - t])
        linear_extrude(t + 0.15)
            port_letter_2d(kind);
}

module chassis_port_mark(kind) {
    t = 0.8;
    ax = cam_axis(kind);
    u  = port_up(kind);
    translate([ax.x + u.x * port_clamp_r(),
               ax.y + u.y * port_clamp_r(), -t])
        linear_extrude(t + 0.15)
            port_letter_2d(kind);
}

module box_fastener_cuts() {
    lid_body_fastener_cuts();
    at_stem_face() {
        port_slide_slot("", stem_drop());
        port_clamp_screws("") port_clamp_anchor_cut();
        translate([0, 0, patch_t() - stem_drop() - 0.3])
            cylinder(h = stem_drop() + 1.3,
                     d = M65_HELI_OD + M65_HELI_CLEAR, $fn = 160);
    }
    at_reflect_face() {
        port_slide_slot("R", CAM_RECESS);
        port_clamp_screws("R") port_clamp_anchor_cut();
        chassis_port_mark("R");
    }
    at_transmit_face() {
        port_slide_slot("T", CAM_RECESS);
        port_clamp_screws("T") port_clamp_anchor_cut();
        chassis_port_mark("T");
    }
}

module box_lining_mask() {
    s = BOX_XY;
    h = BOX_Z;
    L = INNER_LINING;
    difference() {
        translate([0, 0, (WALL - L) / 2])
            cube([s - 2 * (WALL - L),
                  s - 2 * (WALL - L),
                  h - (WALL - L)], center = true);
        translate([0, 0, WALL / 2])
            cube([s - 2 * WALL, s - 2 * WALL, h - WALL + 0.4], center = true);
    }
    translate([0, 0, -h / 2 + WALL - FLOOR_SKIN - (L - FLOOR_SKIN) / 2])
        cube([s - 2 * WALL + 2 * L,
              s - 2 * WALL + 2 * L,
              L - FLOOR_SKIN], center = true);
    module bore_liner(d) {
        translate([0, 0, -WALL / 2])
            difference() {
                cylinder(h = WALL + 0.4, d = d + 2 * L, center = true);
                cylinder(h = WALL + 0.8, d = d, center = true);
            }
    }
    at_reflect_face()
        translate([cam_axis("R").x, cam_axis("R").y, 0])
            bore_liner(TUBE_ID + 1);
    at_transmit_face()
        translate([cam_axis("T").x, cam_axis("T").y, 0])
            bore_liner(TUBE_ID + 1);
    at_stem_face()
        bore_liner(HELI_NUT_OD + 0.8);
}

// -----------------------------------------------------------------------------
// FXPAN wall badge — colour-separated STLs from logos/fxpan_gen.py (gold FX
// + sweep, white PAN, red outline) then 65MP over the native stitch and
// 130MP over the 2× anamorphic delivery. The mark is projected to 2D so the
// existing offset / extrude plug fit still applies. Spec type is Futura,
// which ships with macOS — re-exporting on Linux needs the same family.
// layer: all | fx | word | outline | mp | rule | spec | ana_mp | ana_rule |
//        ana | stripe.
// -----------------------------------------------------------------------------
// Native bounding box of logos/fxpan_outline_red.stl. Gold and PAN share
// that origin, so one translate keeps the three layers registered.
LOGO_ART_FILE = "../../logos";
LOGO_ART_X0   = -1.200;
LOGO_ART_Y0   = -3.963;
LOGO_ART_W    = 143.367;
LOGO_ART_H    = 74.771;

// 7.60, not 9.05: the upper screws follow the badge, and the rebate
// now stops 1 mm short of the arris so the slicer can cap it. The old
// centre put the countersinks through that cap.
function fx_word_y()      = 7.60;   // mark centre on the wall
function logo_art_scale() = SPEC_W / LOGO_ART_W;
function logo_art_h()     = LOGO_ART_H * logo_art_scale();
function logo_art_bottom()= fx_word_y() - logo_art_h() / 2;
function fx_mp_y()        = logo_art_bottom() - 3.8;
function fx_rule_y()      = fx_mp_y() - 4.8;
function fx_spec_y()      = fx_mp_y() - 9.2;
function fx_ana_mp_y()    = fx_mp_y() - 19.1;
function fx_ana_rule_y()  = fx_mp_y() - 23.9;
function fx_ana_y()       = fx_mp_y() - 28.3;

module fxpan_art_stl(name) {
    translate([0, fx_word_y()])
        scale(logo_art_scale())
            translate([-LOGO_ART_X0 - LOGO_ART_W / 2,
                       -LOGO_ART_Y0 - LOGO_ART_H / 2])
                projection(cut = false)
                    import(str(LOGO_ART_FILE, "/", name), convexity = 12);
}

module fxpan_badge() {
    fxpan_art_stl("fxpan_fx_gold.stl");
}

module fxpan_pan() {
    fxpan_art_stl("fxpan_pan_white.stl");
}

module fxpan_outline() {
    fxpan_art_stl("fxpan_outline_red.stl");
}

// Spec lines share columns measured off the native string in Futura
// Condensed Medium 5 / spacing 1.08, so the middot and the aspect sit
// on the same x whether the label is NATIVE or ANA 2×. Advances are
// baked (textmetrics is still experimental in the GUI).
SPEC_SIZE   = 5.0;
SPEC_SP     = 1.08;
SPEC_W      = 71.9167;   // NATIVE  13248×4912  ·  2.71:1
SPEC_X_LAB  = 16.1316;   // NATIVE
SPEC_X_PIX  = 19.2371;   // NATIVE<two spaces>
SPEC_X_DOT  = 51.9106;   // …4912<two spaces>, left of ·
SPEC_X_AR   = 56.5687;   // …  ·<two spaces>

module fxpan_spec_line(label, pix, ar) {
    specf = "Futura:style=Condensed Medium";
    x0 = -SPEC_W / 2;
    translate([x0 + SPEC_X_LAB, 0])
        text(label, size = SPEC_SIZE, font = specf, spacing = SPEC_SP,
             halign = "right", valign = "center");
    translate([x0 + SPEC_X_PIX, 0])
        text(pix, size = SPEC_SIZE, font = specf, spacing = SPEC_SP,
             halign = "left", valign = "center");
    translate([x0 + SPEC_X_DOT, 0])
        text("·", size = SPEC_SIZE, font = specf, spacing = SPEC_SP,
             halign = "left", valign = "center");
    translate([x0 + SPEC_X_AR, 0])
        text(ar, size = SPEC_SIZE, font = specf, spacing = SPEC_SP,
             halign = "left", valign = "center");
}

module fxpan_mp_mark(s) {
    text(s, size = 6.2, font = "Futura:style=Bold", spacing = 1.12,
         halign = "center", valign = "center");
}

module fxpan_rule() {
    square([SPEC_W, 0.45], center = true);
}

module fxpan_wall_2d(layer = "all") {
    if (layer == "all" || layer == "fx")
        fxpan_badge();
    if (layer == "all" || layer == "word")
        fxpan_pan();
    if (layer == "all" || layer == "outline")
        fxpan_outline();
    if (layer == "all" || layer == "mp")
        translate([0, fx_mp_y()])
            fxpan_mp_mark("65MP");
    if (layer == "all" || layer == "rule")
        translate([0, fx_rule_y()])
            fxpan_rule();
    if (layer == "all" || layer == "spec")
        translate([0, fx_spec_y()])
            fxpan_spec_line("NATIVE", "13248×4912", "2.71:1");
    if (layer == "all" || layer == "ana_mp")
        translate([0, fx_ana_mp_y()])
            fxpan_mp_mark("130MP");
    if (layer == "all" || layer == "ana_rule")
        translate([0, fx_ana_rule_y()])
            fxpan_rule();
    if (layer == "all" || layer == "ana")
        translate([0, fx_ana_y()])
            fxpan_spec_line("ANA 2×", "26496×4912", "5.42:1");
}

// grow  — swell the footprint and deepen the floor (plug interference)
// proud — start this far outside the wall face
// deep  — depth below the wall face, so the pocket keeps its own depth
//         whatever the plugs do
module fxpan_inlay(layer = "all", grow = 0, proud = 0.05,
                   deep = MARK_DEPTH + 0.10) {
    out = chassis_out();
    translate([-out / 2 - proud, 0, 2])
        rotate([90, 0, -90])
            mirror([0, 0, 1])
                linear_extrude(proud + deep + grow)
                    offset(0.02 + grow)
                        scale(LOGO_SCALE)
                            fxpan_wall_2d(layer);
}

// Groove around the plinth, a few millimetres above the floor so the first
// layers stay solid and the cookies (centred on the axis) never reach it.
// proud is an outward offset — the ring has no single face-normal to
// translate along the way the −X badge does.
function stripe_z0() = -BOX_Z / 2 - chassis_plinth() + STRIPE_LIFT;

module fxpan_stripe(grow = 0, proud = 0.05, deep = MARK_DEPTH + 0.10) {
    out = chassis_out();
    translate([0, 0, stripe_z0() - grow])
        linear_extrude(STRIPE_H + 2 * grow)
            difference() {
                offset(0.02 + grow + proud)
                    round_rect(out, out, PORT_BOSS_R);
                offset(-(deep + grow))
                    round_rect(out, out, PORT_BOSS_R);
            }
}

module fxpan_colour(layer = "all", grow = 0, proud = 0.05,
                    deep = MARK_DEPTH + 0.10) {
    if (layer != "stripe")
        fxpan_inlay(layer, grow, proud, deep);
    if (layer == "all" || layer == "stripe")
        fxpan_stripe(grow, proud, deep);
}

// Logo face (−X). The skin there is a cookie: same countersunk M3s and
// trapped nuts as the port plates, so a logo change reprints this panel
// and not the chassis. The red stripe stays on the chassis, below the
// rebate. Art Y maps to world Z as art_y * LOGO_SCALE + 2.
function logo_world_z(art_y) = 2 + art_y * LOGO_SCALE;
function logo_cookie_z0() = stripe_z0() + STRIPE_H + 1.6;
// The rebate used to run out through the top face. That rim is open air,
// and the slicer will not put a skin on it. One millimetre of cap is five
// layers at 0.2 mm, enough for a top shell. The cookie stops under it.
LOGO_TOP_LIP = 1.0;
function logo_cookie_z1() = BOX_Z / 2 - LOGO_TOP_LIP;
LOGO_SCREW_Y = 33;
// One pair beside 65MP, clear of that short word. The other pair sits in
// the blank band above the badge: the spec line is full width, so a hole
// above the chamber floor has to go through it.
function logo_screw_z_hi() =
    let (art_top = logo_world_z(fx_word_y() + logo_art_h() / 2),
         r = PORT_CSK_D / 2)
        art_top + r + 0.6;

module at_logo_screws() {
    for (s = [-1, 1], z = [logo_screw_z_hi(), logo_world_z(fx_mp_y())])
        translate([0, s * LOGO_SCREW_Y, z])
            children();
}

// Outer 4 mm of the −X skin, clipped to the chassis corner, between the
// stripe and a lip under the lid.
module logo_slab(z0, z1, deep = 0, grow = 0) {
    out = chassis_out();
    thick = patch_t() + deep + 0.4;
    x0 = -out / 2 - 0.2;
    intersection() {
        translate([x0 + thick / 2, 0, (z0 + z1) / 2])
            cube([thick, out + 40, max(0.4, z1 - z0)], center = true);
        translate([0, 0, -BOX_Z / 2 - chassis_plinth() - 2])
            linear_extrude(chassis_out_z() + 8)
                if (grow > 0)
                    offset(r = grow)
                        round_rect(out, out, PORT_BOSS_R);
                else
                    round_rect(out, out, PORT_BOSS_R);
    }
}

// 45° along the straight part of the bottom inner edge. The outer face
// keeps the full outline. That face goes on the bed. z_shift lifts the
// chassis copy so the two faces have a little clearance.
function logo_chamfer_span() = chassis_out() + 24;
// 45° through the whole plate. The cut starts outside the outer face and
// runs past the inner face, so no vertical lip is left behind the angle.
module logo_bed_chamfer(z_shift = 0) {
    x0 = -chassis_out() / 2 - 0.6;
    run = patch_t() + 1.6;
    translate([x0, 0, logo_cookie_z0() + z_shift])
        rotate([90, 0, 0])
            linear_extrude(logo_chamfer_span(), center = true)
                polygon([[0, -1], [run, -1], [run, run - 0.6], [0, -0.6]]);
}

// 45° under the 1 mm cap, outer face only. Printed floor-down the arris
// steps out a layer at a time instead of a perimeter hung over the pocket.
module logo_top_chamfer() {
    x0 = -chassis_out() / 2 - 0.6;
    translate([x0, 0, BOX_Z / 2])
        rotate([90, 0, 0])
            linear_extrude(logo_chamfer_span(), center = true)
                polygon([[0.4, 0], [0.4, -LOGO_TOP_LIP], [0.4 + LOGO_TOP_LIP + 0.3, -LOGO_TOP_LIP]]);
}

module logo_csk() {
    rotate([0, 90, 0]) {
        translate([0, 0, -0.8])
            cylinder(h = 0.7, d = PORT_CSK_D);
        cylinder(h = PORT_CSK_H + 0.4, d1 = PORT_CSK_D, d2 = PORT_SCREW_D);
        cylinder(h = patch_t() + 1.2, d = PORT_SCREW_D);
    }
}

// Meat behind the cookie: the nut, plus the web the screw pulls against.
// The rebate (logo_slab overshoot + LOGO_REBATE_DEEP) lands 0.75 mm
// past the 4 mm skin. Measuring the old 1 mm web from the skin left
// 0.3 mm, which the slicer drops. LOGO_NUT_WEB is from the rebate floor.
LOGO_REBATE_DEEP = 0.35;
function logo_rebate_x() =
    -chassis_out() / 2 - 0.2 + patch_t() + LOGO_REBATE_DEEP + 0.4;
LOGO_NUT_WEB = 2.0;
function logo_nut_stop_x() = logo_rebate_x() + LOGO_NUT_WEB;
function logo_frame_t() =
    logo_nut_stop_x() + PORT_NUT_T + 0.15
    - (-chassis_out() / 2 + patch_t());
function logo_inner_x() = -chassis_out() / 2 + patch_t() + logo_frame_t();

// Pare the logo wall back to that nut rail, outboard of the cartridge,
// then open the middle so only the rail is left.
module logo_frame_window() {
    x_nut = logo_inner_x();
    y_span = (BOX_XY - 2 * WALL) - 1;
    z_floor = -BOX_Z / 2 + WALL;
    // The opening runs to the side walls. Each nut is a pad tied to the
    // nearest side edge and the nearer horizontal edge. The ties land
    // at 45°, so the chassis prints floor-down with nothing in mid-air.
    x0 = -chassis_out() / 2 + patch_t() - 0.3;
    win_y = (BOX_XY - 2 * WALL) - 4;
    win_z0 = logo_cookie_z0() + 3;
    win_z1 = logo_cookie_z1() - 3;
    nut_d = PORT_NUT_AF / cos(30);
    module logo_nut_keepers() {
        xa = x0 - 0.4;
        // Stop on the chamber face. Past that, the pad caps the mouth
        // and the nut cannot be put in from inside.
        xb = x_nut;
        half_y = win_y / 2;
        pad_d = nut_d + 3.2;
        module ax(y, z, d) {
            translate([(xa + xb) / 2, y, z])
                rotate([0, 90, 0])
                    cylinder(h = xb - xa, d = d, center = true, $fn = 24);
        }
        // Upper nuts. A round pad here is a bar in the opening. The
        // plastic is a wedge: 45° up from the side wall to the nut,
        // so each layer sits on the one below.
        module upper_web(s, sy, sz) {
            ye = s * half_y;
            // Past the hex, not through its middle. The old face sat on
            // the nut centre and cut the hole in half.
            y_far = sy - s * (nut_d / 2 + 1.0);
            z_top = max(sz + nut_d / 2 + 1.0, logo_rail_z());
            z_lo = sz - nut_d / 2 - 0.8;
            z_foot = z_lo - abs(ye - y_far);
            translate([xa, 0, 0])
                rotate([0, 90, 0])
                    linear_extrude(xb - xa)
                        polygon([
                            [-z_top, y_far],
                            [-z_top, ye],
                            [-z_foot, ye],
                            [-z_lo, y_far]
                        ]);
        }
        for (s = [-1, 1]) {
            sy = s * LOGO_SCREW_Y;
            sz_hi = logo_screw_z_hi();
            sz_lo = logo_world_z(fx_mp_y());
            ye = s * half_y;
            upper_web(s, sy, sz_hi);
            // Lower pair: the side wall is beside the pad, and the web
            // down to the opening's lower edge is steeper than 45°.
            gap = max(1.2, abs(ye - sy) - pad_d / 2);
            hull() {
                ax(sy, sz_lo, pad_d);
                ax(ye, sz_lo - gap, 2.4);
                ax(ye, sz_lo + gap, 2.4);
            }
            hull() {
                ax(sy, sz_lo, pad_d);
                ax(ye, win_z0, 2.4);
            }
        }
    }
    difference() {
        union() {
            // Thin the wall back to the nut rail, above the floor and in the plinth.
            translate([(x_nut - 39.2) / 2, 0, (z_floor + BOX_Z / 2) / 2])
                cube([-39.2 - x_nut, y_span, BOX_Z / 2 - z_floor + 0.4], center = true);
            translate([(x_nut - 40.6) / 2, 0, (logo_cookie_z0() + z_floor) / 2])
                cube([-40.6 - x_nut, y_span, z_floor - logo_cookie_z0()], center = true);
            translate([(x0 + x_nut + 0.4) / 2, 0, (win_z0 + win_z1) / 2])
                cube([x_nut + 0.4 - x0, win_y, win_z1 - win_z0], center = true);
        }
        logo_nut_keepers();
        logo_lid_rim();
    }
}

// Underside of the lid rail. It has to clear the logo-cookie nuts.
function logo_rail_z() =
    logo_screw_z_hi() + (PORT_NUT_AF / cos(30)) / 2 + 1.2;

// The rail stays above the logo nuts; a post ties it down at each end.
module logo_lid_rim() {
    x0 = -chassis_out() / 2 + patch_t() + 0.2;
    x1 = -(BOX_XY / 2 - WALL);
    z_top = BOX_Z / 2 + 0.3;
    nut_z = BOX_Z / 2 - LID_NUT_DROP;
    z0 = logo_rail_z();
    translate([(x0 + x1) / 2, 0, (z0 + z_top) / 2])
        cube([x1 - x0, BOX_XY - 4, max(1.2, z_top - z0)], center = true);
    for (sy = [-1, 1])
        translate([(x0 + x1) / 2,
                   sy * (BOX_XY / 2 - LID_SCREW + 1.4),
                   (nut_z - 5 + z_top) / 2])
            cube([x1 - x0, 8, z_top - (nut_z - 5)], center = true);
}

module logo_inner_nuts() {
    nut_d = PORT_NUT_AF / cos(30);
    // Screw comes through the cookie and pulls the nut that way.
    // The hex opens into the chamber. LOGO_NUT_WEB on the cookie side
    // stops the nut, and only the 3.2 mm screw hole goes through it.
    for (s = [-1, 1], z = [logo_screw_z_hi(), logo_world_z(fx_mp_y())]) {
        y = s * LOGO_SCREW_Y;
        translate([logo_inner_x() + 1.2, y, z])
            rotate([0, -90, 0])
                cylinder(h = 1.2 + PORT_NUT_T + 0.15, d = nut_d, $fn = 6);
        translate([logo_rebate_x() - 0.4, y, z])
            rotate([0, 90, 0])
                cylinder(h = LOGO_NUT_WEB + 1.0, d = PORT_SCREW_D);
    }
}

module at_logo_face_cuts() {
    m = PORT_SLOT_CLEAR / 2;
    // Rebate, but leave the mating 45° at the bed and a capped rim on top.
    difference() {
        logo_slab(logo_cookie_z0() - m, logo_cookie_z1() + 0.25, LOGO_REBATE_DEEP, m);
        logo_bed_chamfer(0.2);
    }
    logo_top_chamfer();
    logo_frame_window();
    logo_inner_nuts();
}

module part_logo_cookie() {
    color("SlateGray")
    difference() {
        logo_slab(logo_cookie_z0(), logo_cookie_z1());
        logo_bed_chamfer();
        translate([-chassis_out() / 2, 0, 0])
            at_logo_screws()
                logo_csk();
        // Full inlay. The old clip sat patch_t() (4 mm) above the arris
        // and sheared the ANA line; the 45° only climbs MARK_DEPTH
        // across the engraving, and logo_bed_chamfer() already takes
        // the angle. That line clears it.
        fxpan_inlay("all");
        translate([-chassis_out() / 2 + patch_t(), 0, 0])
            rotate([0, -90, 0])
                part_stamp_cut(fxp_tag("logo"), size = 2.4);
    }
}

module chassis_blank() {
    dz  = chassis_plinth();
    h   = BOX_Z + dz;
    out = chassis_out();
    translate([0, 0, -BOX_Z / 2 - dz])
        linear_extrude(h)
            round_rect(out, out, PORT_BOSS_R);
}

// One colour, clipped to the chassis so a glyph cannot cross a bore.
// The proud lip is the part that stands off the wall face.
module logo_plug(layer) {
    union() {
        intersection() {
            difference() {
                chassis_blank();
                box_bore();
                box_fastener_cuts();
            }
            fxpan_colour(layer, LOGO_FIT, 0);
        }
        fxpan_colour(layer, LOGO_FIT, LOGO_PROUD, 0.4);
    }
}

module logo_fills() {
    // Same plugs the colour STLs export, drawn into the pockets. No second
    // chassis boolean — the pocket cut already made the seat.
    module one(layer, c) {
        if (LOGO_LAYER == "all" || LOGO_LAYER == layer)
            color(c) {
                fxpan_colour(layer, LOGO_FIT, 0);
                fxpan_colour(layer, LOGO_FIT, LOGO_PROUD, 0.4);
            }
    }
    one("fx", "Gold");
    one("word", "White");
    one("outline", "Crimson");
    one("mp", "White");
    one("rule", "Crimson");
    one("spec", "White");
    one("ana_mp", "White");
    one("ana_rule", "Crimson");
    one("ana", "White");
    one("stripe", "Crimson");
}

module chassis_body() {
    color("SlateGray")
    mm_split() {
        union() {
        difference() {
            chassis_blank();
            box_bore();
            box_fastener_cuts();
            // box_floor_stamp is written for a cube; feed it the XY size and
            // drop it to the real floor, which is BOX_Z deep.
            translate([0, 0, -(BOX_Z - BOX_XY) / 2])
                box_floor_stamp(fxp_tag("chassis"), BOX_XY, WALL);
            if (SHELL == "full" || SHELL == "logo")
                fxpan_colour("stripe");
            at_logo_face_cuts();
        }
        floor_tray_lip();
        }
        union() {
            box_lining_mask();
            if (SHELL == "outer")
                fxpan_colour("stripe");
        }
    }
}

module part_chassis() {
    // Full / inner / outer always pocket every layer so the colour STLs seat.
    // SHELL=logo exports one LOGO_LAYER as a drop-in. The assembly preview
    // draws those plugs back into the pockets; see logo_fills().
    if (SHELL == "logo")
        color("SlateGray") logo_plug(LOGO_LAYER);
    else
        chassis_body();
}

// -----------------------------------------------------------------------------
// tubes
// -----------------------------------------------------------------------------
module along_tube(rx = 0, ry = 0) {
    translate([0, 0, patch_t()])
        rotate([rx, ry, 0])
            children();
}

module along_cam(rx = 0, ry = 0, mark = "") {
    ax = cam_axis(mark);
    translate([ax.x, ax.y, 0])
        along_tube(rx, ry)
            children();
}

// Ring baffle. ID follows need_bore() at this station so the tooth never
// shadows the shifted bundle at FSTOP.
function baffle_id(mark, out_len, z) =
    let (b = d_plate_to_mount() - (out_len - z))
        min(TUBE_ID - 1.0, max(F_BORE - 2, need_bore(FSTOP, b + FLANGE_F) + 1.0));

module tube_baffle_tooth(id) {
    rotate_extrude()
        polygon([
            [id / 2,           0],
            [TUBE_ID / 2 - 0.02, 0],
            [TUBE_ID / 2 - 0.02, BAFFLE_H],
            [id / 2,           BAFFLE_H]
        ]);
}

module tube_baffles(out_len, mark = "") {
    z0 = 8;
    z1 = out_len - (printed_f() ? F_PEG_H + MASK_T + 1.2 : F_REV_LEN + 1.2);
    if (z1 > z0 + BAFFLE_H)
        for (z = [z0 : BAFFLE_PITCH : z1 - BAFFLE_H])
            translate([0, 0, z])
                difference() {
                    cylinder(h = BAFFLE_H, d = TUBE_ID - 0.02);
                    translate([0, 0, -0.1])
                        cylinder(h = BAFFLE_H + 0.2,
                                 d1 = baffle_id(mark, out_len, z),
                                 d2 = TUBE_ID - 0.02);
                }
}

// Glare stop in the F throat. The window has to pass the whole shifted
// bundle, so it is set from the sensor plus MASK_CLEAR, not from F_BORE.
module f_glare_mask(out_len, mark) {
    roll = mark == "T" ? 180 : 90;
    z = printed_f() ? out_len - F_PEG_H - MASK_T : out_len - F_REV_LEN - MASK_T;
    od = TUBE_ID + 0.6;
    translate([0, 0, z])
        difference() {
            cylinder(h = MASK_T, d = od);
            translate([0, 0, -0.2])
                linear_extrude(MASK_T + 0.4)
                    rotate([0, 0, roll])
                        offset(r = 2)
                            offset(delta = -2)
                                square([SENSOR_W + 2 * MASK_CLEAR,
                                        SENSOR_H + 2 * MASK_CLEAR],
                                       center = true);
        }
}

module tube_lining_mask(out_len, rx = 0, ry = 0, mark = "", m62 = 0) {
    L = INNER_LINING;
    ax = cam_axis(mark);
    h = patch_t() + out_len + 0.2;
    translate([ax.x, ax.y, -0.2])
        rotate([rx, ry, 0])
            difference() {
                cylinder(h = h, d = TUBE_ID + 2 * L);
                translate([0, 0, -0.4])
                    cylinder(h = h + 0.8, d = TUBE_ID - 0.4);
            }
    // Inner PETG owns threaded zones; the PCTG outer is nut-seat meat only.
    if (m62 > 0)
        translate([ax.x, ax.y, patch_t() + out_len - 0.2])
            cylinder(h = m62 + 0.4, d = EL180_M62_MAJOR + 2 * L);
    if (!printed_f() && mark != "")
        translate([ax.x, ax.y, patch_t() + out_len - F_REV_LEN - 0.2])
            cylinder(h = F_REV_LEN + 0.6, d = F_REV_MAJOR + 2 * L + 0.4);
    // No liner in the F throat: it is the tightest aperture in the body,
    // 1.3 mm clear of the frame corners even at f/11, so anything in there
    // would vignette outright. Flocking handles glare instead.
    if (mark != "")
        along_cam(rx, ry, mark) {
            tube_baffles(out_len, mark);
            f_glare_mask(out_len, mark);
        }
}

module port_tube_solid(out_len, rx = 0, ry = 0, mark = "") {
    ax = cam_axis(mark);
    difference() {
        union() {
            if (mark != "")
                cam_cookie(mark);
            else
                port_flange(mark);
            if (out_len > 0.05)
                along_cam(rx, ry, mark)
                    cylinder(h = out_len, d = TUBE_OD);
        }
        along_cam(rx, ry, mark)
            translate([0, 0, -patch_t() - 2])
                cylinder(h = patch_t() + out_len + 4, d = TUBE_ID);
        tube_flash_waste(mark, out_len);
        // Printed-F cookies are cam_face_cap thicker, and the inner edge is
        // a 45° face. The old cut started above the back and left a web.
        if (printed_f())
            port_clamp_screws(mark) cam_csk_cut();
        else
            translate([0, 0, mark == "" ? 0 : cam_face_cap()])
                port_clamp_screws(mark) port_csk_cut();
    }
}

// 45° face along the inner long edge, on the chassis side of the cookie.
// The outer face keeps the full outline. Lay this face on the bed.
module cookie_print_flat(mark) {
    H = patch_t() + cam_face_cap();
    ax = cam_axis(mark);
    half_v = port_patch_v(mark) / 2;
    span = port_patch_u() + 30;
    if (mark == "R") {
        translate([ax.x, ax.y + half_v, H])
            rotate([45, 0, 0])
                translate([-span / 2, -40, -40])
                    cube([span, 40, 40]);
    } else {
        translate([ax.x - half_v, ax.y, H])
            rotate([0, 45, 0])
                translate([0, -span / 2, -40])
                    cube([40, span, 40]);
    }
}

module part_camera_tube(out_len, rx = 0, ry = 0, mark = "", tag = "") {
    p = max(port_patch_u(), port_patch_v(mark)) + 2 * sensor_shift();
    color("SlateGray")
    mm_split() {
    intersection() {
    difference() {
        union() {
            port_tube_solid(out_len, rx, ry, mark);
            along_cam(rx, ry, mark) {
                tube_baffles(out_len, mark);
                f_glare_mask(out_len, mark);
                if (!printed_f() && rev_lock_ok(out_len))
                    rev_lock_bosses(out_len, port_up_az(mark));
            }
        }
        if (!printed_f())
            along_cam(rx, ry, mark) {
                translate([0, 0, max(out_len - F_REV_LEN, -patch_t())])
                    f_rev_thread_cut();
                // Lead-in, so the ring can find the first turn square.
                translate([0, 0, out_len - F_REV_LEAD])
                    cylinder(h = F_REV_LEAD + 0.1,
                             d1 = f_rev_minor(),
                             d2 = f_rev_minor() + 2 * F_REV_LEAD);
                if (rev_lock_ok(out_len))
                    rev_lock_cuts(out_len, port_up_az(mark));
                f_pin_line_cut(out_len, port_up_az(mark));
            }
        translate([0, 0, cam_face_cap()]) {
            flange_marks(mark);
            fxp_port_stamp(tag == "" ? fxp_arm_tag(mark) : tag, mark);
        }
        tube_flash_waste(mark, out_len);
        if (printed_f())
            cookie_print_flat(mark);
    }
        translate([-p, -p, 0])
            cube([p * 2, p * 2,
                  patch_t() + out_len + (printed_f() ? 16 : 8)]);
    }
        tube_lining_mask(out_len, rx, ry, mark);
    }
    if (SHELL != "inner") {
    if (printed_f())
        color("Goldenrod")
            difference() {
                along_cam(rx, ry, mark)
                    translate([0, 0, out_len])
                        f_mount_on_tube((mark == "T" ? 0 : -90) + F_MOUNT_CLOCK,
                                        peg_face = 0,
                                        back_extra = FX_FMOUNT_EXTRA);
                tube_flash_waste(mark, out_len);
            }
    else if ($preview && SHOW_BODIES == 0)
        color("Goldenrod", 0.55)
            along_cam(rx, ry, mark)
                translate([0, 0, out_len])
                    difference() {
                        cylinder(h = F_REV_STACK, d = 62);
                        translate([0, 0, -0.1])
                            cylinder(h = F_REV_STACK + 0.2, d = F_BORE);
                    }
    }
}

// -----------------------------------------------------------------------------
// helicoid camera arms. The cookie takes the M42 male of a bought
// M52-female / M42-male 17–31 mm helicoid. The printed mount is an M52
// male into that helicoid's front female.
// Collapsed is infinity. Extending moves the camera out. The tripod screw
// locks it; there is no set screw.
// -----------------------------------------------------------------------------
module cam_csk_cut() {
    h = patch_t() + cam_face_cap();
    translate([0, 0, -1])
        cylinder(h = h + 2, d = PORT_SCREW_D);
    translate([0, 0, h - PORT_CSK_H])
        cylinder(h = PORT_CSK_H + 0.4, d1 = PORT_SCREW_D, d2 = PORT_CSK_D);
}

module part_cam_heli_arm(mark) {
    ax = cam_axis(mark);
    z_seat = cam_heli_seat_z();
    assert(cam_heli_dial(mark) >= 0,
           str("camera helicoid ", mark, " collapses ", -cam_heli_dial(mark),
               " mm past focus on a ", CAM_F_RING, " mm F ring"));
    color("SlateGray")
    mm_split() {
        union() {
        ScrewHole(CAM_HELI_REAR, z_seat + 0.2,
                  position = [ax.x, ax.y, 0],
                  rotation = [0, 0, mark == "T" ? CAM_HELI_CLOCK_T : CAM_HELI_CLOCK_R],
                  pitch = CAM_HELI_PITCH,
                  tolerance = CAM_HELI_TOL,
                  tooth_height = CAM_HELI_TOOTH)
            difference() {
                cam_cookie(mark);
                // Pocket the helicoid body. The male bottoms on the floor.
                // The thread itself is the bore; a clearance cylinder here
                // would wipe it out.
                if (CAM_HELI_RECESS > 0)
                    translate([ax.x, ax.y, z_seat])
                        cylinder(h = cam_heli_face_z() - z_seat + 0.02,
                                 d = CAM_HELI_OD + 0.8);
                port_clamp_screws(mark) cam_csk_cut();
                translate([0, 0, cam_face_cap()]) {
                    flange_marks(mark);
                    fxp_port_stamp(str("fxp_arm_", mark == "T" ? "t" : "r", "h"),
                                   mark);
                }
            }
        // Stop for the male's tip. On the bed.
        translate([ax.x, ax.y, 0])
            difference() {
                cylinder(h = cam_heli_lip_z(), d = CAM_HELI_REAR + 1);
                translate([0, 0, -0.1])
                    cylinder(h = cam_heli_lip_z() + 0.2, d = CAM_HELI_LIP_ID);
            }
        }
        translate([ax.x, ax.y, -0.2])
            cylinder(h = z_seat + 0.5,
                     d = CAM_HELI_REAR + 2 * INNER_LINING + 1.2);
    }
}

// Bought helicoid, collapsed plus `lift`. Sits on the recess floor.
module cam_helicoid_body(lift = 0) {
    h = cam_heli_proud() + lift;
    color("Silver")
        difference() {
            union() {
                translate([0, 0, -CAM_HELI_MALE])
                    cylinder(h = CAM_HELI_MALE + 0.2, d = CAM_HELI_REAR - 1);
                cylinder(h = h, d = CAM_HELI_OD);
                translate([0, 0, h * 0.55])
                    difference() {
                        cylinder(h = 0.8, d = CAM_HELI_OD + 1.2);
                        translate([0, 0, -0.1])
                            cylinder(h = 1.0, d = CAM_HELI_OD - 3);
                    }
            }
            translate([0, 0, -0.2])
                cylinder(h = h + 0.4, d = CAM_HELI_ID);
            translate([0, 0, -CAM_HELI_MALE - 0.2])
                cylinder(h = CAM_HELI_MALE + 0.4, d = CAM_HELI_NECK);
        }
}

// Printed male into the helicoid's front female, then the bayonet.
// z = 0 at the thread tip. The shoulder flares out to the flange so the
// 62 mm disk is not a shelf.
module part_cam_heli_mount(mark) {
    clock = (mark == "T" ? 0 : -90) + F_MOUNT_CLOCK;
    shoulder = cam_heli_shoulder(mark);
    z_mesh = CAM_HELI_FRONT + shoulder;
    color("Goldenrod")
        union() {
            difference() {
                union() {
                    ScrewThread(CAM_HELI_NOSE, CAM_HELI_FRONT + 0.2,
                                pitch = CAM_HELI_PITCH,
                                tolerance = CAM_HELI_TOL,
                                tooth_height = CAM_HELI_TOOTH,
                                tip_height = 1.2);
                    translate([0, 0, CAM_HELI_FRONT - 1.6])
                        cylinder(h = shoulder + 1.8,
                                 d1 = CAM_HELI_NOSE, d2 = F_STL_OD);
                }
                translate([0, 0, -1])
                    cylinder(h = CAM_HELI_FRONT + 1.2, d = CAM_HELI_ID);
                translate([0, 0, CAM_HELI_FRONT - 0.2])
                    cylinder(h = shoulder + 0.5, d = TUBE_ID);
            }
            translate([0, 0, z_mesh])
                rotate([0, 0, clock])
                    f_mount_stl_raw();
        }
}

// Printable stand-in for the bought unit, collapsed. Male tip at z = 0.
// M42 male into the cookie, M52 female for fmount_h_*. Not the real part.
module cam_helicoid_gauge() {
    proud = cam_heli_proud();
    male_h = CAM_HELI_MALE;
    nose_h = CAM_HELI_FRONT + 0.2;
    // Root of the M42 tooth. The bore stays 2 mm inside it so a 0.4 mm
    // nozzle has a shank to print, not a bare coil.
    male_root = CAM_HELI_REAR - CAM_HELI_TOOTH / tan(30);
    color("Silver")
        ScrewHole(CAM_HELI_NOSE, nose_h + 0.2,
                  position = [0, 0, male_h + proud - nose_h],
                  pitch = CAM_HELI_PITCH,
                  tolerance = CAM_HELI_TOL,
                  tooth_height = CAM_HELI_TOOTH)
            difference() {
                union() {
                    translate([0, 0, male_h])
                        rotate([180, 0, 0])
                            ScrewThread(CAM_HELI_REAR, male_h,
                                        pitch = CAM_HELI_PITCH,
                                        tolerance = CAM_HELI_TOL,
                                        tooth_height = CAM_HELI_TOOTH,
                                        tip_height = 1.2);
                    translate([0, 0, -0.1])
                        cylinder(h = male_h + 0.3, d = male_root - 0.3);
                    translate([0, 0, male_h - 1.8])
                        cylinder(h = proud + 1.8, d = CAM_HELI_OD);
                    translate([0, 0, male_h + proud * 0.55])
                        difference() {
                            cylinder(h = 0.8, d = CAM_HELI_OD + 1.2);
                            translate([0, 0, -0.1])
                                cylinder(h = 1.0, d = CAM_HELI_OD - 3);
                        }
                }
                translate([0, 0, -0.2])
                    cylinder(h = male_h + proud + 0.4, d = male_root - 4);
            }
}

// lift > 0 is the helicoid extended, camera on the far side of infinity.
module cam_heli_mount_at(mark, lift = 0) {
    ax = cam_axis(mark);
    translate([ax.x, ax.y, cam_heli_body_z()]) {
        if ($preview) {
            cam_helicoid_body(lift);
            // Bought metal F ring.
            color("DimGray")
                translate([0, 0, cam_heli_proud() + lift])
                    difference() {
                        cylinder(h = CAM_F_RING, d = F_STL_OD);
                        translate([0, 0, -0.1])
                            cylinder(h = CAM_F_RING + 0.2, d = TUBE_ID);
                    }
        }
    }
}

// -----------------------------------------------------------------------------
// stems — one cookie rebate. Helicoid nut is 9 mm deeper than the infinity
// seat, because the collapsed helicoid stays in the path.
// -----------------------------------------------------------------------------
// Shared rebate floor. The helicoid cookie's face is the collapsed flange.
// The infinity cookie's rim is the skin; its seat is HELI_SHORT above that
// flange, down inside the step.
function stem_drop() = patch_t() - heli_flange_z(EL180_HELI_MIN);

module stem_cookie() {
    translate([0, 0, -stem_drop()])
        port_flange("");
}

module stem_cookie_cuts(tag) {
    translate([0, 0, -stem_drop()]) {
        port_clamp_screws("") port_csk_cut();
        fxp_port_stamp(tag, "");
    }
}

// 45° on the inner −Y edge. That face sits on the bed so the cookie
// prints on-angle and the layers run through the plate.
module stem_bed_chamfer() {
    t = patch_t();
    translate([0, -stem_plate_w() / 2, 0])
        rotate([0, -90, 0])
            linear_extrude(stem_plate_w() + 2, center = true)
                polygon([[0, 0], [0, t], [t, 0]]);
}

module stem_thread_liner(z0, major = EL180_M62_MAJOR) {
    translate([0, 0, z0 - 0.2])
        cylinder(h = EL180_M62_LEN + 0.4, d = major + 8);
}

// Bought M62 helicoid. The female stays in the wall and stops on the inner
// face, so nothing printed crosses into the chamber and the tray can drop
// in from the top. Screw the helicoid in after the tray is in.
module part_stem(major = EL180_M62_MAJOR, tag = "stem", clock = 0) {
    od = HELI_NUT_OD;
    z_bot = -WALL;
    z_top = -WALL + EL180_M62_LEN;
    z_cookie = heli_flange_z(EL180_HELI_MIN) - patch_t();
    color("SlateGray")
    mm_split() {
        difference() {
            ScrewHole(major, EL180_M62_LEN,
                      pitch = EL180_M62_PITCH, tolerance = EL180_M62_TOL,
                      position = [0, 0, z_bot], rotation = [0, 0, clock])
                union() {
                    stem_cookie();
                    translate([0, 0, z_bot])
                        cylinder(h = z_top - z_bot, d = od, $fn = 128);
                }
            stem_cookie_cuts(fxp_tag(tag));
            translate([0, 0, -stem_drop()])
                stem_bed_chamfer();
            translate([0, 0, z_top - 0.05])
                cylinder(h = heli_flange_z(EL180_HELI_MIN) - z_top + 4,
                         d = heli_pass_d());
            translate([0, 0, z_bot])
                cylinder(h = 1.3, d = EL180_BARREL);
        }
        stem_thread_liner(z_bot, major);
    }
}

// Nikkor-W cookie. Outer face is the chassis skin. The only cut in that
// face is the clearance around the helicoid, from the end of the 8 mm
// thread out through the skin. The thread stops on the inner face.
module part_stem_w() {
    od = HELI_NUT_OD;
    z_bot = -WALL;
    z_top = z_bot + EL180_M62_LEN;
    color("SlateGray")
    mm_split() {
        difference() {
            ScrewHole(EL180_M62_MAJOR, EL180_M62_LEN,
                      pitch = EL180_M62_PITCH, tolerance = EL180_M62_TOL,
                      position = [0, 0, z_bot], rotation = [0, 0, STEM_W_CLOCK])
                union() {
                    port_flange("");
                    translate([0, 0, z_bot])
                        cylinder(h = patch_t() - z_bot, d = od, $fn = 128);
                }
            port_clamp_screws("") port_csk_cut();
            fxp_port_stamp(fxp_tag("stem_w"), "");
            stem_bed_chamfer();
            translate([0, 0, z_top - 0.05])
                cylinder(h = patch_t() - z_top + 2, d = heli_pass_d());
            translate([0, 0, z_bot])
                cylinder(h = 1.3, d = EL180_BARREL);
        }
        stem_thread_liner(z_bot);
    }
}

// Lens screws into the cookie. The rim is the chassis skin. Inside the Ø76
// the face steps down to the 158.5 seat. The M62 is the 8 mm under that
// seat and it stops at the inner face of the wall — the Ø60 barrel goes
// on through the chassis hole, so there is no printed tube in the chamber.
module part_stem_el180_inf() {
    od = el180_stem_od();
    seat = inf_seat_z();
    z_thread = seat - EL180_M62_LEN;
    color("SlateGray")
    mm_split() {
        difference() {
            ScrewHole(EL180_M62_MAJOR, EL180_M62_LEN,
                      pitch = EL180_M62_PITCH, tolerance = EL180_M62_TOL,
                      position = [0, 0, z_thread])
                union() {
                    port_flange("");
                    translate([0, 0, -stem_drop()])
                        linear_extrude(stem_drop())
                            port_plate_2d("");
                    translate([0, 0, z_thread])
                        cylinder(h = seat + 0.2 - z_thread, d = od);
                }
            // Step down to the flange. The rim outside this stays at the skin.
            translate([0, 0, seat])
                cylinder(h = patch_t() - seat + 2, d = EL180_LENS_OD + 0.6);
            port_clamp_screws("") {
                port_csk_cut();
                translate([0, 0, -stem_drop() - 0.2])
                    cylinder(h = stem_drop() + 0.4, d = PORT_SCREW_D);
            }
            // The step eats the rim, so the tag sits on the seat.
            translate([0, 0, seat - patch_t()])
                fxp_port_stamp(fxp_tag("stem_inf"), "");
        }
        stem_thread_liner(z_thread);
    }
}

// Nikkor-W nose. Screws into the same M62 helicoid as the EL-Nikkor.
// z = 0 seats on the helicoid's front face. The Copal flange stops on the
// far end, NW_FFD − EL_FFD ahead of that, so infinity is the helicoid's
// infinity mark. The lens drops in from the front. Its own M39 ring comes
// in through the bore from the rear.
NW_BOARD = 3.0;
// The ring clamps the thread, and that thread is what has to center the
// lens. Measured across it: 38.5. The old 41.8 hole (a Copal 1 barrel)
// left 1.6 mm of radial play. 39.2 is the slip fit — the hole prints
// small, and it still has to start over the crests.
NW_THREAD = 38.5;
NW_HOLE   = 39.2;
// A screw stands proud of the flange, 2–4 mm outside the thread, 1.05 tall.
// Full circle, so the shutter can sit at any angle. Deep enough that the
// screw does not hold the flange off the face.
NW_PIN_H   = 1.4;
NW_PIN_IN  = 1.6;
NW_PIN_OUT = 5.0;
NW_CLEAR = 56;      // Ø54 cell and the retaining ring
NW_NOSE_OD = 72;
function nw_flange_z() = flange_z(NW_FFD) - W_ARM_EXTRA;
// Helicoid front when it is at the infinity mark, threaded into the wall.
function nw_heli_z() = -WALL + heli_at_infinity();
function nw_rise() = nw_flange_z() - nw_heli_z();

module part_stem_nw180(major = EL180_M62_MAJOR, male = EL180_M62_LEN, tag = "nw180") {
    rise = nw_rise();
    echo(str(tag, "  rise ", rise, " mm from the helicoid face, male M",
              major, " × ", male, " mm. Adds 0 mm."));
    color("SteelBlue")
    difference() {
        union() {
            translate([0, 0, -male])
                ScrewThread(major, male, pitch = EL180_M62_PITCH,
                            tolerance = EL180_M62_TOL);
            cylinder(h = rise, d = NW_NOSE_OD, $fn = 128);
        }
        translate([0, 0, rise - NW_BOARD])
            cylinder(h = NW_BOARD + 1, d = NW_HOLE, $fn = 96);
        // Annulus in the flange face for the locating screw.
        translate([0, 0, rise - NW_PIN_H])
            difference() {
                cylinder(h = NW_PIN_H + 0.02,
                         d = NW_THREAD + 2 * NW_PIN_OUT, $fn = 96);
                translate([0, 0, -0.02])
                    cylinder(h = NW_PIN_H + 0.06,
                             d = NW_THREAD + 2 * NW_PIN_IN, $fn = 96);
            }
        translate([0, 0, -male - 0.2])
            cylinder(h = rise - NW_BOARD + male + 0.2,
                     d = NW_CLEAR, $fn = 96);
        translate([0, -NW_NOSE_OD / 2 - 0.02, rise / 2])
            rotate([-90, 0, 0])
                part_stamp_stack_cut(fxp_tag(tag), size = 2.0);
    }
}

// Printed stand-in for the bought M62 helicoid: a fixed spacer whose length
// is solved for infinity, so it has no travel at all. el180_spacer_add() is
// derived from the chassis, so it tracks any change to BOX_XY or the plate.
// Print a second at +0.5 mm if the first lands long; the shims only add.
function el180_adapter_h() = EL180_HELI_MALE + el180_spacer_add();

module part_el180_adapter(tone = "SlateGray") {
    hm = EL180_HELI_MALE;               // male into the stem boss
    hb = el180_spacer_add();            // what it adds past the boss face
    hf = EL180_M62_LEN;                 // female for the lens
    overlap = 3;
    hex_od = heli_pass_d() - 0.8;       // has to pass the recessed nut
    shank_d = EL180_M62_MAJOR - 1.6;
    hex_h = hb + overlap;
    color(tone)
    difference() {
        union() {
            ScrewThread(EL180_M62_MAJOR, hm, pitch = EL180_M62_PITCH,
                        tolerance = EL180_M62_TOL);
            cylinder(h = hm + overlap, d = shank_d);
            translate([0, 0, hm - overlap])
                ScrewHole(EL180_M62_MAJOR, hf, pitch = EL180_M62_PITCH,
                          tolerance = EL180_M62_TOL,
                          position = [0, 0, hex_h - hf])
                    cylinder(h = hex_h, d = hex_od, $fn = 128);
        }
        // Through-bore at the M62 minor; the hex behind the female stays
        // EL180_BARREL so the 60 mm lens barrel drops in.
        translate([0, 0, hm - overlap])
            cylinder(h = hex_h - hf + 0.4, d = EL180_BARREL);
        translate([0, 0, -0.2])
            cylinder(h = hm + hex_h + 0.4, d = EL180_BORE);
        translate([0, -hex_od / 2 - 0.05,
                   hm + hb * 0.5])
            rotate([90, 0, 0])
                part_stamp_stack_cut(fxp_tag("el180"), size = 2.2);
    }
    if ($preview && !SHOW_LENS && !nw_stem())
        color("DimGray", 0.45)
            translate([0, 0, hm + hb])
                el180_ghost();
}

// Stand-in for the machined flangeless ring. z = 0 is the shoulder that
// stops on the helicoid face. +z is the M62 female, 8 mm, which is how far
// the lens flange moves out. −z is 6 mm of M65 male. The Ø60 rear barrel
// passes back through that male into the helicoid.
module part_m65_ring() {
    male = M65_RING_MALE;
    add = M65_RING_ADD;
    echo(str("m65_ring adds ", add,
              " mm. Collapsed focus is about 4.5 m, not infinity.",
              " Face the male shorter if the shoulder does not seat."));
    color("SlateGray")
    difference() {
        union() {
            translate([0, 0, -male])
                ScrewThread(M65_MAJOR, male, pitch = EL180_M62_PITCH,
                            tolerance = EL180_M62_TOL);
            ScrewHole(EL180_M62_MAJOR, add, pitch = EL180_M62_PITCH,
                      tolerance = EL180_M62_TOL)
                cylinder(h = add, d = M65_RING_OD, $fn = 128);
        }
        translate([0, 0, -male - 0.2])
            cylinder(h = male + 0.2, d = EL180_BARREL, $fn = 96);
        translate([0, -M65_RING_OD / 2 - 0.02, add / 2])
            rotate([-90, 0, 0])
                part_stamp_stack_cut(fxp_tag("m65"), size = 2.2);
    }
}

module el180_ghost() {
    // Flange face on the stem face. +Z is the front of the lens, so the
    // Ø60 barrel runs back through the M62 into the boss.
    el180n(show_glass = SHOW_LENS_MARKS);
}

// Clamp on the external M62, ISCO on the collar, stand under the Ø90.
module isco_on_body() {
    seat = inf_stem()
        ? inf_seat_z()
        : -WALL + heli_at_infinity();
    lift = EXPLODED ? ex * 1.4 : 0;
    at_stem()
        translate([0, 0, seat + lift]) {
            color("DimGray", 0.92)
                el180n(show_glass = SHOW_LENS_MARKS);
            translate([0, 0, front_z - M62_LEN])
                isco_clamp("DarkOrange");
            translate([0, 0, front_z - M62_LEN + shoulder_z()])
                color("Goldenrod")
                    isco_ultrastar(show_glass = SHOW_LENS_MARKS);
        }
    saddle_y = -BOX_XY / 2
        - (seat + lift + front_z - M62_LEN + shoulder_z()
           + z_nose() + L_NOSE / 2);
    translate([50, saddle_y - 65, base_z()])
        rotate([0, 0, 90])
            isco_stand();
}

// -----------------------------------------------------------------------------
// lid
// -----------------------------------------------------------------------------
module lid_lining_mask() {
    s = BOX_XY;
    L = INNER_LINING;
    translate([0, 0, BOX_Z / 2 + lid_lift])
        translate([0, 0, (-40 + L) / 2])
            cube([s + 4, s + 4, 40 + L], center = true);
}

// Trigger board (KiCad x right, y down) to the lid: turned 180° so the jack
// edge faces +X, TRIG_EDGE_IN short of the lid edge, centred in Y.
function trig_xy(p) = [
    chassis_out() / 2 - TRIG_EDGE_IN - (p[0] - TRIG_EDGE[0]),
    p[1] - (TRIG_EDGE[1] + TRIG_EDGE[3]) / 2
];
function trig_holes() = concat(TRIG_ZERO_HOLES, TRIG_HAT_HOLES);

module trig_lid_holes() {
    for (p = trig_holes())
        translate(concat(trig_xy(p), [LID_T - TRIG_HOLE_DEEP]))
            cylinder(h = TRIG_HOLE_DEEP + 1, d = TRIG_PILOT_D, $fn = 24);
}

module trig_rib_keepout() {
    for (p = trig_holes())
        translate(trig_xy(p))
            cylinder(h = 10, d = 7, center = true);
}

// Ghost: Zero, board, jacks. z = 0 is the lid top.
module trigger_stack_ghost() {
    zero_z  = TRIG_STANDOFF;
    board_z = zero_z + 1.4 + 8.5;
    module outline(x0, y0, x1, y1)
        hull()
            for (p = [[x0, y0], [x1, y0], [x0, y1], [x1, y1]])
                translate(trig_xy(p)) square(0.01, center = true);
    for (p = trig_holes())
        color("Gold")
            translate(trig_xy(p))
                cylinder(h = p[1] > 50 ? board_z : zero_z, d = 4.5, $fn = 6);
    color("DarkGreen")
        translate([0, 0, zero_z])
            linear_extrude(1.4)
                outline(TRIG_ZERO_HOLES[0][0] - 3.5, TRIG_ZERO_HOLES[0][1] - 3.5,
                        TRIG_ZERO_HOLES[0][0] + 61.5, TRIG_ZERO_HOLES[0][1] + 26.5);
    color("Black")
        translate([0, 0, zero_z - 5.5])
            linear_extrude(5.5)
                let (cx = (TRIG_ZERO_HOLES[0][0] + TRIG_ZERO_HOLES[1][0]) / 2,
                     cy = TRIG_ZERO_HOLES[0][1])
                    outline(cx - 25.4, cy - 2.54, cx + 25.4, cy + 2.54);
    color("SeaGreen", 0.85)
        translate([0, 0, board_z])
            linear_extrude(1.6)
                outline(TRIG_EDGE[0], TRIG_EDGE[1], TRIG_EDGE[2], TRIG_EDGE[3]);
    for (j = TRIG_JACKS)
        color("DimGray")
            translate([0, 0, board_z + 1.6])
                linear_extrude(5)
                    outline(TRIG_EDGE[0], j[1] - 3, TRIG_EDGE[0] + 14, j[1] + 3);
}

module part_lid() {
    s   = BOX_XY;
    out = chassis_out();
    color("DarkSlateGray")
    mm_split() {
    difference() {
        translate([0, 0, BOX_Z / 2 + lid_lift]) {
            linear_extrude(LID_T)
                round_rect(out, out, PORT_BOSS_R);
            translate([0, 0, -LID_LIP / 2 + 0.01])
                lid_align_lip();
            lid_retain_tabs(lip = LID_LIP);
        }
        translate([0, 0, BOX_Z / 2 + lid_lift]) {
            for (p = lid_screws())
                translate([p[0], p[1], -LID_LIP - 1])
                    cylinder(h = LID_T + LID_LIP + 2, d = 3.2);
            trig_lid_holes();
            plate_stamp(fxp_tag("lid"), s, LID_T, STAMP_DEPTH, 5.0);
            difference() {
                lid_inner_ribs();
                lid_retain_keepout();
                trig_rib_keepout();
            }
        }
    }
        lid_lining_mask();
    }
}
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
