airdamien/FXPAN/openscad/hybrid_shift/WATCH_ME.scad

// =============================================================================
// hybrid_shift/WATCH_ME.scad  — pano L: shifted DX or FX, no tube toe
// =============================================================================
// Same stitch as hybrid. Rounded shell; three ports are C-channels
// (open at the lid, retained on three sides). The lid matches the
// shell and plugs the slot tops. Two M3s per port follow the tube
// (R/T shifted). No tube toe.
// SHELL inner = PETG lining, outer = PCTG.
// Lens −Y. Plate at origin: R → +X, T → +Y. Open this file.
// ARM_MOUNT 0 = female 52×0.75 + nut pocket; 1 = printed F-bayonet (clocked).
// F_MOUNT_CLOCK: add if the first F-print locks 90° off.
// STEM 0 = helicoid + L39 (EL-Nikkor 135). STEM 1 = female F (50 mm test).
// STEM 2 = M62 stem + bought M62 helicoid for EL-Nikkor 180/5.6N.
// STEM 3 = one-piece M62 stem, 180 seated at infinity (no helicoid, no adapter).
// F 50 uses the 54 mm camera tubes + 2 mm cookies (ARMS=1). 135/180 keep 72 / 4.
// Brace: triangle under the box + both body 1/4-20s. Tripod insert in the brace.
// F_STEM_CLOCK: add if the first F50 stem locks off the index.
// FX_MODE=1 (Customizer or ./export_hybrid_shift_fx.sh): D800 FX bores at
// sensor_shift ~11.5 mm, stitch ~59.0 mm (36% overlap). Ghost uses
// openscad/d800_body.stl (Thingiverse #4815092). Print FX tray, FX arms
// (truncated M52 mouth), and stem_el180_inf until the M62 helicoid
// lands. FX parts stamp FX + the part name (not hs_).
// =============================================================================

/* [Part] */
PART = "assembly"; // [assembly:Assembly, chassis:Chassis, stem:Stem 135, stem_f50:Stem F 50, stem_el180:Stem EL 180, stem_el180_inf:Stem EL 180 infinity, arm_r:Arm R 72 mm, arm_t:Arm T 72 mm, arm_r_s:Arm R F50, arm_t_s:Arm T F50, arm_r_sf:Arm R F50 printed F, arm_t_sf:Arm T F50 printed F, lid:Lid, display_mount:Display mount, hybrid_tray:Tray, brace:Tripod brace, shims:Shims, elnikkor_adapter:EL 135 adapter, el180_adapter:EL 180 adapter]
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
