airdamien/FXPAN/cam/test_dual.py

#!/usr/bin/env python3
"""Parse / pair tests — no camera required."""

from __future__ import annotations

import json
import shutil
import subprocess
import sys
import tempfile
import threading
import time
import unittest
from pathlib import Path
from unittest.mock import patch

sys.path.insert(0, str(Path(__file__).resolve().parent))
import brightness
import dual
import gpio
import link
import live
import pano
import settings
import wifi


DETECT = """\
Model                          Port
----------------------------------------------------------
Nikon DSC D7000                usb:020,007
Nikon DSC D7000                usb:020,012
"""

CURRENT = """\
Label: Serial Number
Readonly: 0
Type: TEXT
Current: 3000123
"""


class Parse(unittest.TestCase):
    def test_detect(self):
        rows = dual.parse_detect(DETECT)
        self.assertEqual(
            [(r["model"], r["port"]) for r in rows],
            [("Nikon DSC D7000", "usb:020,007"), ("Nikon DSC D7000", "usb:020,012")],
        )

    def test_detect_empty(self):
        self.assertEqual(dual.parse_detect("Model  Port\n----\n"), [])

    def test_current(self):
        self.assertEqual(dual.parse_current(CURRENT), "3000123")

    def test_currents(self):
        self.assertEqual(
            dual.parse_currents("Current: 400\nOther: x\nCurrent: 1/125\n"),
            ["400", "1/125"],
        )

    def test_format_shutter(self):
        self.assertEqual(dual.format_shutter("0.0250s"), "1/40")
        self.assertEqual(dual.format_shutter("1/125"), "1/125")
        self.assertEqual(dual.format_shutter("4s"), "4")
        self.assertEqual(dual.format_shutter("4"), "4")
        self.assertEqual(dual.format_shutter("Bulb"), "bulb")
        self.assertIsNone(dual.bulb_hold("8"))
        self.assertEqual(dual.bulb_hold("B8"), 8)
        self.assertEqual(dual.shutter_seconds("8"), 8)
        self.assertAlmostEqual(dual.shutter_seconds("1/125"), 0.008)
        self.assertEqual(dual.gpio_hold({"bulb": True, "shutter": "8"}), 8)
        self.assertIsNone(dual.gpio_hold({"bulb": False, "shutter": "8"}))
        self.assertEqual(dual.format_aperture("5.6"), "f/5.6")
        self.assertEqual(dual.format_aperture("f/8"), "f/8")
        self.assertEqual(dual.fstop_tries("5.6")[0], "f/5.6")

    def test_decode_program_d7000_dial(self):
        self.assertEqual(
            dual.decode_program({
                "500e": "32790",
                "scenemode": "Night landscape",
                "expprogram": "Night Landscape",
            }),
            "SCENE · Night landscape",
        )
        self.assertEqual(dual.decode_program({"500e": "1", "expprogram": "M"}), "M")
        self.assertEqual(dual.decode_program({"500e": "32792"}), "Auto (no flash)")

    def test_widget_currents_do_not_shift(self):
        raw = (
            "Label: ISO Speed\nCurrent: 400\nCurrent: extra\n"
            "Label: White Balance\nCurrent: Auto\n"
            "Label: Exposure Program\nCurrent: M\n"
            "Label: Shutter Speed\nCurrent: 1/125\n"
        )
        self.assertEqual(
            dual.parse_widget_currents(raw),
            ["extra", "Auto", "M", "1/125"],
        )
        self.assertNotEqual(dual.parse_currents(raw), dual.parse_widget_currents(raw))

    def test_auto_iso_assigns(self):
        import web
        self.assertEqual(
            web._assignments({"iso": "Auto"}),
            [("isoauto", "On"), ("autoiso", "On")],
        )
        self.assertEqual(
            web._assignments({"iso": "400", "shutter": "Auto"}),
            [("isoauto", "Off"), ("autoiso", "Off"), ("iso", "400")],
        )
        self.assertIn(("shutterspeed", "1/125"), web._assignments({"shutter": "1/125"}))
        self.assertIn(("shutterspeed", "bulb"), web._assignments({"shutter": "8", "bulb": True}))
        self.assertNotIn(("shutterspeed", "8"), web._assignments({"shutter": "8", "bulb": True}))
        self.assertEqual(
            web._assignments({"fstop": "5.6"}),
            [],
        )
        self.assertEqual(web._assignments({"fstop": "Auto"}), [])
        self.assertEqual(dual.iso_tries("400"), ["400", "ISO 400"])
        self.assertEqual(
            dual.shot_config([("isoauto", "Off"), ("iso", "400"), ("expprogram", "M")]),
            [("isoauto", "Off"), ("iso", "400")],
        )
        self.assertEqual(
            dual.shot_config([
                ("isoauto", "Off"), ("iso", "400"),
                ("exposurecompensation", "0.3"), ("whitebalance", "Auto"),
            ]),
            [
                ("isoauto", "Off"), ("iso", "400"),
                ("exposurecompensation", "0.3"), ("whitebalance", "Auto"),
            ],
        )
        self.assertEqual(dual.onoff_tries("Off"), ["Off", "0"])
        self.assertEqual(
            dual.config_args([("iso", "400"), ("shutterspeed", "1/125")])[-4:],
            ["--set-config", "iso=400", "--set-config", "shutterspeed=1/125"],
        )
        packed = dual.pack_assignments([
            ("isoauto", "Off"), ("autoiso", "Off"), ("iso", "ISO 400"),
            ("shutterspeed", "1/125"), ("whitebalance", "Auto"),
        ])
        self.assertEqual(
            packed,
            [
                ("isoauto", "Off"), ("iso", "400"),
                ("shutterspeed", "1/125"), ("whitebalance", "Auto"),
            ],
        )

    def test_set_one_single_command(self):
        calls = []

        def fake(args, port=None, timeout=120):
            calls.append((port, list(args)))
            return ""

        old = dual.gp
        dual.gp = fake
        self.addCleanup(lambda: setattr(dual, "gp", old))
        dual._set_one("usb:1", [
            ("isoauto", "Off"), ("autoiso", "Off"), ("iso", "400"),
            ("shutterspeed", "1/125"),
        ])
        self.assertEqual(len(calls), 1)
        joined = " ".join(calls[0][1])
        self.assertIn("isoauto=Off", joined)
        self.assertIn("iso=400", joined)
        self.assertIn("shutterspeed=1/125", joined)
        self.assertNotIn("autoiso", joined)

    def test_set_one_retries_exposure_after_batch_failure(self):
        calls = []

        def fake(args, port=None, timeout=120):
            calls.append(list(args))
            if len(calls) == 1:
                raise dual.CamError("could not set expprogram")
            return ""

        old = dual.gp
        dual.gp = fake
        self.addCleanup(lambda: setattr(dual, "gp", old))
        notes = dual._set_one("usb:1", [
            ("expprogram", "M"),
            ("isoauto", "Off"), ("autoiso", "Off"), ("iso", "400"),
            ("shutterspeed", "1/125"),
            ("whitebalance", "Auto"),
        ])
        self.assertEqual(len(calls), 2)
        retry = " ".join(calls[1])
        self.assertIn("iso=400", retry)
        self.assertIn("shutterspeed=1/125", retry)
        self.assertNotIn("expprogram", retry)
        self.assertNotIn("whitebalance", retry)
        self.assertTrue(any("expprogram" in n for n in notes))

    def test_set_one_keeps_exposure_when_isoauto_missing(self):
        calls = []

        def fake(args, port=None, timeout=120):
            calls.append(list(args))
            if any("isoauto=" in a for a in args):
                raise dual.CamError("isoauto not found")
            if any(a.startswith("expprogram=") for a in args):
                raise dual.CamError("could not set expprogram")
            return ""

        old = dual.gp
        dual._missing_widgets.clear()
        dual.gp = fake
        self.addCleanup(lambda: setattr(dual, "gp", old))
        self.addCleanup(dual._missing_widgets.clear)
        notes = dual._set_one("usb:1", [
            ("expprogram", "M"),
            ("isoauto", "Off"), ("iso", "400"),
            ("shutterspeed", "1/125"),
        ])
        sent = [" ".join(c) for c in calls]
        self.assertTrue(any("iso=400" in s and "shutterspeed=1/125" in s and "expprogram" not in s for s in sent))
        self.assertTrue(any("unsupported" in n for n in notes))

    def test_apply_locked_one_pack(self):
        calls = []

        def fake(args, port=None, timeout=120):
            calls.append(list(args))
            return ""

        old = dual.gp
        dual.gp = fake
        self.addCleanup(lambda: setattr(dual, "gp", old))
        dual.apply_locked("usb:1", [
            ("isoauto", "Off"), ("autoiso", "Off"), ("iso", "400"),
            ("shutterspeed", "1/125"), ("exposurecompensation", "0.3"),
        ])
        self.assertEqual(len(calls), 1)
        joined = " ".join(calls[0])
        self.assertLess(joined.index("isoauto=Off"), joined.index("iso=400"))
        self.assertIn("shutterspeed=1/125", joined)
        self.assertIn("exposurecompensation=0.3", joined)

    def test_status_stays_one_session_when_a_widget_is_missing(self):
        raw = (
            "Label: ISO Speed\nCurrent: 400\nEND\n"
            "Label: Auto ISO\nCurrent: Off\nEND\n"
            "Label: Shutter Speed\nCurrent: 1/250\nEND\n"
            "Label: Battery Level\nCurrent: 80%\nEND\n"
        )
        calls = []

        def fake(args, port=None, timeout=120):
            calls.append(list(args))
            return raw

        old = dual.gp
        dual.gp = fake
        self.addCleanup(lambda: setattr(dual, "gp", old))
        vals = dual._status_one({
            "port": "usb:1", "role": "T", "model": "Nikon DSC D800", "serial": "abc",
        })
        self.assertEqual(len(calls), 1)
        self.assertEqual(vals["iso"], "400")
        self.assertEqual(vals["autoiso"], "Off")
        self.assertEqual(vals["shutterspeed"], "1/250")
        self.assertEqual(vals["batterylevel"], "80%")
        self.assertFalse(vals.get("isoauto"))

    def test_set_drops_unknown_widget_in_one_retry(self):
        calls = []

        def fake(args, port=None, timeout=120):
            calls.append(list(args))
            if any(a.startswith("isoauto=") for a in args):
                raise dual.CamError("isoauto not found in configuration tree.")
            return ""

        old = dual.gp
        dual.gp = fake
        dual._missing_widgets.clear()
        self.addCleanup(lambda: setattr(dual, "gp", old))
        self.addCleanup(dual._missing_widgets.clear)
        notes = dual._set_one("usb:1", [
            ("isoauto", "Off"), ("iso", "400"), ("shutterspeed", "1/125"),
        ])
        self.assertEqual(len(calls), 2)
        self.assertNotIn("isoauto", " ".join(calls[1]))
        self.assertIn("iso=400", " ".join(calls[1]))
        self.assertIn("isoauto unsupported", notes)
        calls.clear()
        dual._set_one("usb:1", [
            ("isoauto", "Off"), ("iso", "400"), ("shutterspeed", "1/125"),
        ])
        self.assertEqual(len(calls), 1)
        self.assertNotIn("isoauto", " ".join(calls[0]))

    def test_capture_one_command(self):
        calls = []

        def fake(args, port=None, timeout=120):
            calls.append(list(args))
            return ""

        old = dual.gp
        dual.gp = fake
        self.addCleanup(lambda: setattr(dual, "gp", old))
        dual._gp_capture(
            "usb:1",
            ["--capture-image"],
            [("isoauto", "Off"), ("iso", "400"), ("shutterspeed", "1/125")],
            10,
        )
        self.assertEqual(len(calls), 1)
        joined = " ".join(calls[0])
        self.assertIn("viewfinder=0", joined)
        self.assertIn("iso=400", joined)
        self.assertIn("shutterspeed=1/125", joined)
        self.assertIn("--capture-image", joined)

    def test_claim_err(self):
        self.assertTrue(dual._claim_fail("Could not claim the USB device"))
        self.assertEqual(
            dual._gp_err("*** Error (-53: 'Could not claim the USB device') ***"),
            "USB busy (gvfs or ptpcamerad). Hit Detect again.",
        )

class SplitJpeg(unittest.TestCase):
    def test_two_frames_and_text(self):
        a = b"\xff\xd8AAAA\xff\xd9"
        b = b"\xff\xd8BBBB\xff\xd9"
        frames, rest = live.split_jpegs(b"Capturing...\n" + a + b[:6])
        self.assertEqual(frames, [a])
        frames2, rest2 = live.split_jpegs(rest + b[6:])
        self.assertEqual(frames2, [b])
        self.assertEqual(rest2, b"")

    def test_empty(self):
        self.assertEqual(live.split_jpegs(b"hello"), ([], b""))


class Pair(unittest.TestCase):
    def test_roundtrip(self):
        path = Path(self.id().replace(".", "_") + ".json")
        self.addCleanup(lambda: path.unlink(missing_ok=True))
        old = dual.PAIR_PATH
        dual.PAIR_PATH = path
        self.addCleanup(lambda: setattr(dual, "PAIR_PATH", old))
        dual.save_pair("111", "222")
        self.assertEqual(json.loads(path.read_text()), {"T": "111", "R": "222"})
        self.assertEqual(dual.load_pair(), {"T": "111", "R": "222"})
        dual.save_pair("111", None, replace=True)
        self.assertEqual(dual.load_pair(), {"T": "111"})
        dual.save_pair(None, "222")
        self.assertEqual(dual.load_pair(), {"T": "111", "R": "222"})
        with self.assertRaises(dual.CamError):
            dual.save_pair("111", "111", replace=True)
        dual.save_pair("111", "222", replace=True)
        self.assertEqual(dual.save_pair("222", None), {"T": "222"})
        dual.save_pair("111", "222", replace=True)
        self.assertEqual(dual.swap_pair(), {"T": "222", "R": "111"})
        self.assertEqual(dual.save_pair("", None), {"R": "111"})
        self.assertEqual(dual.swap_pair(), {"T": "111"})
        dual.save_pair("", "", replace=True)
        with self.assertRaises(dual.CamError):
            dual.swap_pair()


class Online(unittest.TestCase):
    def setUp(self):
        path = Path(self.id().replace(".", "_") + ".json")
        self.addCleanup(lambda: path.unlink(missing_ok=True))
        old = dual.PAIR_PATH
        dual.PAIR_PATH = path
        self.addCleanup(lambda: setattr(dual, "PAIR_PATH", old))

    def test_one_paired(self):
        have = dual.require_online(
            [{"role": "T", "port": "usb:1", "serial": "111", "model": "D7000"}]
        )
        self.assertEqual(list(have), ["T"])

    def test_lone_unpaired_is_t(self):
        have = dual.require_online(
            [{"role": "", "port": "usb:1", "serial": "999", "model": "D7000"}]
        )
        self.assertEqual(have["T"]["serial"], "999")

    def test_lone_unpaired_is_r_if_t_stored(self):
        dual.save_pair("111", None, replace=True)
        have = dual.require_online(
            [{"role": "", "port": "usb:1", "serial": "222", "model": "D7000"}]
        )
        self.assertEqual(list(have), ["R"])

    def test_none(self):
        with self.assertRaises(dual.CamError):
            dual.require_online([])


class LiveStart(unittest.TestCase):
    def test_start_without_cameras(self):
        old = dual.detect_bodies_cached
        dual.detect_bodies_cached = lambda timeout=120: []
        self.addCleanup(lambda: setattr(dual, "detect_bodies_cached", old))
        lv = live.Live()
        self.assertEqual(lv.start_from_usb(), {})
        self.assertFalse(lv.snapshot()["running"])

    def test_start_detect_error_is_empty(self):
        old = dual.detect_bodies_cached
        def boom(timeout=120):
            raise dual.CamError("gphoto2 timed out")
        dual.detect_bodies_cached = boom
        self.addCleanup(lambda: setattr(dual, "detect_bodies_cached", old))
        self.assertEqual(live.Live().start_from_usb(), {})

    def test_dead_roles_stale_no_frames(self):
        class Alive:
            def poll(self):
                return None

        lv = live.Live()
        lv._procs["T"] = Alive()
        lv._n["T"] = 0
        lv._born["T"] = time.time() - (live.FIRST_S + 1)
        lv._seen["T"] = 0
        self.assertEqual(lv.dead_roles(["T"]), ["T"])
        lv._n["T"] = 4
        lv._seen["T"] = time.time()
        self.assertEqual(lv.dead_roles(["T"]), [])

    def test_stop_drops_last_jpeg(self):
        class Dead:
            def poll(self):
                return 0
            def send_signal(self, _sig):
                pass
            def wait(self, timeout=None):
                return 0
            def kill(self):
                pass

        lv = live.Live()
        lv._procs["R"] = Dead()
        lv._frames["R"] = b"\xff\xd8R\xff\xd9"
        lv._n["R"] = 9
        lv.stop_roles(["R"])
        self.assertIsNone(lv.jpeg("R"))
        self.assertEqual(lv.running(), {})


class UsbBus(unittest.TestCase):
    def test_parse_lsusb(self):
        text = (
            "Bus 001 Device 003: ID 1d6b:0002 Linux Foundation\n"
            "Bus 020 Device 007: ID 04b0:0428 Nikon Corp.\n"
            "Bus 020 Device 012: ID 04b0:0428 Nikon Corp.\n"
        )
        self.assertEqual(
            dual.parse_lsusb(text),
            ["usb:020,007", "usb:020,012"],
        )

    def test_sysfs_ports(self):
        root = Path(tempfile.mkdtemp())
        self.addCleanup(lambda: shutil.rmtree(root, ignore_errors=True))
        a = root / "2-1"
        a.mkdir()
        (a / "idVendor").write_text("04b0\n")
        (a / "busnum").write_text("20\n")
        (a / "devnum").write_text("7\n")
        b = root / "2-2"
        b.mkdir()
        (b / "idVendor").write_text("1d6b\n")
        self.assertEqual(dual.nikon_usb_ports(root), ["usb:020,007"])
        (a / "speed").write_text("480\n")
        info = dual.nikon_usb_info(root)
        self.assertEqual(info["usb:020,007"]["speed"], "USB2 480 Mb/s")
        row = {"port": "usb:020,007", "model": "D800"}
        dual.attach_usb_speed([row], root)
        self.assertEqual(row["usb_speed"], "USB2 480 Mb/s")
        self.assertEqual(dual.format_usb_speed("5000"), "USB3 5 Gb/s")
        self.assertEqual(dual.format_usb_speed("10000"), "USB3.1 10 Gb/s")
        c = root / "2-1:1.0"
        c.mkdir()
        (c / "idVendor").write_text("04b0\n")
        (c / "busnum").write_text("20\n")
        (c / "devnum").write_text("7\n")
        self.assertEqual(dual.nikon_usb_ports(root), ["usb:020,007"])


class LinkKeep(unittest.TestCase):
    def test_absorb_and_missing(self):
        pair = Path(tempfile.mkdtemp()) / "pair.json"
        pair.write_text(json.dumps({"T": "111", "R": "222"}))
        old = dual.PAIR_PATH
        dual.PAIR_PATH = pair
        self.addCleanup(lambda: setattr(dual, "PAIR_PATH", old))
        ln = link.Link(live.Live())
        ln.absorb([
            {"role": "T", "serial": "111", "port": "usb:020,007", "model": "D7000"},
        ])
        snap = ln.snapshot()
        self.assertTrue(snap["roles"]["T"]["online"])
        self.assertFalse(snap["roles"]["R"]["online"])
        self.assertEqual(snap["missing"], ["R"])

    def test_usb_pauses_live_flag(self):
        ln = link.Link(live.Live())
        with ln.usb():
            self.assertGreater(ln._busy, 0)
        self.assertEqual(ln._busy, 0)

    def test_seat_open_role_is_r(self):
        path = Path(tempfile.mkdtemp()) / "pair.json"
        path.write_text(json.dumps({"T": "111"}))
        old = dual.PAIR_PATH
        dual.PAIR_PATH = path
        self.addCleanup(lambda: setattr(dual, "PAIR_PATH", old))
        rows = [
            {"role": "T", "serial": "111", "port": "usb:020,007"},
            {"role": "", "serial": "222", "port": "usb:020,012"},
        ]
        dual.seat_open_roles(rows, persist=True)
        self.assertEqual(rows[1]["role"], "R")
        self.assertEqual(dual.load_pair(), {"T": "111", "R": "222"})

    def test_absorb_keeps_unpaired_extra(self):
        pair = Path(tempfile.mkdtemp()) / "pair.json"
        pair.write_text(json.dumps({"T": "111", "R": "222"}))
        old = dual.PAIR_PATH
        dual.PAIR_PATH = pair
        self.addCleanup(lambda: setattr(dual, "PAIR_PATH", old))
        ln = link.Link(live.Live())
        ln.absorb([
            {"role": "T", "serial": "111", "port": "usb:020,007", "model": "D7000"},
            {"role": "", "serial": "999", "port": "usb:020,012", "model": "D7000"},
        ])
        snap = ln.snapshot()
        self.assertTrue(snap["roles"]["T"]["online"])
        self.assertEqual(len(snap["extras"]), 1)
        self.assertEqual(snap["extras"][0]["serial"], "999")

    def test_drop_gone_waits(self):
        ln = link.Link(live.Live())
        ln.absorb([
            {"role": "T", "serial": "111", "port": "usb:020,007", "model": "D7000"},
        ])
        keep = ln._drop_gone(["usb:020,099"])
        self.assertIn("T", keep)
        ln._gone_since["T"] = time.time() - 5
        keep = ln._drop_gone(["usb:020,099"])
        self.assertNotIn("T", keep)

    def test_orphan_ports_skips_owned(self):
        have = {"T": {"port": "usb:020,007"}}
        self.assertEqual(
            dual.orphan_ports(["usb:020,007", "usb:020,012"], have),
            ["usb:020,012"],
        )

    def test_retry_wait_backs_off(self):
        self.assertEqual(link.retry_wait(0), 3.0)
        self.assertEqual(link.retry_wait(1), 6.0)
        self.assertEqual(link.retry_wait(4), 30.0)

    def test_extra_port_does_not_stop_healthy_live(self):
        pair = Path(tempfile.mkdtemp()) / "pair.json"
        pair.write_text(json.dumps({"T": "111", "R": "222"}))
        old_pair = dual.PAIR_PATH
        dual.PAIR_PATH = pair
        self.addCleanup(lambda: setattr(dual, "PAIR_PATH", old_pair))

        class FakeLive:
            def __init__(self):
                self.stopped = 0
                self.ensured = []

            def stop(self):
                self.stopped += 1

            def stop_roles(self, roles):
                pass

            def snapshot(self):
                return {
                    "running": True,
                    "roles": {"T": {"alive": True, "frames": 12, "port": "usb:020,007"}},
                }

            def dead_roles(self, wanted):
                return []

            def ensure(self, have, only=None):
                self.ensured.append((dict(have), list(only or [])))

        fake = FakeLive()
        ln = link.Link(fake)
        ln.absorb([
            {"role": "T", "serial": "111", "port": "usb:020,007", "model": "D7000"},
        ])
        old_ports = dual.nikon_usb_ports
        old_probe = dual.probe_port
        dual.nikon_usb_ports = lambda root=None: ["usb:020,007", "usb:020,012"]
        dual.probe_port = lambda port, timeout=6: {
            "model": "D7000", "port": port, "serial": "222", "role": "R",
        }
        self.addCleanup(lambda: setattr(dual, "nikon_usb_ports", old_ports))
        self.addCleanup(lambda: setattr(dual, "probe_port", old_probe))
        ln._tend_live()
        self.assertEqual(fake.stopped, 0)
        self.assertEqual(ln.have()["R"]["port"], "usb:020,012")
        self.assertEqual(fake.ensured[-1][1], ["R"])

    def test_ensure_only_skips_healthy(self):
        class Alive:
            def poll(self):
                return None

        lv = live.Live()
        lv._procs["T"] = Alive()
        lv._ports["T"] = "usb:020,007"
        spawned = []
        lv._spawn = lambda role, port: spawned.append((role, port))
        lv.ensure(
            {
                "T": {"port": "usb:020,007"},
                "R": {"port": "usb:020,012"},
            },
            only=["R"],
        )
        self.assertEqual(spawned, [("R", "usb:020,012")])


class Gpio(unittest.TestCase):
    def setUp(self):
        self.sim = Path(tempfile.mkdtemp()) / "gpio.json"
        self._old_sim = gpio.SIM_PATH
        gpio.SIM_PATH = self.sim
        self.addCleanup(lambda: setattr(gpio, "SIM_PATH", self._old_sim))

    def test_this_host_is_not_a_pi(self):
        self.assertFalse(gpio.on_pi())
        self.assertFalse(gpio.snapshot()["available"])
        self.assertEqual(gpio.snapshot()["pin"], 21)
        with self.assertRaises(dual.CamError):
            gpio.fire()

    def test_sim_shows_and_dry_fires(self):
        self.assertFalse(gpio.snapshot()["available"])
        snap = gpio.set_sim(True)
        self.assertTrue(snap["sim"])
        self.assertTrue(snap["available"])
        self.assertFalse(snap["pi"])
        info = gpio.fire()
        self.assertEqual(info["backend"], "sim")
        gpio.set_sim(False)
        with self.assertRaises(dual.CamError):
            gpio.fire()

    def test_model_detects_pi(self):
        path = Path(tempfile.mkdtemp()) / "model"
        path.write_bytes(b"Raspberry Pi 5 Model B Rev 1.0\x00")
        self.addCleanup(lambda: path.unlink(missing_ok=True))
        self.assertTrue(gpio.on_pi(path))
        path.write_bytes(b"Apple Mac")
        self.assertFalse(gpio.on_pi(path))

    def test_find_chip_prefers_rp1(self):
        root = Path(tempfile.mkdtemp())
        self.addCleanup(lambda: shutil.rmtree(root, ignore_errors=True))
        (root / "gpiochip0").mkdir()
        (root / "gpiochip0" / "label").write_text("unused\n")
        (root / "gpiochip4").mkdir()
        (root / "gpiochip4" / "label").write_text("pinctrl-rp1\n")
        self.assertEqual(gpio.find_chip(root), "/dev/gpiochip4")

    def test_find_chip_unlabeled_pi5(self):
        root = Path(tempfile.mkdtemp())
        self.addCleanup(lambda: shutil.rmtree(root, ignore_errors=True))
        for name in ("gpiochip0", "gpiochip4", "gpiochip13"):
            (root / name).mkdir()
        self.assertEqual(gpio.find_chip(root), "/dev/gpiochip4")

    def test_fire_mock_drive(self):
        seen = []

        def sequence(focus_s, shutter_s):
            seen.append((focus_s, shutter_s))
            return "mock"

        info = gpio.fire(sequence=sequence)
        self.assertEqual(seen, [(0.1, 0.3)])
        self.assertEqual(info["pin"], 21)
        self.assertEqual(info["focus"], [20, 26])
        self.assertEqual(info["shutter"], [21, 19])
        self.assertEqual(info["ms"], 300)
        self.assertEqual(info["focus_ms"], 100)
        self.assertEqual(info["backend"], "mock")


LIST_FILES = """\
There are 2 files in folder '/store_00010001/DCIM/100D7000':
#1     DSC_0001.JPG               rd  4500 KB 4928x3264 image/jpeg
#2     DSC_0002.NEF               rd    20 MB 4928x3264 image/x-nikon-nef
There are 0 files in folder '/store_00010001/DCIM':
"""


class CardPull(unittest.TestCase):
    def test_parse_list_files(self):
        rows = dual.parse_list_files(LIST_FILES)
        self.assertEqual(
            [(r["n"], r["name"]) for r in rows],
            [(1, "DSC_0001.JPG"), (2, "DSC_0002.NEF")],
        )
        later = dual.parse_list_files(
            "There are 2 files in folder '/a':\n"
            "#10    OLD.JPG               rd  1 KB\n"
            "#11    NEW.JPG               rd  2 KB\n"
        )
        self.assertEqual([(r["n"], r["name"]) for r in later], [(1, "OLD.JPG"), (2, "NEW.JPG")])
        self.assertEqual(rows[0]["folder"], "/store_00010001/DCIM/100D7000")

    def test_wait_new_images(self):
        calls = {"n": 0}
        before = [{"folder": "/dcim", "name": "A.JPG", "n": 1}]

        def fake(_port):
            calls["n"] += 1
            if calls["n"] < 3:
                raise dual.CamError("busy")
            return before + [{"folder": "/dcim", "name": "B.JPG", "n": 2}]

        new = dual.wait_new_images(
            "usb:1", before, timeout=2, interval=0.01, list_fn=fake, settle=0
        )
        self.assertEqual(new[0]["name"], "B.JPG")

    def test_wait_timeout(self):
        before = [{"folder": "/dcim", "name": "A.JPG", "n": 1}]
        with self.assertRaises(dual.CamError):
            dual.wait_new_images(
                "usb:1", before, timeout=0.05, interval=0.01,
                list_fn=lambda _p: before,
            )

    def test_gpio_window_frees_usb(self):
        ln = link.Link(live.Live())
        calls = []

        def mark_free():
            calls.append("free")

        with patch.object(dual, "free_usb", mark_free):
            with ln.gpio_window(settle=0):
                calls.append("inside")
        self.assertEqual(calls, ["free", "inside"])

    def test_wait_picks_up_nef_companion(self):
        before = [{"folder": "/dcim", "name": "A.JPG", "n": 1}]
        calls = {"n": 0}

        def fake(_port):
            calls["n"] += 1
            if calls["n"] == 1:
                return before + [{"folder": "/dcim", "name": "B.JPG", "n": 2}]
            return before + [
                {"folder": "/dcim", "name": "B.JPG", "n": 2},
                {"folder": "/dcim", "name": "B.NEF", "n": 3},
            ]

        new = dual.wait_new_images(
            "usb:1", before, timeout=2, interval=0.01, list_fn=fake, settle=0.05
        )
        names = {row["name"] for row in new}
        self.assertEqual(names, {"B.JPG", "B.NEF"})

    def _fake_ram(self, files):
        seen = []

        def fake(args, port=None, timeout=120):
            seen.append(list(args))
            name = next(a for a in args if a.startswith("--filename=")).split("=", 1)[1]
            for i, ext in enumerate(files.pop(0) if files else [], 1):
                Path(name.replace("%n", str(i)).replace("%C", ext)).write_bytes(b"x")
            return ""

        return fake, seen

    def test_pull_ram_names_like_card_pull(self):
        dest = Path(tempfile.mkdtemp())
        self.addCleanup(shutil.rmtree, dest)
        fake, seen = self._fake_ram([["jpg", "nef"]])
        with patch.object(dual, "gp", fake):
            saved = dual.pull_ram_one("T", "usb:1", dest, "20260928_170000")
        self.assertEqual(sorted(saved), ["T_20260928_170000.jpg", "T_20260928_170000.nef"])
        self.assertIn("--wait-event-and-download=FILEADDED", seen[0])

    def test_pull_ram_camera_jpeg_beats_extracted_preview(self):
        dest = Path(tempfile.mkdtemp())
        self.addCleanup(shutil.rmtree, dest)
        (dest / "T_20260928_170000.jpg").write_bytes(b"preview")
        fake, _ = self._fake_ram([["nef", "jpg"]])
        with patch.object(dual, "gp", fake):
            saved = dual.pull_ram_one("T", "usb:1", dest, "20260928_170000")
        self.assertEqual(saved[0], "T_20260928_170000.jpg")
        self.assertEqual((dest / "T_20260928_170000.jpg").read_bytes(), b"x")
        self.assertEqual(list(dest.glob("*_ram*")), [])

    def test_pull_ram_nothing_fired(self):
        dest = Path(tempfile.mkdtemp())
        self.addCleanup(shutil.rmtree, dest)

        def fake(args, port=None, timeout=120):
            raise dual.CamError("gphoto2 timed out")

        with patch.object(dual, "gp", fake):
            with self.assertRaisesRegex(dual.CamError, "did not fire"):
                dual.pull_ram_one("R", "usb:1", dest, "20260928_170000")

    def test_arm_ram_spills_backlog_then_stops(self):
        dest = Path(tempfile.mkdtemp())
        self.addCleanup(shutil.rmtree, dest)
        fake, seen = self._fake_ram([["jpg", "jpg"], []])
        with patch.object(dual, "gp", fake):
            kept = dual.arm_ram_one("R", "usb:1", dest, "20260928_170000")
        self.assertEqual(len(seen), 2)
        self.assertIn("recordingmedia=1", seen[0])
        self.assertNotIn("recordingmedia=1", seen[1])
        self.assertTrue(kept)
        self.assertEqual(list(dest.glob("R_*")), [])


class Pano(unittest.TestCase):
    def setUp(self):
        self.root = Path(tempfile.mkdtemp())
        self.addCleanup(lambda: shutil.rmtree(self.root, ignore_errors=True))

    def _jpeg(self, name, color, w=40, h=20):
        dest = self.root / name
        subprocess.run(
            ["magick", "-size", f"{w}x{h}", f"xc:{color}", str(dest)],
            check=True,
            capture_output=True,
        )
        return dest

    def _exif_jpeg(self, name, iso=400, shutter=(1, 125), program=1, wb=0):
        dest = self._jpeg(name, "red")
        model = b"NIKON D7000\x00"
        pu16 = lambda n: n.to_bytes(2, "little")
        pu32 = lambda n: n.to_bytes(4, "little")
        def entry(tag, typ, cnt, val4):
            return pu16(tag) + pu16(typ) + pu32(cnt) + val4
        ifd0_off, ifd0_len = 8, 2 + 24 + 4
        model_off = ifd0_off + ifd0_len
        exif_off = model_off + len(model)
        exif_len = 2 + 48 + 4
        rat_off = exif_off + exif_len
        tiff = (
            b"II*\x00" + pu32(8)
            + pu16(2)
            + entry(0x0110, 2, len(model), pu32(model_off))
            + entry(0x8769, 4, 1, pu32(exif_off))
            + pu32(0)
            + model
            + pu16(4)
            + entry(0x829A, 5, 1, pu32(rat_off))
            + entry(0x8827, 3, 1, pu16(iso) + b"\x00\x00")
            + entry(0x8822, 3, 1, pu16(program) + b"\x00\x00")
            + entry(0xA403, 3, 1, pu16(wb) + b"\x00\x00")
            + pu32(0)
            + pu32(shutter[0]) + pu32(shutter[1])
        )
        app1 = b"Exif\x00\x00" + tiff
        jpeg = dest.read_bytes()
        dest.write_bytes(b"\xff\xd8" + b"\xff\xe1" + (len(app1) + 2).to_bytes(2, "big") + app1 + jpeg[2:])
        return dest

    def test_read_exif(self):
        self.assertEqual(pano.read_exif(self._jpeg("plain.jpg", "red")), {})
        info = pano.read_exif(self._exif_jpeg("shot.jpg"))
        self.assertEqual(info["iso"], "400")
        self.assertEqual(info["shutter"], "1/125")
        self.assertEqual(info["program"], "M")
        self.assertEqual(info["wb"], "Auto")
        self.assertEqual(info["model"], "D7000")

    def test_list_pairs_stores_exif(self):
        self._exif_jpeg("T_20260101_120000.jpg", iso=640, shutter=(1, 60))
        self._exif_jpeg("R_20260101_120000.jpg", iso=100, shutter=(1, 125), program=3)
        rows = pano.list_pairs(self.root)
        ready = [row for row in rows if row["ready"]][0]
        self.assertEqual(ready["exif"]["T"]["iso"], "640")
        self.assertEqual(ready["exif"]["T"]["shutter"], "1/60")
        self.assertEqual(ready["exif"]["R"]["program"], "A")
        self.assertTrue((self.root / "X_20260101_120000.json").is_file())
        pano.delete_stamp("20260101_120000", self.root)
        self.assertFalse((self.root / "X_20260101_120000.json").is_file())

    def test_list_pairs(self):
        self._jpeg("T_20260101_120000.jpg", "red")
        self._jpeg("R_20260101_120000.jpg", "blue")
        self._jpeg("T_lonely.jpg", "red")
        rows = pano.list_pairs(self.root)
        ready = [row for row in rows if row["ready"]]
        self.assertEqual(len(ready), 1)
        self.assertEqual(ready[0]["stamp"], "20260101_120000")
        self.assertEqual(ready[0]["t"], "T_20260101_120000.jpg")

    def test_list_pairs_nef_and_extract(self):
        jpeg = self._jpeg("preview.jpg", "red")
        (self.root / "T_20260101_120000.nef").write_bytes(b"NEF" + jpeg.read_bytes() + b"\x00")
        (self.root / "R_20260101_120000.nef").write_bytes(b"NEF" + jpeg.read_bytes() + b"\x00")
        rows = pano.list_pairs(self.root)
        self.assertEqual(len(rows), 1)
        self.assertTrue(rows[0]["ready"])
        self.assertEqual(rows[0]["t_nef"], "T_20260101_120000.nef")
        self.assertEqual(rows[0]["r_nef"], "R_20260101_120000.nef")
        t_path, r_path = pano.find_pair("20260101_120000", self.root)
        self.assertEqual(t_path.suffix.lower(), ".jpg")
        self.assertTrue(t_path.is_file())
        self.assertTrue(r_path.is_file())
        self.assertTrue((self.root / "T_20260101_120000.nef").is_file())
        got = pano.list_pairs(self.root)[0]
        self.assertEqual(got["t"], "T_20260101_120000.jpg")
        self.assertEqual(got["t_nef"], "T_20260101_120000.nef")

    def test_desqueeze_writes_ana(self):
        src = self._jpeg("P_20260101_120000.jpg", "green", w=40, h=20)
        dest = self.root / "P_20260101_120000_ana.jpg"
        pano.desqueeze_jpeg(src, dest, 2.0)
        self.assertEqual(pano._size(dest), (80, 20))
        rows = pano.list_pairs(self.root)
        self.assertEqual(rows[0]["pano"], "P_20260101_120000.jpg")
        self.assertEqual(rows[0]["pano_ana"], "P_20260101_120000_ana.jpg")

    def test_delete_stamp_removes_nef_and_ana(self):
        self._jpeg("T_20260101_120000.jpg", "red")
        self._jpeg("R_20260101_120000.jpg", "blue")
        (self.root / "T_20260101_120000.nef").write_bytes(b"NEF")
        self._jpeg("P_20260101_120000.jpg", "green")
        self._jpeg("P_20260101_120000_ana.jpg", "green", w=80, h=20)
        pano.delete_stamp("20260101_120000", self.root, sides=["P"])
        self.assertFalse((self.root / "P_20260101_120000.jpg").is_file())
        self.assertFalse((self.root / "P_20260101_120000_ana.jpg").is_file())
        self.assertTrue((self.root / "T_20260101_120000.nef").is_file())
        pano.delete_stamp("20260101_120000", self.root)
        self.assertEqual(pano.list_pairs(self.root), [])
        self.assertFalse((self.root / "T_20260101_120000.nef").is_file())

    def test_stitch_status_stays_on_pair(self):
        self._jpeg("T_20260101_120000.jpg", "red")
        self._jpeg("R_20260101_120000.jpg", "blue")
        pano._write_sidecar(
            self.root, "20260101_120000",
            {"mode": "open", "phase": "error", "error": "SIFT failed", "message": "SIFT failed"},
        )
        row = pano.list_pairs(self.root)[0]
        self.assertEqual(row["stitch"]["phase"], "error")
        self.assertEqual(row["stitch"]["error"], "SIFT failed")
        pano._write_sidecar(
            self.root, "20260101_120000",
            {"mode": "open", "phase": "done", "error": "", "message": "open  affine  70×20"},
        )
        row = pano.list_pairs(self.root)[0]
        self.assertEqual(row["stitch"]["phase"], "done")
        self.assertEqual(row["stitch"]["message"], "open  affine  70×20")

    def test_list_pairs_newest_first(self):
        self._jpeg("T_20260101_120000.jpg", "red")
        self._jpeg("R_20260101_120000.jpg", "blue")
        self._jpeg("T_20260913_150000.jpg", "red")
        self._jpeg("R_20260913_150000.jpg", "blue")
        stamps = [row["stamp"] for row in pano.list_pairs(self.root)]
        self.assertEqual(stamps[0], "20260913_150000")
        self.assertEqual(stamps[1], "20260101_120000")

    def test_size_identify_with_limits(self):
        path = self.root / "T_20260101_120000.jpg"
        self._jpeg(path.name, "red")
        self.assertEqual(pano._size(path), (40, 20))

    def test_thumb_keeps_pano_aspect(self):
        wide = self._jpeg("P_20260101_120000.jpg", "green", w=160, h=40)
        dest = pano.thumb(wide.name, 80, self.root)
        self.assertEqual(pano._size(dest), (80, 20))

    def test_thumb_serves_file_while_stitching(self):
        src = self._jpeg("R_20260101_120000.jpg", "blue", w=80, h=40)
        pano._jobs["x"] = {"running": True, "phase": "work", "stamp": "x"}
        try:
            got = pano.thumb(src.name, 40, self.root)
            self.assertEqual(got, src.resolve())
            self.assertFalse((self.root / ".thumbs" / f"40_{src.name}").exists())
        finally:
            pano._jobs.clear()

    def test_thumb_reuses_cache_while_stitching(self):
        src = self._jpeg("R_20260101_120000.jpg", "blue", w=80, h=40)
        ready = pano.thumb(src.name, 60, self.root)
        pano._jobs["x"] = {"running": True, "phase": "work", "stamp": "x"}
        try:
            self.assertEqual(pano.thumb(src.name, 40, self.root), ready)
            self.assertFalse((self.root / ".thumbs" / f"40_{src.name}").exists())
        finally:
            pano._jobs.clear()

    def test_hugin_profile_fxpan(self):
        prof = pano.hugin_profile(7360, 4912)
        self.assertTrue(prof["flip_r"])
        self.assertAlmostEqual(prof["overlap"], 0.22)
        self.assertEqual(prof["dy"], 0)
        self.assertEqual(prof["profile"], "fxpan65")
        d7 = pano.hugin_profile(4928, 3264)
        self.assertAlmostEqual(d7["overlap"], 0.20)
        self.assertEqual(d7["dy"], 0)

    def test_similarity_sane(self):
        M = [[1.0, 0.0, 5800.0], [0.0, 1.0, -20.0]]
        self.assertTrue(pano._similarity_sane(M, 7360, 4912))
        bad = [[1.4, 0.0, 5800.0], [0.0, 1.4, 0.0]]
        self.assertFalse(pano._similarity_sane(bad, 7360, 4912))

    def test_overlap_strip_rows(self):
        self.assertEqual(pano._overlap_strip_rows(40, 0, 0), (0, 0, 40))
        self.assertEqual(pano._overlap_strip_rows(40, 0, 2), (0, 2, 38))
        self.assertEqual(pano._overlap_strip_rows(40, 2, 0), (2, 0, 38))
        self.assertEqual(pano._overlap_canvas_y(0, 2), 2)
        self.assertEqual(pano._overlap_canvas_y(2, 0), 2)

    def test_inner_crop_box_drops_step(self):
        try:
            import numpy as np
        except ImportError:
            self.skipTest("numpy not installed")
        r = np.zeros((40, 80, 4), np.uint8)
        t = np.zeros((40, 80, 4), np.uint8)
        r[0:30, 0:50, 3] = 255
        t[10:40, 30:80, 3] = 255
        box = pano._inner_crop_box(r, t)
        self.assertEqual(box, (0, 10, 80, 30))

    def test_crop_overlap_strips_dy(self):
        t = self._jpeg("T_20260101_120000.jpg", "red", w=80, h=40)
        r = self._jpeg("R_20260101_120000.jpg", "blue", w=80, h=40)
        ol, x, out_w, out_h, ty, ry = pano._compose_geometry(80, 40, 0.25, 2)
        tmp = self.root / "strips"
        tmp.mkdir()
        strip_h = pano._crop_overlap_strips(
            r, t, tmp / "rol.png", tmp / "tol.png", 80, 40, ol, x, ty, ry,
        )
        self.assertEqual(strip_h, 38)
        self.assertEqual(pano._size(tmp / "rol.png"), (ol, 38))
        self.assertEqual(pano._size(tmp / "tol.png"), (ol, 38))

    def test_stitch_hugin(self):
        if not pano.hugin_available():
            self.skipTest("hugin not installed")
        self._jpeg("T_20260101_120000.jpg", "red", w=80, h=40)
        self._jpeg("R_20260101_120000.jpg", "blue", w=80, h=40)
        info = pano.stitch_stamp(
            "20260101_120000", overlap=0.25, flip_r=True, mode="hugin", root=self.root
        )
        self.assertEqual(info["mode"], "hugin")
        self.assertIn(info["engine"], ("feather", "multiband", "enblend", "merge"))
        self.assertGreater(info["width"], 70)
        self.assertTrue((self.root / "P_20260101_120000.jpg").is_file())
        self.assertRegex(info["message"], r"\d+\.\d+s")
        self.assertGreaterEqual(info["sec"], 0)

    def test_multiband_write_covers_both(self):
        pano._venv_site()
        try:
            import cv2
            import numpy as np
        except ImportError:
            self.skipTest("cv2 not installed")
        r = np.zeros((40, 80, 4), np.uint8)
        t = np.zeros((40, 80, 4), np.uint8)
        r[:, :50] = (255, 0, 0, 255)
        t[:, 30:] = (0, 255, 0, 255)
        dest = self.root / "blend.jpg"
        w, h = pano._multiband_write(r, t, dest)
        self.assertEqual((w, h), (80, 40))
        img = cv2.imread(str(dest), cv2.IMREAD_COLOR)
        self.assertIsNotNone(img)
        self.assertGreater(int(img[20, 5, 0]), 180)
        self.assertGreater(int(img[20, 75, 1]), 180)

    def test_overlap_blend_masks_overlap(self):
        pano._venv_site()
        try:
            import numpy as np
        except ImportError:
            self.skipTest("numpy not installed")
        r_a = np.zeros((40, 80), np.uint8)
        t_a = np.zeros((40, 80), np.uint8)
        r_a[:, :50] = 255
        t_a[:, 30:] = 255
        rm, tm = pano._overlap_blend_masks(r_a, t_a, dilate=8)
        self.assertGreater(int(((rm > 0) & (tm > 0)).sum()), 0)
        self.assertGreater(int(rm[:, 5].mean()), 200)
        self.assertGreater(int(tm[:, 75].mean()), 200)

    def test_stitch_hugin_multiband(self):
        pano._venv_site()
        try:
            import cv2
            import numpy as np
        except ImportError:
            self.skipTest("cv2 not installed")
        rng = np.random.default_rng(2)
        full = rng.integers(32, 224, (240, 900, 3), dtype=np.uint8)
        cv2.imwrite(
            str(self.root / "R_20260101_120000.jpg"),
            cv2.flip(full[:, :500], 1),
        )
        cv2.imwrite(str(self.root / "T_20260101_120000.jpg"), full[:, 400:])
        info = pano.stitch_stamp(
            "20260101_120000", overlap=0.20, flip_r=True, mode="hugin",
            root=self.root, balance=False,
        )
        self.assertEqual(info["mode"], "hugin")
        self.assertEqual(info["engine"], "multiband")
        self.assertGreater(info["width"], 700)
        self.assertRegex(info["message"], r"\d+\.\d+s")
        self.assertTrue((self.root / "P_20260101_120000.jpg").is_file())

    def test_stitch_raw_runs_16bit_multiband(self):
        pano._venv_site()
        try:
            import cv2
            import numpy as np
        except ImportError:
            self.skipTest("cv2 not installed")
        rng = np.random.default_rng(3)
        full = rng.integers(32, 224, (240, 900, 3), dtype=np.uint8)
        r8, t8 = cv2.flip(full[:, :500], 1), full[:, 400:]
        cv2.imwrite(str(self.root / "R_20260101_120000.jpg"), r8)
        cv2.imwrite(str(self.root / "T_20260101_120000.jpg"), t8)
        (self.root / "R_20260101_120000.nef").write_bytes(b"NEF")
        (self.root / "T_20260101_120000.nef").write_bytes(b"NEF")
        def lin(img8):
            return ((img8.astype(np.float32) / 255.0) ** 2.2 * 65535).astype(np.uint16)

        seen = {}

        def fake_develop(t_nef, r_nef, size=None, on_log=None, t_jpeg=None, look=True):
            seen["size"] = size
            seen["t_jpeg"] = Path(t_jpeg).name
            seen["look"] = look
            return {"t": lin(t8), "r": lin(r8), "gain": 1.0}

        with patch.object(pano, "develop_pair", fake_develop):
            info = pano.stitch_stamp(
                "20260101_120000", overlap=0.20, flip_r=True, mode="open",
                root=self.root, balance=False, raw=True, look=False,
            )
        self.assertEqual(seen["size"], (500, 240))
        self.assertEqual(seen["t_jpeg"], "T_20260101_120000.jpg")
        self.assertFalse(seen["look"])
        self.assertEqual(info["engine"], "multiband")
        self.assertEqual(info.get("source"), "raw")
        self.assertIn("raw 16-bit neutral", info["message"])
        out = cv2.imread(str(self.root / "P_20260101_120000.jpg"))
        self.assertGreater(float(out.mean()), 60)
        master = self.root / "P_20260101_120000_master.tif"
        self.assertEqual(info.get("master"), master.name)
        tif = cv2.imread(str(master), cv2.IMREAD_UNCHANGED)
        self.assertEqual(tif.dtype, np.uint16)
        self.assertEqual(tif.shape[:2], out.shape[:2])
        rows = pano.list_pairs(self.root)
        self.assertEqual(rows[0]["master"], master.name)
        pano.delete_stamp("20260101_120000", sides=["P"], root=self.root)
        self.assertFalse(master.exists())

    def test_master_tiff_keeps_every_14bit_level(self):
        pano._venv_site()
        try:
            import cv2
            import numpy as np
        except ImportError:
            self.skipTest("cv2 not installed")
        levels = np.arange(0, 65536, 4, dtype=np.uint16)
        lin = np.repeat(levels.reshape(128, 128, 1), 3, axis=2)
        path = pano.write_master_tiff(self.root / "m.tif", lin)
        back = cv2.imread(str(path), cv2.IMREAD_UNCHANGED)
        self.assertEqual(back.dtype, np.uint16)
        self.assertEqual(len(np.unique(back[:, :, 0])), len(levels))
        self.assertGreaterEqual(int(back.max()), 65530)

    def test_balance_linear_never_scales_up(self):
        pano._venv_site()
        try:
            import numpy as np
        except ImportError:
            self.skipTest("numpy not installed")
        t = np.full((10, 100, 3), 40000, np.uint16)
        r = np.full((10, 100, 3), 30000, np.uint16)
        t2, r2, msg = pano._balance_linear(t, r, 0.2)
        self.assertIn("T ×", msg)
        self.assertEqual(int(r2.max()), 30000)
        self.assertLessEqual(int(t2.max()), 30001)
        t3, r3, msg = pano._balance_linear(r, t, 0.2)
        self.assertIn("R ×", msg)
        self.assertEqual(int(t3.max()), 30000)

    def test_nikon_look_adds_contrast_and_colour(self):
        pano._venv_site()
        try:
            import numpy as np
        except ImportError:
            self.skipTest("numpy not installed")
        grey = np.array([[[0.2, 0.2, 0.2], [0.8, 0.8, 0.8]]], np.float32)
        out = pano._nikon_look(grey)
        self.assertLess(float(out[0, 0, 0]), 0.2)
        self.assertGreater(float(out[0, 1, 0]), 0.8)
        self.assertAlmostEqual(float(out[0, 0, 0]), float(out[0, 0, 2]), places=5)
        tint = np.array([[[0.3, 0.4, 0.6]]], np.float32)
        spread = lambda a: float(a.max() - a.min())
        self.assertGreater(spread(pano._nikon_look(tint)), spread(tint))

    def test_multiband_16bit_white_edge_does_not_wrap(self):
        pano._venv_site()
        try:
            import cv2
            import numpy as np
        except ImportError:
            self.skipTest("cv2 not installed")
        h, w = 64, 200
        img = np.full((h, w, 3), 65000, np.uint16)
        img[:, 96:104] = 0
        r = np.zeros((h, w, 4), np.uint16)
        t = np.zeros((h, w, 4), np.uint16)
        r[:, :130, :3], r[:, :130, 3] = img[:, :130], 65535
        t[:, 70:, :3], t[:, 70:, 3] = img[:, 70:], 65535
        dest = self.root / "wrap.jpg"
        pano._multiband_write(r, t, dest)
        out = cv2.imread(str(dest))
        outside = np.concatenate([out[:, :88], out[:, 112:]], axis=1)
        self.assertGreater(int(outside.min()), 180)

    def test_raw_tone_rolls_off_to_white(self):
        pano._venv_site()
        try:
            import numpy as np
        except ImportError:
            self.skipTest("numpy not installed")
        x = np.linspace(0, 1, 101, dtype=np.float32)
        y = pano._raw_tone(x, 4.0)
        self.assertAlmostEqual(float(y[-1]), 1.0, places=4)
        self.assertTrue(bool(np.all(np.diff(y) > 0)))
        self.assertLess(float(y[50]), 1.0)

    def test_raw_gain_matches_camera_jpeg(self):
        pano._venv_site()
        try:
            import cv2
            import numpy as np
        except ImportError:
            self.skipTest("cv2 not installed")
        ref = self.root / "ref.jpg"
        cv2.imwrite(str(ref), np.full((64, 64), 118, np.uint8))
        lin = np.full((64, 64, 3), int(0.05 * 65535), np.uint16)
        px = np.full((1, 1, 3), 0.05, np.float32)
        for look in (True, False):
            gain = pano._raw_gain(lin, ref, look)
            got = float(pano._raw_display(px, gain, look).mean())
            self.assertAlmostEqual(got, 118 / 255, delta=0.02)
        self.assertEqual(pano._raw_gain(lin, None), 1.0)

    def test_stitch_raw_sift_miss_stays_16bit(self):
        pano._venv_site()
        try:
            import cv2
            import numpy as np
        except ImportError:
            self.skipTest("cv2 not installed")
        flat = np.full((240, 500, 3), 90, np.uint8)
        cv2.imwrite(str(self.root / "R_20260101_120000.jpg"), flat)
        cv2.imwrite(str(self.root / "T_20260101_120000.jpg"), flat)
        (self.root / "R_20260101_120000.nef").write_bytes(b"NEF")
        (self.root / "T_20260101_120000.nef").write_bytes(b"NEF")
        deep = np.full((240, 500, 3), 90 * 257, np.uint16)
        with patch.object(pano, "develop_pair",
                          lambda *a, **k: {"t": deep, "r": deep.copy(), "gain": 1.0}):
            info = pano.stitch_stamp(
                "20260101_120000", overlap=0.20, flip_r=True, mode="hugin",
                root=self.root, balance=False, raw=True,
            )
        self.assertEqual(info["engine"], "multiband")
        self.assertEqual(info.get("source"), "raw")

    def test_stitch_raw_without_nef_uses_jpeg(self):
        self._jpeg("T_20260101_120000.jpg", "red")
        self._jpeg("R_20260101_120000.jpg", "blue")
        logs = []
        info = pano.stitch_stamp(
            "20260101_120000", overlap=0.25, flip_r=False, mode="blend",
            root=self.root, raw=True, on_log=logs.append,
        )
        self.assertNotEqual(info.get("source"), "raw")
        self.assertTrue(any("no NEF pair" in m for m in logs))

    def test_stitch_width(self):
        self._jpeg("T_20260101_120000.jpg", "red")
        self._jpeg("R_20260101_120000.jpg", "blue")
        info = pano.stitch_stamp(
            "20260101_120000", overlap=0.25, flip_r=False, mode="blend", root=self.root
        )
        self.assertEqual(info["width"], 70)
        self.assertEqual(info["height"], 20)
        self.assertTrue((self.root / "P_20260101_120000.jpg").is_file())
        rows = pano.list_pairs(self.root)
        self.assertEqual(rows[0]["pano"], "P_20260101_120000.jpg")
        self.assertEqual(rows[0]["stitch"].get("mode"), "blend")

    def test_cut_joins_both_frames(self):
        self._jpeg("T_20260101_120000.jpg", "red")
        self._jpeg("R_20260101_120000.jpg", "blue")
        info = pano.stitch_stamp(
            "20260101_120000", overlap=0.25, flip_r=False, mode="cut", root=self.root
        )
        self.assertEqual(info["width"], 70)
        self.assertEqual(info["height"], 20)
        dest = self.root / "P_20260101_120000.jpg"

        def chan(x, ch):
            return float(subprocess.check_output(
                ["magick", str(dest), "-format", f"%[fx:p{{{x},10}}.{ch}]", "info:"],
            ))

        # flopped-off: R left (blue), T right (red)
        self.assertGreater(chan(5, "b"), 0.7)
        self.assertGreater(chan(65, "r"), 0.7)

    def test_open_import(self):
        pano._venv_site()
        try:
            import cv2  # noqa: F401
        except ImportError:
            self.skipTest("cv2 not installed")
        self.assertTrue(callable(pano._sift_overlap_shift))

    def test_find_overlap_marker(self):
        full = self.root / "full.jpg"
        t = self.root / "t.jpg"
        r = self.root / "r.jpg"
        subprocess.run(
            ["magick", "-size", "136x40", "plasma:fractal", str(full)],
            check=True, capture_output=True,
        )
        subprocess.run(
            ["magick", str(full), "-crop", "80x40+56+0", "+repage", str(t)],
            check=True, capture_output=True,
        )
        subprocess.run(
            ["magick", str(full), "-crop", "80x40+0+0", "+repage", str(r)],
            check=True, capture_output=True,
        )
        found = pano.find_overlap(t, r, try_flip=False)
        self.assertFalse(found["flip_r"])
        self.assertGreater(found["overlap"], 0.20)
        self.assertLess(found["overlap"], 0.40)
        self.assertLess(abs(found["dy"]), 4)

    def test_sift_overlap_is_translation(self):
        pano._venv_site()
        try:
            import cv2
            import numpy as np
        except ImportError:
            self.skipTest("cv2 not installed")
        rng = np.random.default_rng(0)
        full = rng.integers(0, 256, (240, 900), dtype=np.uint8)
        t = self.root / "t.png"
        r = self.root / "r.png"
        tmp = self.root / "masks"
        tmp.mkdir()
        cv2.imwrite(str(r), full[:, :500])
        cv2.imwrite(str(t), full[:, 400:])
        tmask, rmask, _ = pano._overlap_feature_masks(500, 240, 0.20, tmp)
        found = pano._sift_overlap_shift(r, t, rmask, tmask)
        self.assertIsNotNone(found)
        self.assertAlmostEqual(found["overlap"], 0.20, delta=0.04)
        self.assertLess(abs(found["dy"]), 4)

    def test_subtract_ghost_kills_shifted_copy(self):
        scene = self.root / "scene.jpg"
        ghosted = self.root / "ghost.jpg"
        clean = self.root / "clean.jpg"
        subprocess.run(
            [
                "magick", "-size", "120x40", "xc:black",
                "-fill", "white", "-draw", "rectangle 70,8 95,32",
                str(scene),
            ],
            check=True, capture_output=True,
        )
        subprocess.run(
            [
                "magick", str(scene),
                "(", str(scene), "-roll", "-25+0", "-evaluate", "multiply", "0.2", ")",
                "-compose", "plus", "-composite", str(ghosted),
            ],
            check=True, capture_output=True,
        )
        pano.subtract_ghost(ghosted, clean, -25, 0, 0.2)

        def px(path, x, y):
            return float(subprocess.check_output(
                ["magick", str(path), "-format", f"%[fx:p{{{x},{y}}}]", "info:"],
            ))

        before = px(ghosted, 48, 20)
        after = px(clean, 48, 20)
        primary = px(clean, 80, 20)
        self.assertGreater(before, 0.08)
        self.assertLess(after, before * 0.45)
        self.assertGreater(primary, 0.7)

    def test_estimate_plate_ghost(self):
        pano._venv_site()
        try:
            import cv2  # noqa: F401
        except ImportError:
            self.skipTest("cv2 not installed")
        ghosted = self.root / "ghost.png"
        subprocess.run(
            [
                "magick", "-size", "240x120", "xc:black",
                "-fill", "white", "-draw", "rectangle 150,40 175,85",
                "(", "+clone", "-roll", "-28+0", "-evaluate", "multiply", "0.08", ")",
                "-compose", "plus", "-composite", str(ghosted),
            ],
            check=True, capture_output=True,
        )
        found = pano.estimate_plate_ghost(ghosted)
        self.assertIsNotNone(found)
        self.assertAlmostEqual(found["dx"], -28, delta=6)
        self.assertLess(abs(found["dy"]), 4)
        self.assertGreater(found["gain"], 0.03)
        self.assertLess(found["gain"], 0.11)

    def test_estimate_t_ghost_weaker_gain(self):
        pano._venv_site()
        try:
            import cv2  # noqa: F401
        except ImportError:
            self.skipTest("cv2 not installed")
        ghosted = self.root / "t_ghost.png"
        subprocess.run(
            [
                "magick", "-size", "240x120", "xc:black",
                "-fill", "white", "-draw", "rectangle 150,40 175,85",
                "(", "+clone", "-roll", "-28+0", "-evaluate", "multiply", "0.02", ")",
                "-compose", "plus", "-composite", str(ghosted),
            ],
            check=True, capture_output=True,
        )
        found = pano.estimate_plate_ghost(ghosted, tag="T")
        self.assertIsNotNone(found)
        self.assertAlmostEqual(found["dx"], -28, delta=8)
        self.assertGreater(found["gain"], 0.011)
        self.assertLess(found["gain"], 0.11)

    def test_overlap_scale_ignores_unique_halves(self):
        t = self.root / "t_bal.jpg"
        r = self.root / "r_bal.jpg"
        # Unique halves disagree (T bright, R dark) but the 20% overlap is
        # T gray vs R brighter — full-frame scale would go the wrong way.
        # R is left (unique then overlap), T is right (overlap then unique).
        subprocess.run(
            [
                "magick", "(", "-size", "20x40", "xc:#4d4d4d", ")",
                "(", "-size", "80x40", "xc:#999999", ")",
                "+append", str(t),
            ],
            check=True, capture_output=True,
        )
        subprocess.run(
            [
                "magick", "(", "-size", "80x40", "xc:#333333", ")",
                "(", "-size", "20x40", "xc:#808080", ")",
                "+append", str(r),
            ],
            check=True, capture_output=True,
        )
        full = pano._mean(t) / pano._mean(r)
        ol = pano._overlap_scale(t, r, overlap=0.20)
        self.assertGreater(full, 1.3)
        self.assertAlmostEqual(ol, 0.60, delta=0.08)
        dest = self.root / "r_scaled.jpg"
        used = pano._balance_r(t, r, dest, overlap=0.20)
        self.assertEqual(used, dest)
        self.assertAlmostEqual(pano._overlap_scale(t, dest, overlap=0.20), 1.0, delta=0.05)

    def test_lift_unique_brightens_t_east(self):
        t = self.root / "t_vig.jpg"
        subprocess.run(
            [
                "magick", "-size", "100x40", "xc:",
                "-sparse-color", "barycentric", "0,0 #808080 99,0 #222222",
                str(t),
            ],
            check=True, capture_output=True,
        )
        dest = self.root / "t_lift.jpg"
        used = pano._lift_unique(t, dest, east=True, overlap=0.20)
        self.assertEqual(used, dest)
        w, h = 100, 40
        before = pano._strip_mean(t, w, h, 92, 100)
        after = pano._strip_mean(dest, w, h, 92, 100)
        mid = pano._strip_mean(dest, w, h, 0, 20)
        self.assertGreater(after, before * 1.15)
        self.assertAlmostEqual(after, mid, delta=0.12)

    def test_disk_stats_counts_sets(self):
        self._jpeg("T_20260101_120000.jpg", "red")
        self._jpeg("R_20260101_120000.jpg", "blue")
        info = pano.disk_stats(self.root)
        self.assertGreater(info["free"], 0)
        self.assertGreaterEqual(info["sets"], 1)
        self.assertGreater(info["shots"], 0)

    def test_match_seam_scales_right(self):
        pano._venv_site()
        try:
            import cv2
            import numpy as np
        except ImportError:
            self.skipTest("cv2 not installed")
        img = np.zeros((80, 800, 3), dtype=np.uint8)
        img[:, :400] = 80
        img[:, 400:] = 140
        out, note = pano._match_seam_img(img)
        self.assertIn("seam", note)
        self.assertLess(float(out[:, 700].mean()), float(img[:, 700].mean()) - 5)

    def test_resolve_rejects_traversal(self):
        with self.assertRaises(dual.CamError):
            pano.resolve("../secret.jpg", self.root)

    def test_delete_stamp_and_side(self):
        self._jpeg("T_20260101_120000.jpg", "red")
        self._jpeg("R_20260101_120000.jpg", "blue")
        self._jpeg("P_20260101_120000.jpg", "green")
        pano.delete_stamp("20260101_120000", self.root, sides=["P"])
        self.assertFalse((self.root / "P_20260101_120000.jpg").is_file())
        self.assertTrue((self.root / "T_20260101_120000.jpg").is_file())
        pano.delete_stamp("20260101_120000", self.root)
        self.assertEqual(pano.list_pairs(self.root), [])

    def test_protect_blocks_delete(self):
        self._jpeg("T_20260101_120000.jpg", "red")
        self._jpeg("R_20260101_120000.jpg", "blue")
        self._jpeg("T_20260102_120000.jpg", "red")
        info = pano.set_protected("20260101_120000", True, self.root)
        self.assertTrue(info["protected"])
        by = {row["stamp"]: row for row in pano.list_pairs(self.root)}
        self.assertTrue(by["20260101_120000"]["protected"])
        self.assertFalse(by["20260102_120000"]["protected"])
        with self.assertRaises(dual.CamError):
            pano.delete_stamp("20260101_120000", self.root)
        gone = pano.delete_unprotected(self.root)
        self.assertEqual(gone["removed"], ["20260102_120000"])
        self.assertEqual(gone["skipped"], ["20260101_120000"])
        self.assertTrue((self.root / "T_20260101_120000.jpg").is_file())
        pano.set_protected("20260101_120000", False, self.root)
        pano.delete_stamp("20260101_120000", self.root)
        self.assertEqual(pano.list_pairs(self.root), [])

    def test_before_today_and_keep_last(self):
        self._jpeg("T_20260101_120000.jpg", "red")
        self._jpeg("R_20260101_120000.jpg", "blue")
        self._jpeg("T_20260911_100000.jpg", "red")
        self._jpeg("R_20260911_100000.jpg", "blue")
        self._jpeg("T_20260911_110000.jpg", "red")
        info = pano.delete_before_today(self.root, today="20260911")
        self.assertEqual(info["removed"], ["20260101_120000"])
        stamps = {row["stamp"] for row in pano.list_pairs(self.root)}
        self.assertEqual(stamps, {"20260911_100000", "20260911_110000"})
        for i in range(6):
            self._jpeg(f"T_20260911_12000{i}.jpg", "red")
        kept = pano.keep_last(5, self.root)
        self.assertEqual(kept["count"], 3)
        self.assertEqual(len(pano.list_pairs(self.root)), 5)

    def test_stitch_queue_serial(self):
        pano._jobs.clear()
        pano._queue.clear()
        gate = threading.Event()
        started = []

        def fake(stamp, **_kw):
            started.append(stamp)
            self.assertTrue(gate.wait(2))
            return {
                "stamp": stamp, "message": f"done {stamp}", "width": 1, "height": 1,
                "mode": "open", "overlap": 0.2, "overlap_frac": 0.2, "dy": 0,
                "flip_r": False, "file": f"P_{stamp}.jpg",
            }

        old = pano.stitch_stamp
        pano.stitch_stamp = fake
        try:
            first = pano.start_stitch("20260101_120000", mode="open", root=self.root)
            second = pano.start_stitch("20260101_130000", mode="open", root=self.root)
            self.assertEqual(first["phase"], "start")
            self.assertTrue(first["running"])
            self.assertEqual(second["phase"], "queued")
            stat = pano.queue_status()
            self.assertTrue(stat["running"])
            self.assertEqual(stat["queued"], 1)
            self.assertIn("queued", stat["message"])
            self.assertTrue(second["running"])
            with self.assertRaises(dual.CamError):
                pano.start_stitch("20260101_120000", mode="open", root=self.root)
            deadline = time.time() + 2
            while time.time() < deadline and started != ["20260101_120000"]:
                time.sleep(0.01)
            self.assertEqual(started, ["20260101_120000"])
            gate.set()
            deadline = time.time() + 2
            while time.time() < deadline:
                if pano.job_get("20260101_130000").get("phase") == "done":
                    break
                time.sleep(0.02)
            self.assertEqual(pano.job_get("20260101_120000")["phase"], "done")
            self.assertEqual(pano.job_get("20260101_130000")["phase"], "done")
            self.assertEqual(started, ["20260101_120000", "20260101_130000"])
        finally:
            gate.set()
            pano.stitch_stamp = old
            pano._jobs.clear()
            pano._queue.clear()


class CopyMaster(unittest.TestCase):
    def test_assignments_skip_flash(self):
        out = dual.assignments_from_status({
            "iso": "400",
            "isoauto": "Off",
            "shutterspeed": "1/125",
            "imagequality": "JPEG Fine",
            "whitebalance": "Auto",
            "exposurecompensation": "0",
            "expprogram": "M",
            "flashmode": "Fill flash",
            "flash": "On",
            "batterylevel": "75%",
            "serialnumber": "123",
            "capturetarget": "Memory card",
        })
        keys = [k for k, _ in out]
        self.assertEqual(
            keys,
            [
                "isoauto", "autoiso", "iso", "shutterspeed",
                "imagequality", "whitebalance", "exposurecompensation", "expprogram",
            ],
        )
        self.assertNotIn("flashmode", keys)
        self.assertNotIn("flash", keys)
        self.assertIn(("iso", "400"), out)
        self.assertIn(("exposurecompensation", "0"), out)
        self.assertIn(("expprogram", "M"), out)

    def test_assignments_auto_iso(self):
        keys = [k for k, _ in dual.assignments_from_status({
            "iso": "Auto", "isoauto": "On", "shutterspeed": "1/60",
        })]
        self.assertIn("isoauto", keys)
        self.assertNotIn("iso", keys)

    def test_autoiso_on_counts_as_auto(self):
        keys = [k for k, _ in dual.assignments_from_status({
            "iso": "6400", "isoauto": "Off", "autoiso": "On",
        })]
        self.assertIn("isoauto", keys)
        self.assertNotIn("iso", keys)

    def test_copy_from_master(self):
        calls = []

        def status(row):
            return {
                "iso": "200", "isoauto": "Off", "shutterspeed": "1/250",
                "whitebalance": "Auto", "imagequality": "JPEG Fine",
                "exposurecompensation": "0", "expprogram": "M",
                "flashmode": "Rear",
            }

        def set_one(port, assignments):
            calls.append((port, list(assignments)))
            return []

        old_status, old_set = dual._status_one, dual._set_one
        dual._status_one = status
        dual._set_one = set_one
        try:
            have = {
                "T": {"role": "T", "port": "usb:1", "model": "D7000"},
                "R": {"role": "R", "port": "usb:2", "model": "D7000"},
            }
            info = dual.copy_from_master(have, "T")
            self.assertEqual(info["master"], "T")
            self.assertEqual(info["slave"], "R")
            self.assertEqual(calls[0][0], "usb:2")
            self.assertNotIn("flashmode", [k for k, _ in calls[0][1]])
            self.assertIn("T → R", info["message"])
        finally:
            dual._status_one = old_status
            dual._set_one = old_set

    def test_lock_from_master_freezes_auto_iso(self):
        packs = []
        af = []

        def status(row):
            if row.get("role") == "T":
                return {
                    "iso": "200", "isoauto": "On", "autoiso": "On",
                    "shutterspeed": "1/125", "whitebalance": "Auto",
                    "imagequality": "JPEG Fine",
                    "exposurecompensation": "0.3",
                }
            return {
                "iso": "200", "isoauto": "Off", "autoiso": "Off",
                "shutterspeed": "1/125", "exposurecompensation": "0",
            }

        def apply(port, assignments, timeout=20):
            packs.append((port, list(assignments)))
            return []

        def prep(port):
            af.append(port)

        old_status = dual._status_one
        old_apply = dual.apply_locked
        old_prep = dual.prepare_shot
        dual._status_one = status
        dual.apply_locked = apply
        dual.prepare_shot = prep
        try:
            have = {
                "T": {"role": "T", "port": "usb:1", "model": "D7000"},
                "R": {"role": "R", "port": "usb:2", "model": "D7000"},
            }
            info = dual.lock_from_master(have, "T")
            self.assertEqual(af, ["usb:1"])
            keys = {k: v for k, v in info["assignments"]}
            self.assertEqual(keys["isoauto"], "Off")
            self.assertEqual(keys["iso"], "200")
            self.assertEqual(keys["shutterspeed"], "1/125")
            self.assertEqual(keys["exposurecompensation"], "0.3")
            self.assertEqual({p for p, _ in packs}, {"usb:1", "usb:2"})
            self.assertEqual(packs[0][1], packs[1][1])
            self.assertIn("lock T", info["message"])
        finally:
            dual._status_one = old_status
            dual.apply_locked = old_apply
            dual.prepare_shot = old_prep

    def test_pick_clock_drops_nikon_2010(self):
        pi = dual.datetime(2026, 9, 17, 0, 20, 0)
        dead = dual.datetime(2010, 1, 5, 21, 40, 12)
        src, when = dual.pick_clock({"pi": pi, "T": dead, "R": dead})
        self.assertEqual(src, "pi")
        self.assertEqual(when, pi)
        newer = dual.datetime(2026, 9, 17, 0, 25, 0)
        src, when = dual.pick_clock({"pi": pi, "T": newer, "R": dead})
        self.assertEqual(src, "T")
        self.assertEqual(when, newer)
        src, when = dual.pick_clock({
            "pi": dual.datetime(1970, 1, 1), "T": newer, "R": dead,
        })
        self.assertEqual(src, "T")

    def test_parse_cam_time(self):
        dt = dual.parse_cam_time("2010:01:05 21:40:12")
        self.assertEqual(dt.year, 2010)
        self.assertFalse(dual.plausible_time(dt))
        unix = dual.parse_cam_time(str(int(dual.datetime(2026, 9, 17, 12, 0).timestamp())))
        self.assertEqual(unix.year, 2026)


class Settings(unittest.TestCase):
    def setUp(self):
        root = Path(tempfile.mkdtemp())
        self.addCleanup(lambda: shutil.rmtree(root, ignore_errors=True))
        self._old = settings.PATH
        settings.PATH = root / "settings.json"
        self.addCleanup(lambda: setattr(settings, "PATH", self._old))

    def test_pi_defaults_both_on(self):
        self.assertEqual(
            settings.load(pi=True),
            {
                "download": True, "gpio": True, "flip_r": False, "overlap": 0.20,
                "sync": True, "lock_t": True, "master": "T", "preview_s": 10,
                "idle_min": 10, "deghost": False, "balance": True, "follow_cam": False, "bulb": False,
                "stitch_mode": "hugin", "crop_inner": True, "ana_squeeze": 1.0,
                "keep_card": False, "stitch_raw": False, "raw_look": True,
            },
        )

    def test_mac_defaults_both_off(self):
        self.assertEqual(
            settings.load(pi=False),
            {
                "download": False, "gpio": False, "flip_r": False, "overlap": 0.20,
                "sync": True, "lock_t": True, "master": "T", "preview_s": 10,
                "idle_min": 10, "deghost": False, "balance": True, "follow_cam": False, "bulb": False,
                "stitch_mode": "open", "crop_inner": True, "ana_squeeze": 1.0,
                "keep_card": False, "stitch_raw": False, "raw_look": True,
            },
        )

    def test_save_survives_reload(self):
        settings.save(
            {"download": False, "gpio": True, "flip_r": True, "overlap": 0.25},
            pi=True,
        )
        self.assertEqual(
            settings.load(pi=True),
            {
                "download": False, "gpio": True, "flip_r": True, "overlap": 0.25,
                "sync": True, "lock_t": True, "master": "T", "preview_s": 10,
                "idle_min": 10, "deghost": False, "balance": True, "follow_cam": False, "bulb": False,
                "stitch_mode": "hugin", "crop_inner": True, "ana_squeeze": 1.0,
                "keep_card": False, "stitch_raw": False, "raw_look": True,
            },
        )
        settings.save({"download": True}, pi=True)
        self.assertEqual(settings.load(pi=True)["overlap"], 0.25)
        self.assertTrue(settings.load(pi=True)["flip_r"])

    def test_overlap_percent(self):
        settings.save({"overlap": 18}, pi=True)
        self.assertEqual(settings.load(pi=True)["overlap"], 0.18)

    def test_master_and_sync(self):
        settings.save({"master": "R", "sync": False}, pi=True)
        self.assertEqual(settings.load(pi=True)["master"], "R")
        self.assertFalse(settings.load(pi=True)["sync"])
        settings.save({"master": "X"}, pi=True)
        self.assertEqual(settings.load(pi=True)["master"], "R")

    def test_deghost_and_follow_cam(self):
        settings.save({"deghost": True, "follow_cam": True}, pi=True)
        got = settings.load(pi=True)
        self.assertTrue(got["deghost"])
        self.assertTrue(got["follow_cam"])

    def test_crop_inner_setting(self):
        self.assertTrue(settings.load(pi=True)["crop_inner"])
        settings.save({"crop_inner": False}, pi=True)
        self.assertFalse(settings.load(pi=True)["crop_inner"])

    def test_ana_squeeze_setting(self):
        self.assertEqual(settings.load(pi=True)["ana_squeeze"], 1.0)
        settings.save({"ana_squeeze": 2}, pi=True)
        self.assertEqual(settings.load(pi=True)["ana_squeeze"], 2.0)
        settings.save({"ana_squeeze": "off"}, pi=True)
        self.assertEqual(settings.load(pi=True)["ana_squeeze"], 1.0)
        settings.save({"ana_squeeze": 1.33}, pi=True)
        self.assertEqual(settings.load(pi=True)["ana_squeeze"], 1.33)

    def test_lock_t_and_idle_min(self):
        self.assertTrue(settings.load(pi=True)["lock_t"])
        self.assertEqual(settings.load(pi=True)["idle_min"], 10)
        settings.save({"lock_t": False, "idle_min": 0}, pi=True)
        got = settings.load(pi=True)
        self.assertFalse(got["lock_t"])
        self.assertEqual(got["idle_min"], 0)
        settings.save({"idle_min": 99}, pi=True)
        self.assertEqual(settings.load(pi=True)["idle_min"], 0)

    def test_brightness_persists(self):
        settings.save({"brightness": 40}, pi=True)
        self.assertEqual(settings.load(pi=True)["brightness"], 40)
        settings.save({"download": False}, pi=True)
        self.assertEqual(settings.load(pi=True)["brightness"], 40)
        settings.save({"brightness": 0}, pi=True)
        self.assertEqual(settings.load(pi=True)["brightness"], 40)

    def test_preview_and_exposure(self):
        settings.save({"preview_s": 4, "iso": "800", "shutter": "1/250", "fstop": "f/8"}, pi=True)
        got = settings.load(pi=True)
        self.assertEqual(got["preview_s"], 4)
        self.assertEqual(got["iso"], "800")
        self.assertEqual(got["shutter"], "1/250")
        self.assertEqual(got["fstop"], "8")
        settings.save({"download": False}, pi=True)
        self.assertEqual(settings.load(pi=True)["preview_s"], 4)
        settings.save({"preview_s": 0}, pi=True)
        self.assertEqual(settings.load(pi=True)["preview_s"], 0)
        settings.save({"iso": "Auto", "shutter": "Auto"}, pi=True)
        got = settings.load(pi=True)
        self.assertEqual(got["iso"], "Auto")
        self.assertEqual(got["shutter"], "Auto")
        settings.save({"download": True}, pi=True)
        self.assertEqual(settings.load(pi=True)["iso"], "Auto")
        self.assertEqual(settings.load(pi=True)["shutter"], "Auto")

    def test_shoot_target(self):
        self.assertEqual(
            settings.shoot_target({"gpio": True, "download": True}, {"available": True}),
            "gpio",
        )
        self.assertEqual(
            settings.shoot_target({"gpio": True, "download": True}, {"available": False}),
            "download",
        )
        self.assertEqual(
            settings.shoot_target({"gpio": False, "download": False}, {"available": True}),
            "card",
        )


class Brightness(unittest.TestCase):
    def test_parse_getvcp(self):
        cur, mx = brightness.parse_getvcp(bytes([
            0x6E, 0x88, 0x02, 0x00, 0x10, 0x00, 0x00, 0x64, 0x00, 0x06, 0xC6,
        ]))
        self.assertEqual((cur, mx), (6, 100))

    def test_clamp(self):
        self.assertEqual(brightness.clamp(6), 6)
        self.assertEqual(brightness.clamp(0), 1)
        self.assertEqual(brightness.clamp(140), 100)
        self.assertIsNone(brightness.clamp("x"))

    def test_invert(self):
        self.assertEqual(brightness.invert(6, 100), 94)
        self.assertEqual(brightness.invert(94, 100), 6)
        self.assertEqual(brightness.invert(100, 100), 1)

    def test_find_bus(self):
        root = Path(tempfile.mkdtemp())
        self.addCleanup(lambda: shutil.rmtree(root, ignore_errors=True))
        a = root / "card1-HDMI-A-1"
        b = root / "card1-HDMI-A-2"
        a.mkdir(); b.mkdir()
        (a / "status").write_text("disconnected\n")
        (b / "status").write_text("connected\n")
        i2c = root / "i2c-21"
        i2c.mkdir()
        (b / "ddc").symlink_to(i2c)
        self.assertEqual(brightness.find_bus(root), 21)
        self.assertIsNone(brightness.find_bus(root / "missing"))
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
